keycard-tech/keycard-shell/hardware/shell/serial_run/CERTIFICATION-OFFICIALCERTIFICATES/Formal/EMC/2511B0394SHA-V1.pdf

This Verification is for the exclusive use of Intertek's client and is provided pursuant to the agreement between Intertek and its Client. Intertek's responsibility and liability are limited to the terms and conditions of the agreement. Intertek assumes no liability to any party, other than to the Client in accordance with the agreement, for any loss, expense or damage occasioned by the use of this Verification. Only the Client is authorized to permit copying or distribution of this Verification. Any use of the Intertek name or one of its marks for the sale or advertisement of the tested material, product or service must first be approved in writing by Intertek. The observations and test/inspection results referenced in this Verification are relevant only to the sample tested/inspected. This Verification by itself does not imply that the material, product, or service is or has ever been under an Intertek certification program.

Intertek | Page 1 of 1 | GFT-OP-11a (09 March 2024)

# Test Verification of Conformity

# Verification Number: 2511B0394SHA-V1

Applicant Name & Address: | Status Research & Development GmbH Baarerstrasse 10, 6302 Zug, Switzerland
Product Description: | Smart card adapter
Ratings & Principle Characteristics: | Input: 5VDC 1A (USBc), Battery: 3.7VDC 800mAh
Models/Type References: | Shell
Brand Names: | Keycard
Specification<s>/Standards: | 47CFR Part 15 (2024) ANSI C63.4 (2014) +A1 (2017) ICES-003 Issue 7
Verification Issuing Office Name & Address: | Intertek Testing Services (Shanghai FTZ) Co., Ltd. Building No.86, 1198 Qinzhou Road (North), Caohejing Development Zone, Shanghai 200233, China
Date of Tests: | October 22, 2025
Test Report Number(s): | 2511B0394SHA-001

# Signature

# Name: Edwin Xu Position: Assistant Manager Date: November 26, 2025

On the basis of the tests undertaken, the sample<s> of the below product has been tested by an accredited 3rd party laboratory in accordance to the referenced specification<s>/standard<s> at the time the tests were carried out. This verification is part of the full test report<s> and should be read in conjunction with it <them>.
