keycard-tech/keycard-shell/hardware/shell/serial_run/MECHANICAL/3Ddrawings/2282-008-WINDOWADHESIVE-V01-20250630.STEP

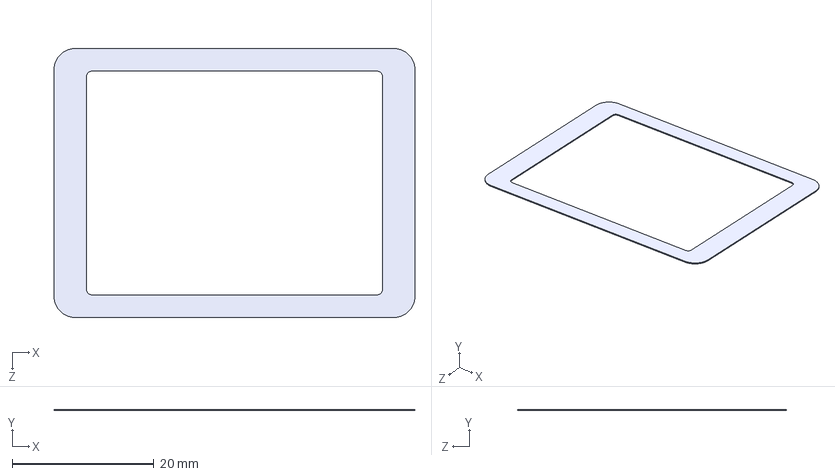
[picture p22: CAD file, 2026-01-29]
hardware/shell/serial_run/MECHANICAL/3Ddrawings/2282-008-WINDOWADHESIVE-V01-20250630.STEP
51.0 x 0.2 x 38.0 mm
