keycard-tech/keycard-shell/hardware/shell/serial_run/MECHANICAL/3Ddrawings/2282-012-WINDOWPROTECTION-V01-20250718.STEP

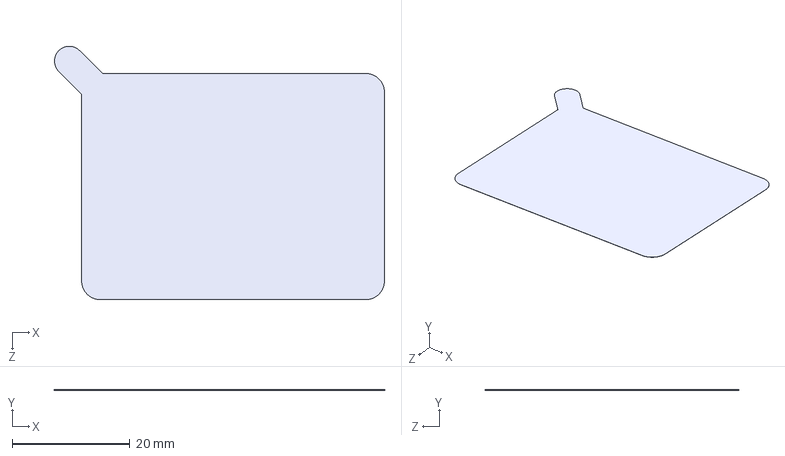
[picture p24: CAD file, 2026-01-29]
hardware/shell/serial_run/MECHANICAL/3Ddrawings/2282-012-WINDOWPROTECTION-V01-20250718.STEP
56.0 x 0.03 x 43.0 mm
