keycard-tech/keycard-shell/hardware/shell/serial_run/MECHANICAL/2282-011-CAMERAFOAM-V02-20250630.PDF

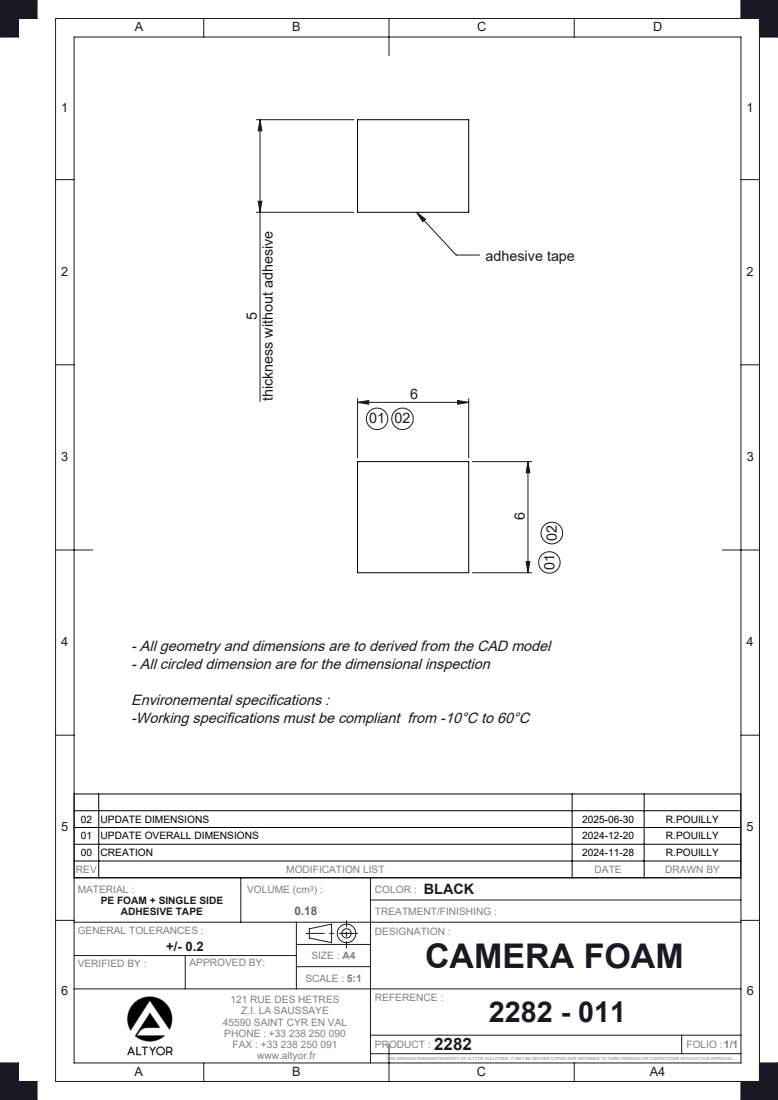
[picture p41: page 1]
adhesive tape; SCALE :; SIZE : A4; TREATMENT/FINISHING :

thickness without adhesive

- All geometry and dimensions are to derived from the CAD model
- All circled dimension are for the dimensional inspection
Environemental specifications :
-Working specifications must be compliant from -10°C to 60°C

02 | UPDATE DIMENSIONS | 2025-06-30 | R.POUILLY
01 | UPDATE OVERALL DIMENSIONS | 2024-12-20 | R.POUILLY
00 | CREATION | 2024-11-28 | R.POUILLY
REV | MODIFICATION LIST | DATE | DRAWN BY
MATERIAL : PE FOAM + SINGLE SIDE ADHESIVE TAPE | VOLUME (cm3) : 0.18 | BLACK COLOR :

GENERAL TOLERANCES : +/- 0.2 | | DESIGNATION : CAMERA FOAM

VERIFIED BY : | APPROVED BY:

121 RUE DES HETRES Z.I. LA SAUSSAYE 45590 SAINT CYR EN VAL PHONE : +33 238 250 090 FAX : +33 238 250 091 www.altyor.fr | REFERENCE : 2282 - 011

PRODUCT : | FOLIO : 1/1

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
