keycard-tech/keycard-shell/hardware/shell/serial_run/MECHANICAL/2282-012-WINDOWPROTECTION-V01-20250718.PDF

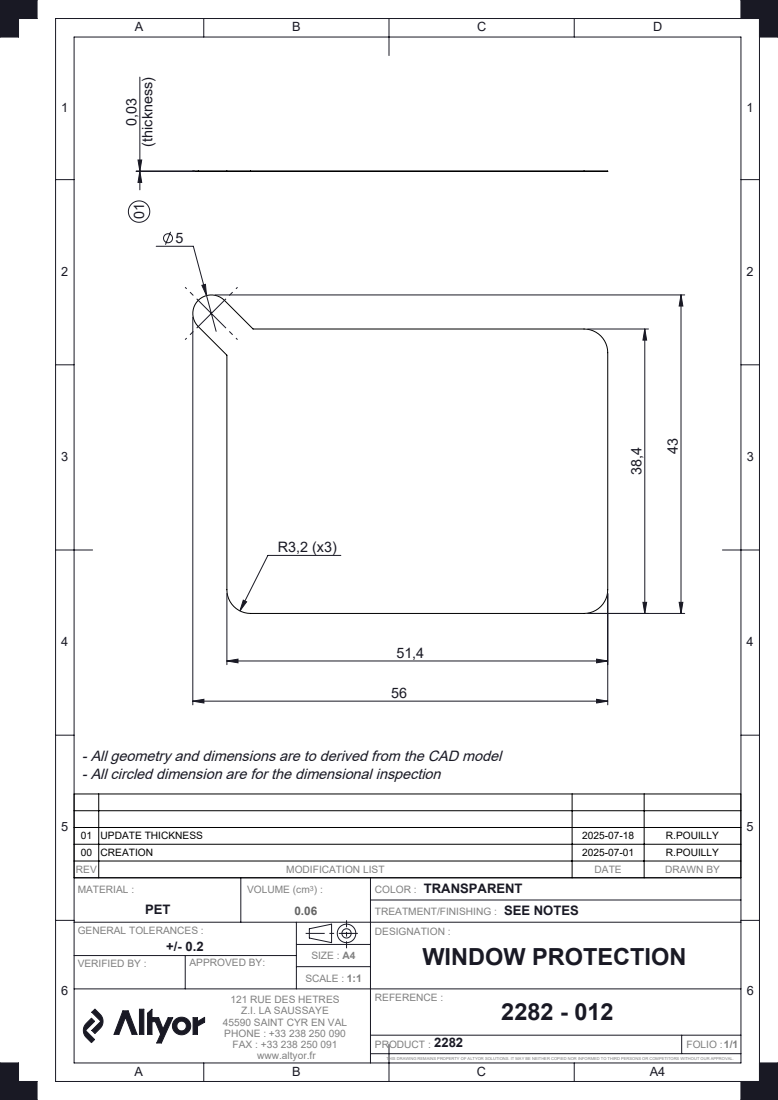
[picture p42: page 1]
SCALE :; SIZE : A4; MATERIAL :; VOLUME (cm3) :; COLOR :; TREATMENT/FINISHING :; PET; SEE NOTES

- All circled dimension are for the dimensional inspection 01

- All geometry and dimensions are to derived from the CAD model

01 | UPDATE THICKNESS | 2025-07-18 | R.POUILLY
00 | CREATION | 2025-07-01 | R.POUILLY
REV | MODIFICATION LIST | DATE | DRAWN BY

GENERAL TOLERANCES : +/- 0.2 | | DESIGNATION : WINDOW PROTECTION

VERIFIED BY : | APPROVED BY:

121 RUE DES HETRES Z.I. LA SAUSSAYE 45590 SAINT CYR EN VAL PHONE : +33 238 250 090 FAX : +33 238 250 091 www.altyor.fr | REFERENCE : 2282 - 012

2282 PRODUCT : | FOLIO : 1/1

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
