keycard-tech/keycard-shell/hardware/shell/serial_run/MECHANICAL/2282-005-KEYBOARDSLEEVE-V07-20250325.PDF

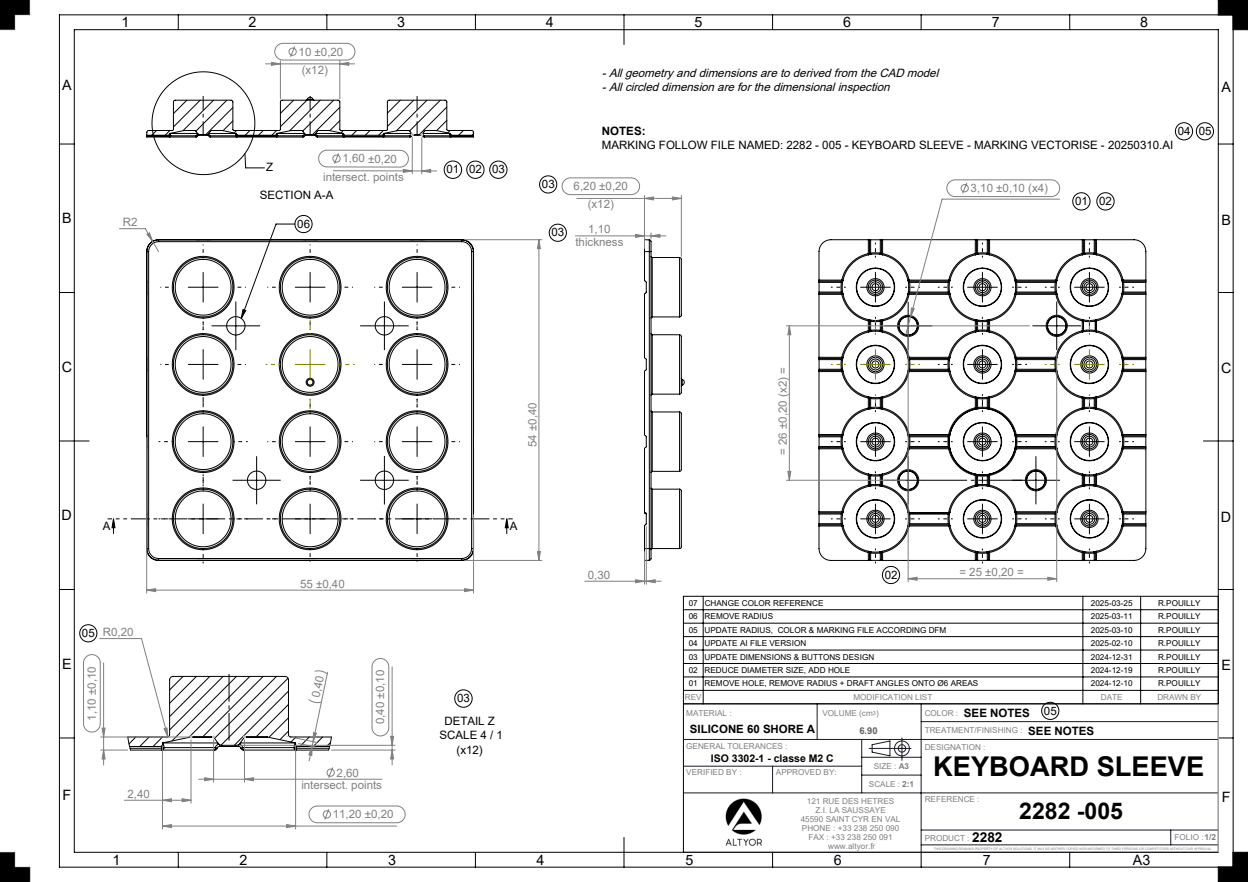
[picture p43: page 1]
1,60 ±0,20 intersect. points SECTION A-A; intersect. points 2,40; DETAIL Z SCALE 4 / 1; SILICONE 60 SHORE A; SEE NOTES; TREATMENT/FINISHING :; VOLUME (cm3); COLOR :; MATERIAL :; SIZE : A3; SCALE :

- All geometry and dimensions are to derived from the CAD model
- All circled dimension are for the dimensional inspection

NOTES:
MARKING FOLLOW FILE NAMED: 2282 - 005 - KEYBOARD SLEEVE - MARKING VECTORISE - 20250310.AI

07 | CHANGE COLOR REFERENCE | 2025-03-25 | R.POUILLY
06 | REMOVE RADIUS | 2025-03-11 | R.POUILLY
05 | UPDATE RADIUS, COLOR & MARKING FILE ACCORDING DFM | 2025-03-10 | R.POUILLY
04 | UPDATE AI FILE VERSION | 2025-02-10 | R.POUILLY
03 | UPDATE DIMENSIONS & BUTTONS DESIGN | 2024-12-31 | R.POUILLY
02 | REDUCE DIAMETER SIZE, ADD HOLE | 2024-12-19 | R.POUILLY
01 | REMOVE HOLE, REMOVE RADIUS + DRAFT ANGLES ONTO Ø6 AREAS | 2024-12-10 | R.POUILLY
REV | MODIFICATION LIST | DATE | DRAWN BY

GENERAL TOLERANCES : ISO 3302-1 - classe M2 C | | DESIGNATION : KEYBOARD SLEEVE

VERIFIED BY : | APPROVED BY:

121 RUE DES HETRES Z.I. LA SAUSSAYE 45590 SAINT CYR EN VAL PHONE : +33 238 250 090 FAX : +33 238 250 091 www.altyor.fr | REFERENCE : 2282 -005

2282 PRODUCT : | FOLIO : 1/2

THIS DRAWING REMAINS PROPERTY OF ALTYOR SOLUTIONS. IT MAY BE NEITHER COPIED NOR INFORMED TO THIRD PERSONS OR COMPETITORS WITHOUT OUR APPROVAL.

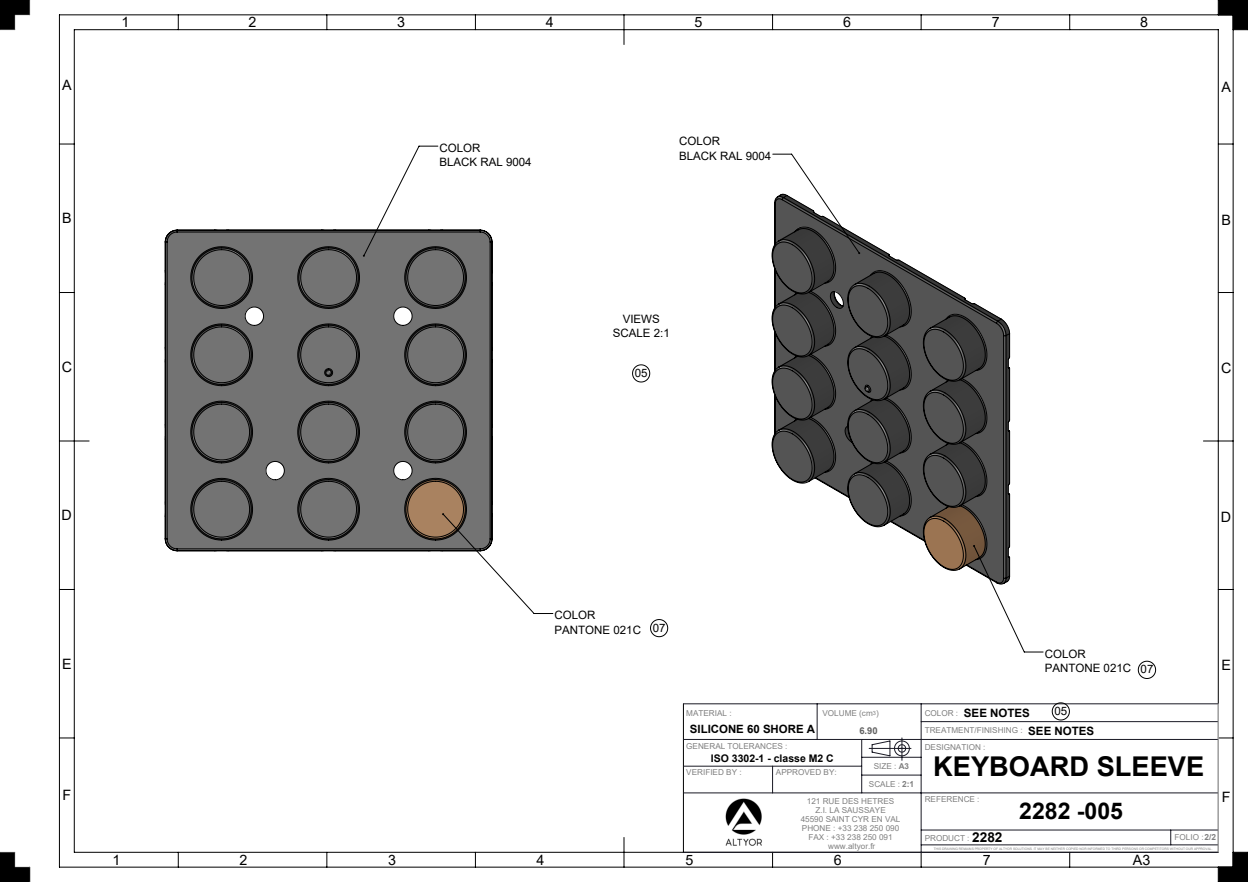
[picture p44: page 2]
BLACK RAL 9004; PANTONE 021C; SCALE 2:1; SILICONE 60 SHORE A; SEE NOTES; TREATMENT/FINISHING :; VOLUME (cm3); COLOR :; MATERIAL :; SIZE : A3; SCALE :

GENERAL TOLERANCES : ISO 3302-1 - classe M2 C | | | DESIGNATION : KEYBOARD SLEEVE

VERIFIED BY : | APPROVED BY:

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

2282 PRODUCT : | FOLIO : 2/2

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
