keycard-tech/keycard-shell/hardware/shell/serial_run/MECHANICAL/2282-010-CAMERAWINDOWADHESIVE-V00-20241128.PDF

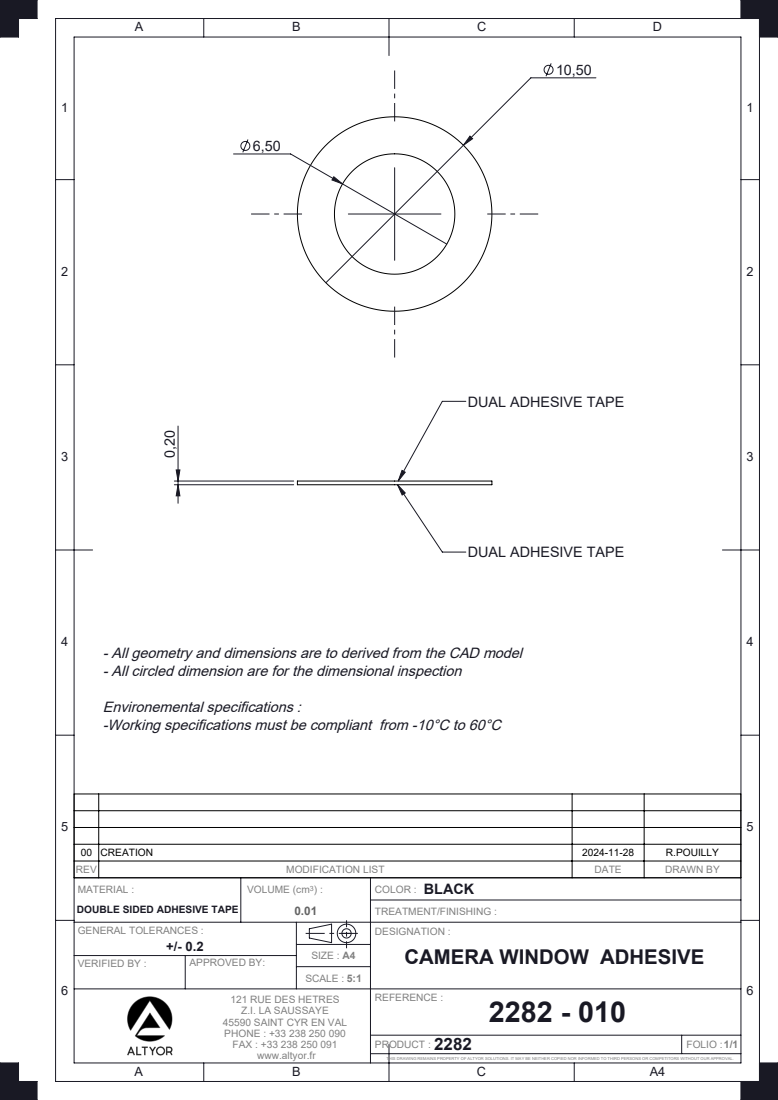
[picture p45: page 1]
SCALE :; SIZE : A4; TREATMENT/FINISHING :

DUAL ADHESIVE TAPE

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

00 | CREATION | 2024-11-28 | R.POUILLY
REV | MODIFICATION LIST | DATE | DRAWN BY
MATERIAL : DOUBLE SIDED ADHESIVE TAPE | VOLUME (cm3) : 0.01 | BLACK COLOR :

GENERAL TOLERANCES : +/- 0.2 | | DESIGNATION : CAMERA WINDOW ADHESIVE

VERIFIED BY : | APPROVED BY:

121 RUE DES HETRES Z.I. LA SAUSSAYE 45590 SAINT CYR EN VAL PHONE : +33 238 250 090 FAX : +33 238 250 091 www.altyor.fr | REFERENCE : 2282 - 010

PRODUCT : | FOLIO : 1/1

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
