keycard-tech/keycard-shell/hardware/shell/serial_run/ELECTRONIC/KCP-2282-SCH-V3.8/KCP-2282-600SCHV3.9.PDF

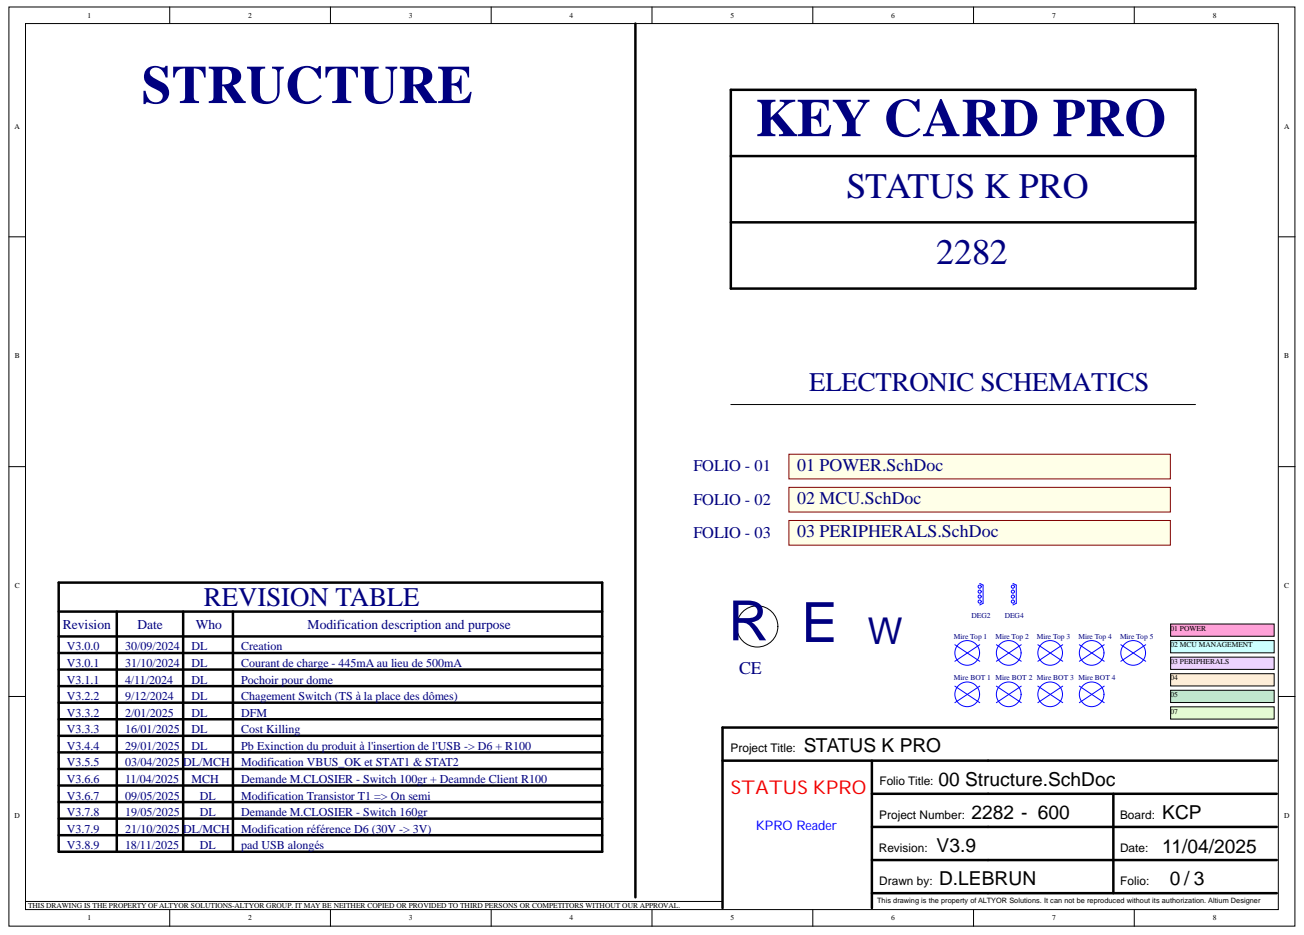
[picture p46: page 1]

Revision | Date | Who | Modification description and purpose

V3.0.0 | 30/09/2024 | DL | Creation

Mire BOT 1 Mire BOT 2

Mire BOT 3 Mire BOT 4

V3.3.2 | 2/01/2025 | DL | DFM
V3.3.3 | 16/01/2025 | DL | Cost Killing
V3.4.4 | 29/01/2025 | DL | Pb Exinction du produit à l'insertion de l'USB -> D6 + R100
V3.5.5 | 03/04/2025 DL/MCH | | Modification VBUS_OK et STAT1 & STAT2
V3.6.6 | 11/04/2025 | MCH | Demande M.CLOSIER - Switch 100gr + Deamnde Client R100
V3.6.7 | 09/05/2025 | DL | Modification Transistor T1 => On semi
V3.7.8 | 19/05/2025 | DL | Demande M.CLOSIER - Switch 160gr
V3.7.9 | 21/10/2025 DL/MCH | | Modification référence D6 (30V -> 3V)
V3.8.9 | 18/11/2025 | DL | pad USB alongés

This drawing is the property of ALTYOR Solutions. It can not be reproduced without its authorization. Altium Designer

THIS DRAWING IS THE PROPERTY OF ALTYOR SOLUTIONS-ALTYOR GROUP. IT MAY BE NEITHER COPIED OR PROVIDED TO THIRD PERSONS OR COMPETITORS WITHOUT OUR APPROVAL.

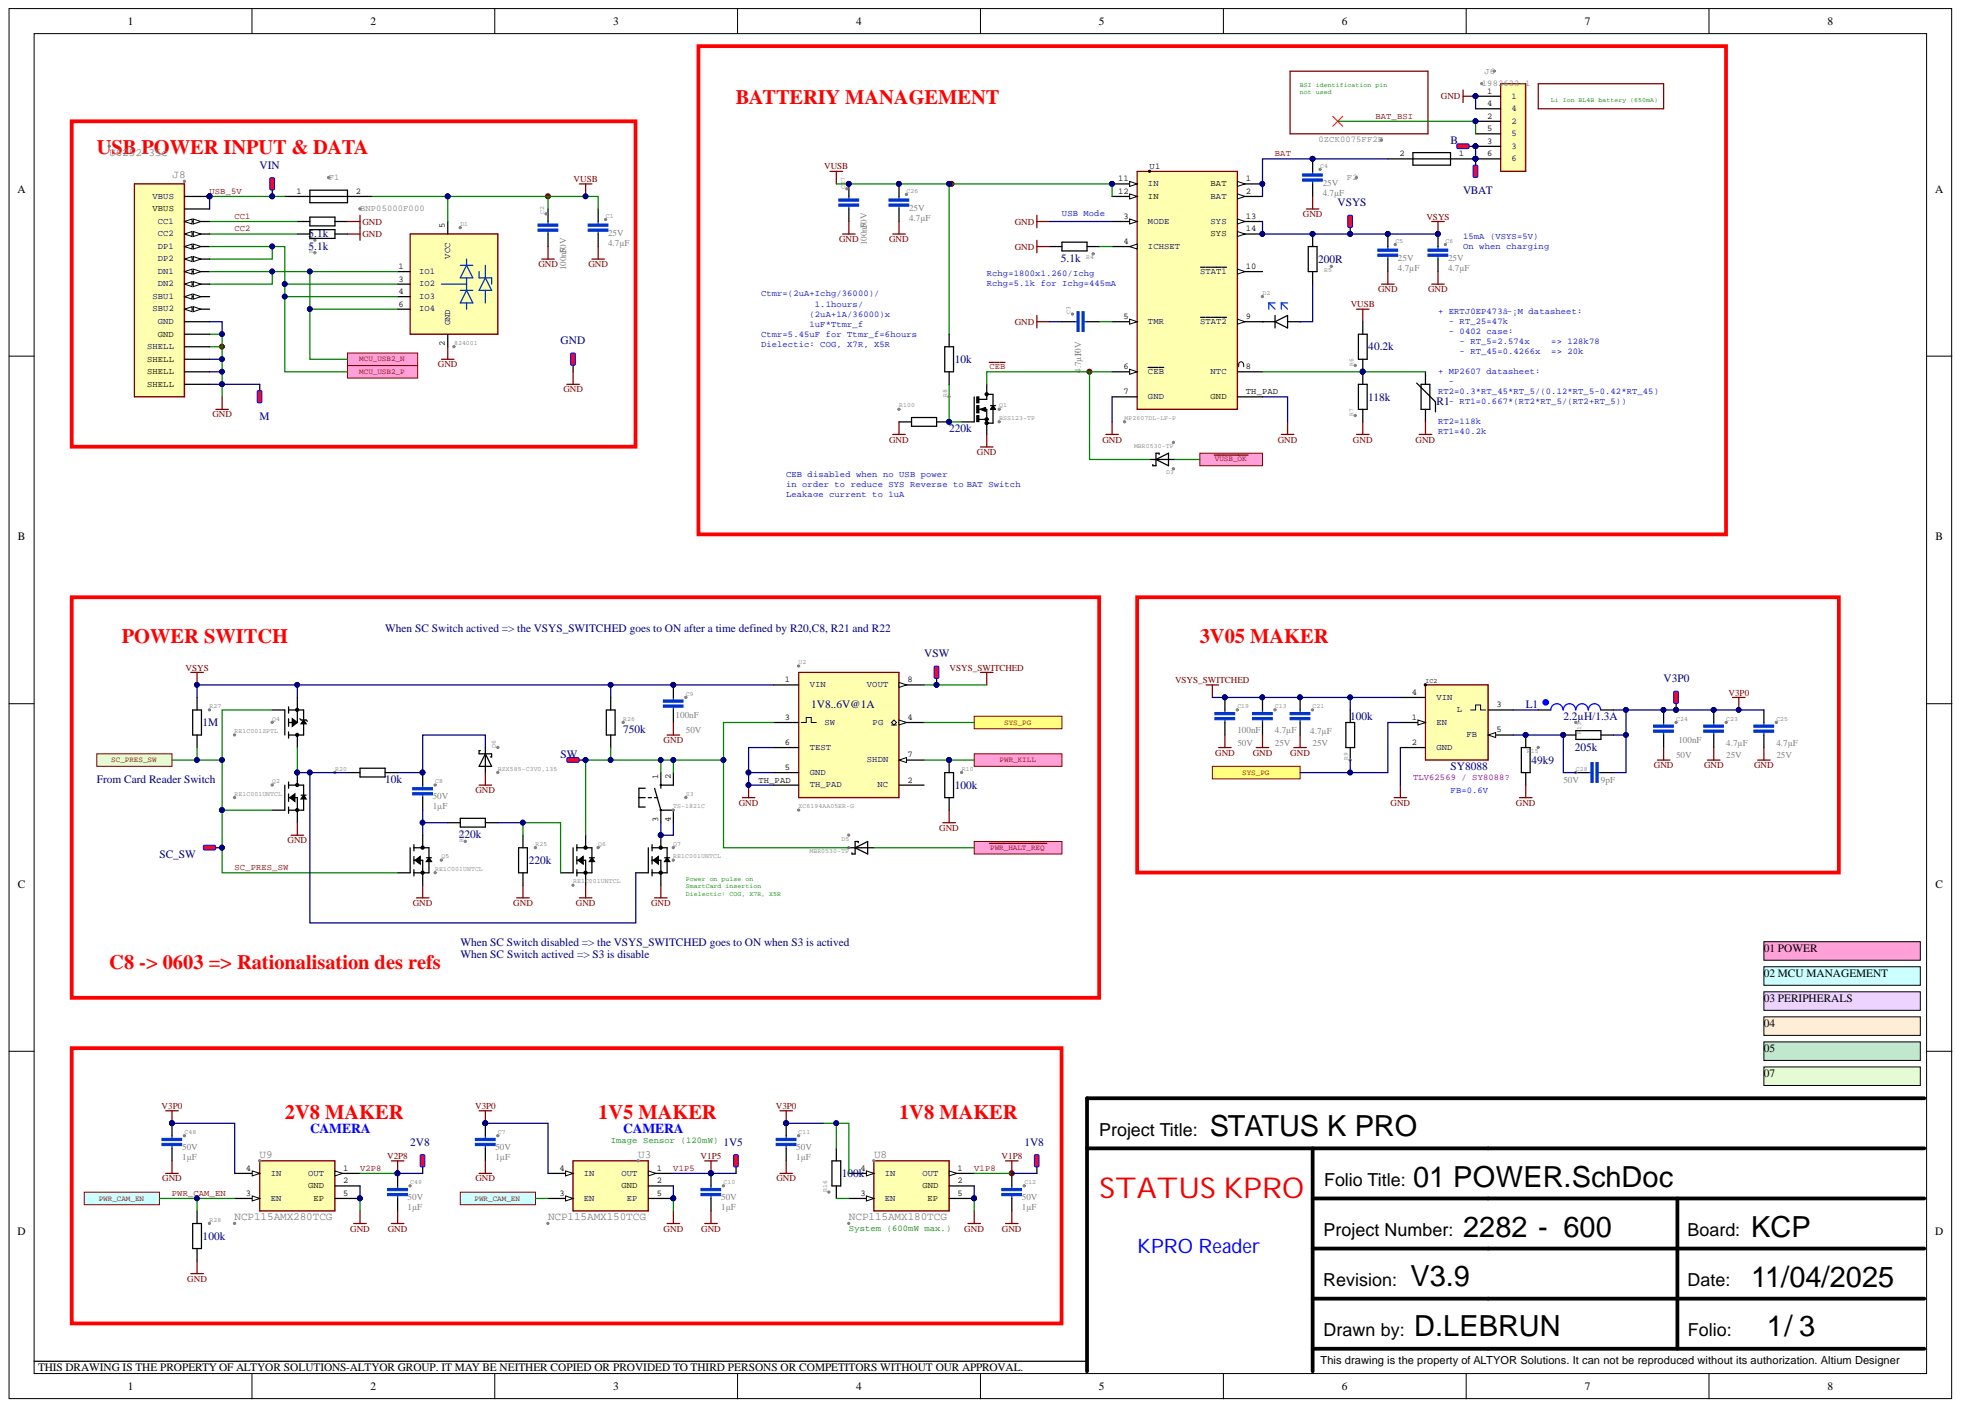
[picture p47: page 2]

USB POWER INPUT & DATA

D3 | VUSB_OK

CEB disabled when no USB power
in order to reduce SYS Reverse to BAT Switch
Leakage current to 1uA

When SC Switch actived => the VSYS_SWITCHED goes to ON after a time defined by R20,C8, R21 and R22

SC_PRES_SW
From Card Reader Switch

Power on pulse on
SmartCard insertion
Dielectic: COG, X7R, X5R

When SC Switch disabled => the VSYS_SWITCHED goes to ON when S3 is actived
When SC Switch actived => S3 is disable

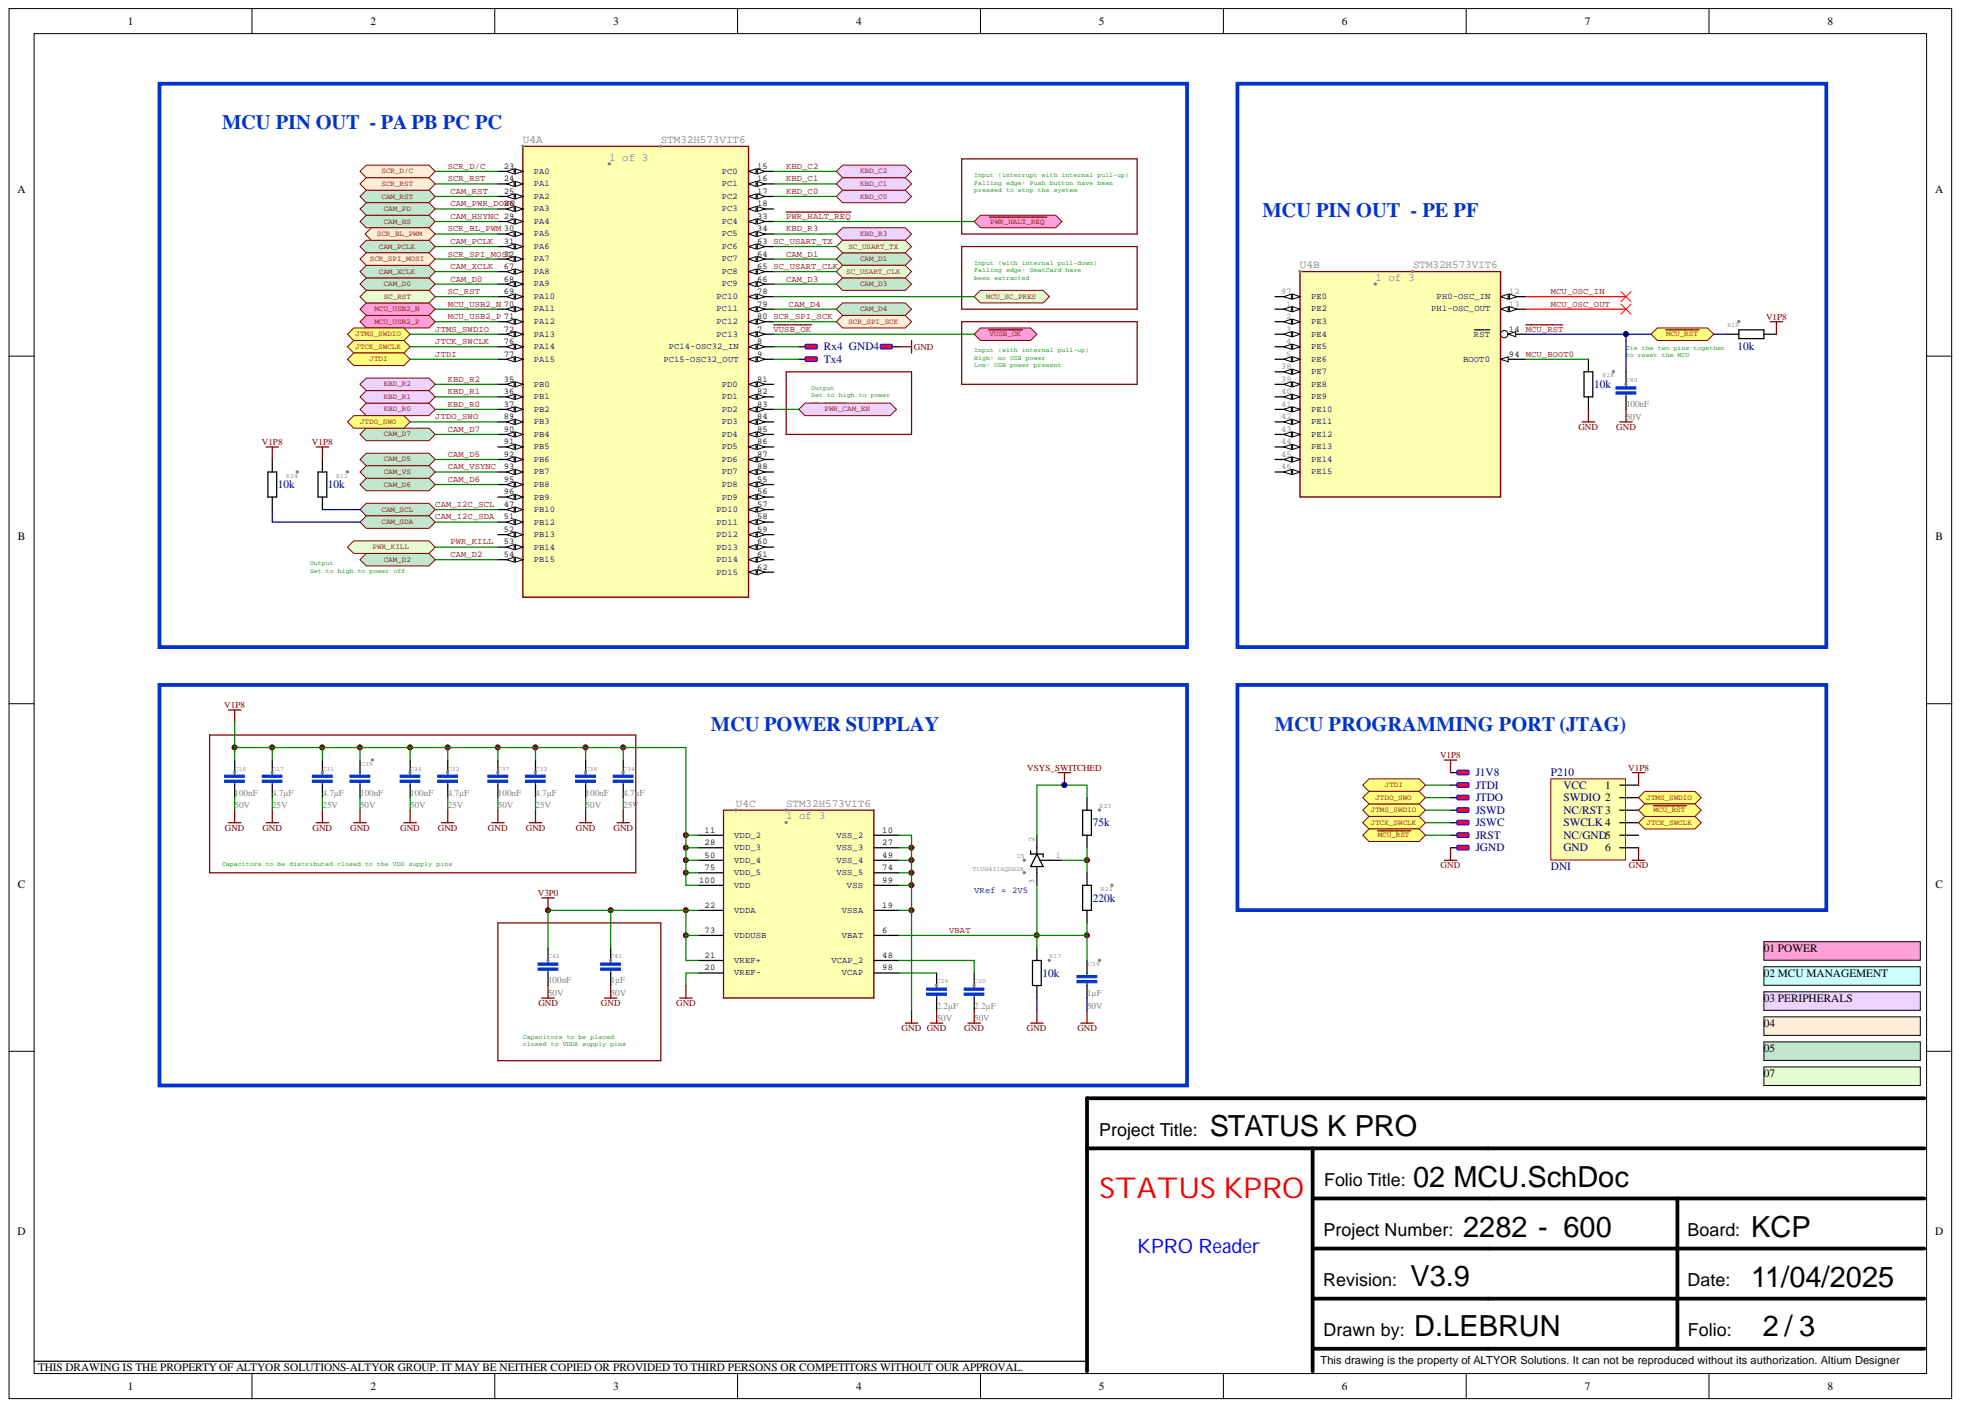
[picture p48: page 3]

MCU PIN OUT - PA PB PC PC

Input (interrupt with internal pull-up)
Falling edge: Push button have been
pressed to stop the system

MCU PIN OUT - PE PF

Input (with internal pull-down)
Falling edge: SmatCard have
been extracted

Input (with internal pull-up)
High: no USB power
Low: USB power present

Tie the two pins together
to reset the MCU

Output
Set to high to power
on camera
PWR_CAM_EN

Set to high to power off

Capacitors to be distributed closed to the VDD supply pins

VREF+ 21
VREF- 20

Capacitors to be placed
closed to VDDA supply pins

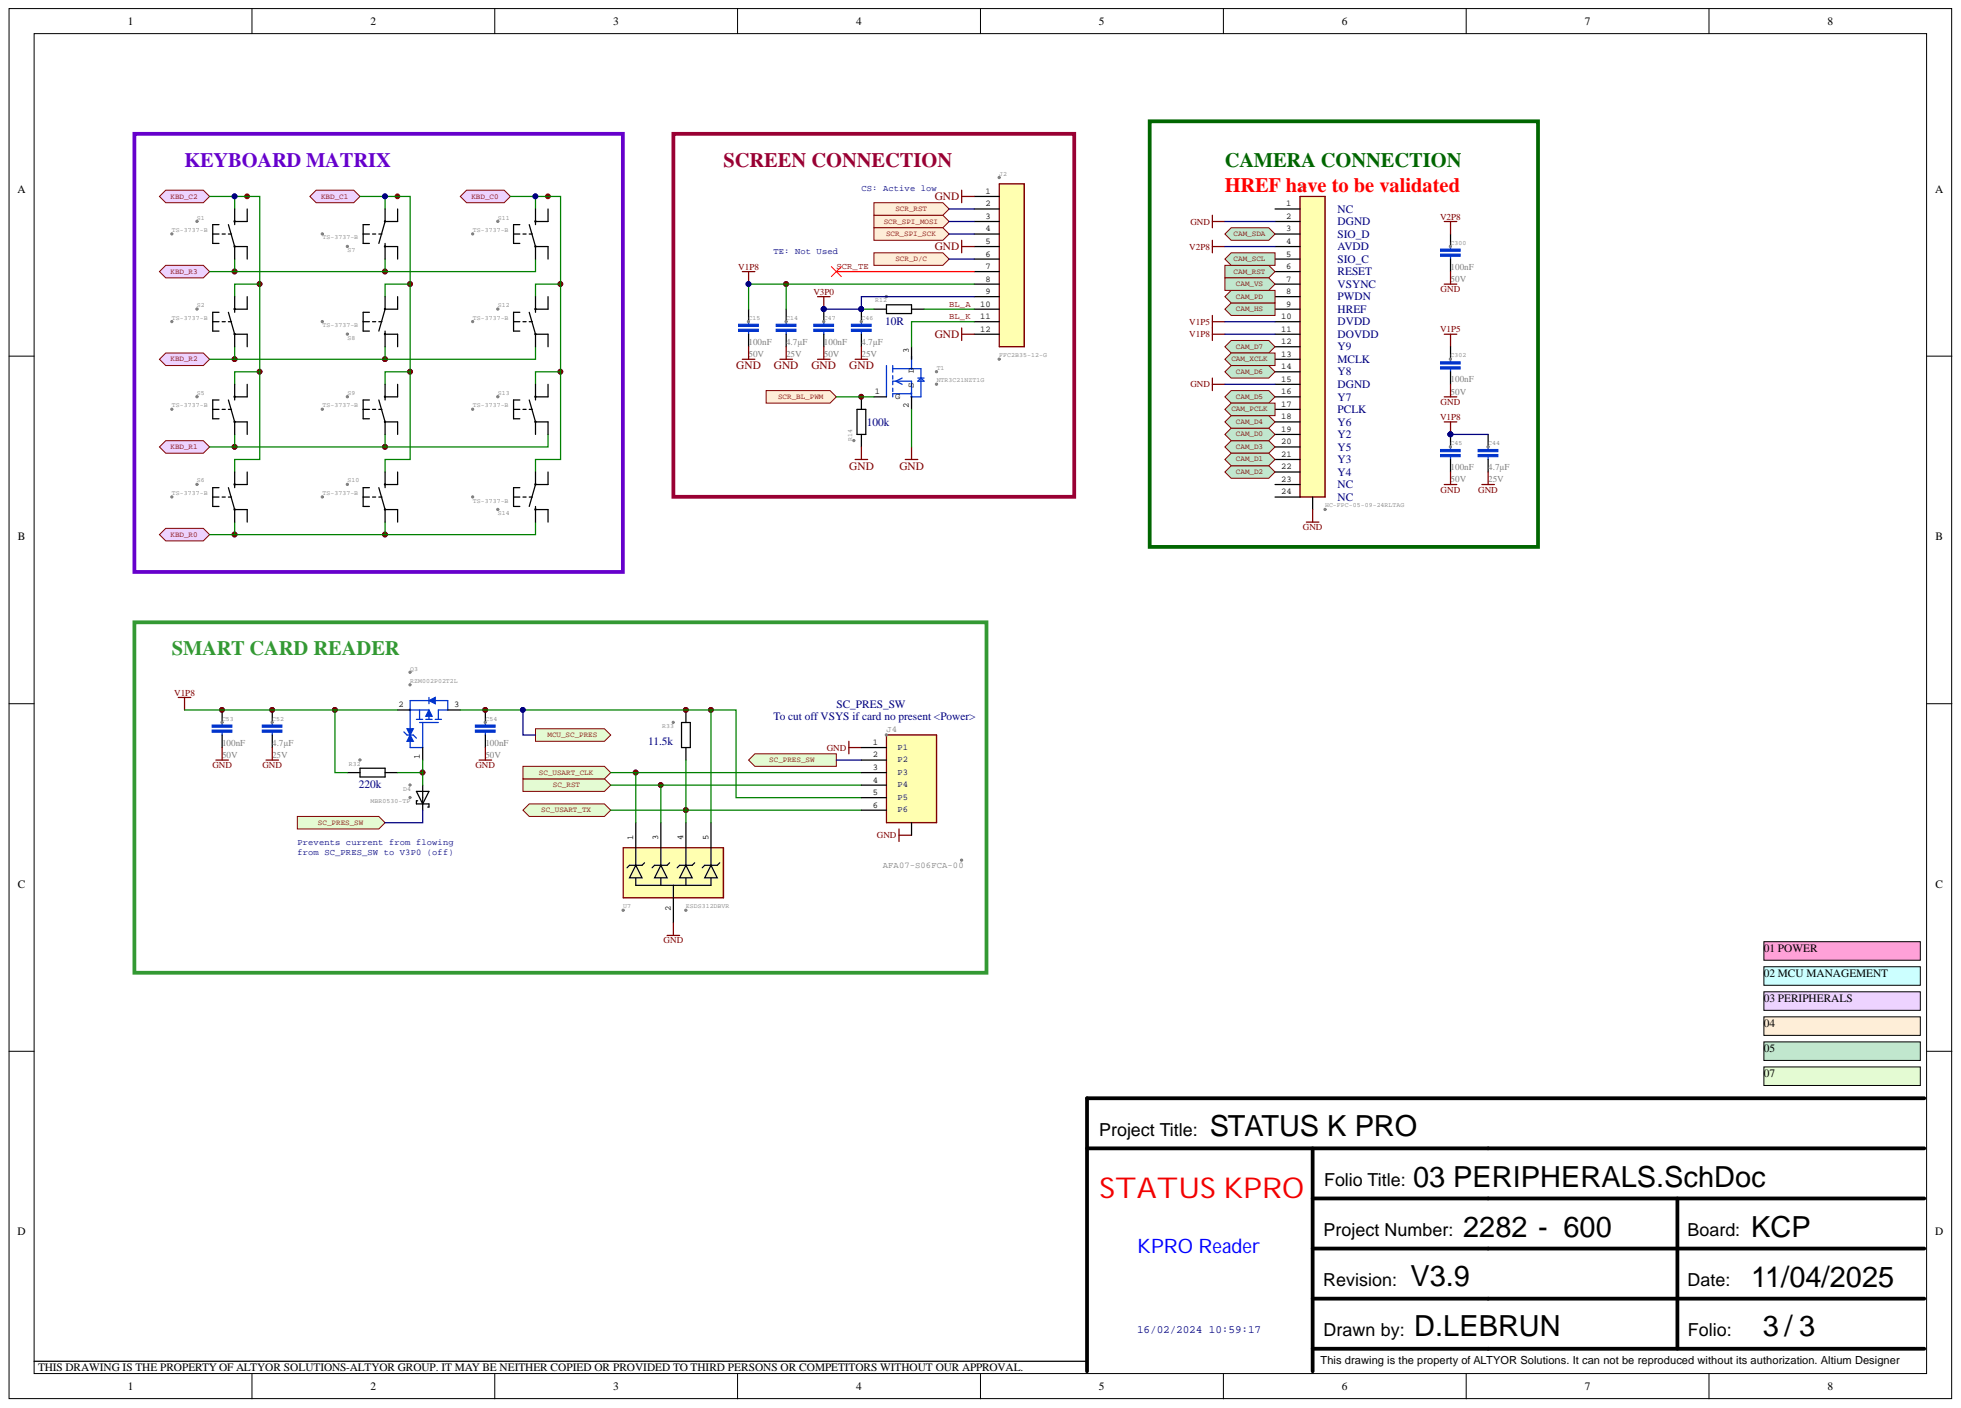
[picture p49: page 4]

HREF have to be validated

To cut off VSYS if card no present <Power>

Prevents current from flowing
from SC_PRES_SW to V3P0 (off)
