keycard-tech/keycard-shell/hardware/shell/prototype_P2/electronics/FLXandKCP2282/KCP-2282-600 SCH V3.1.PDF

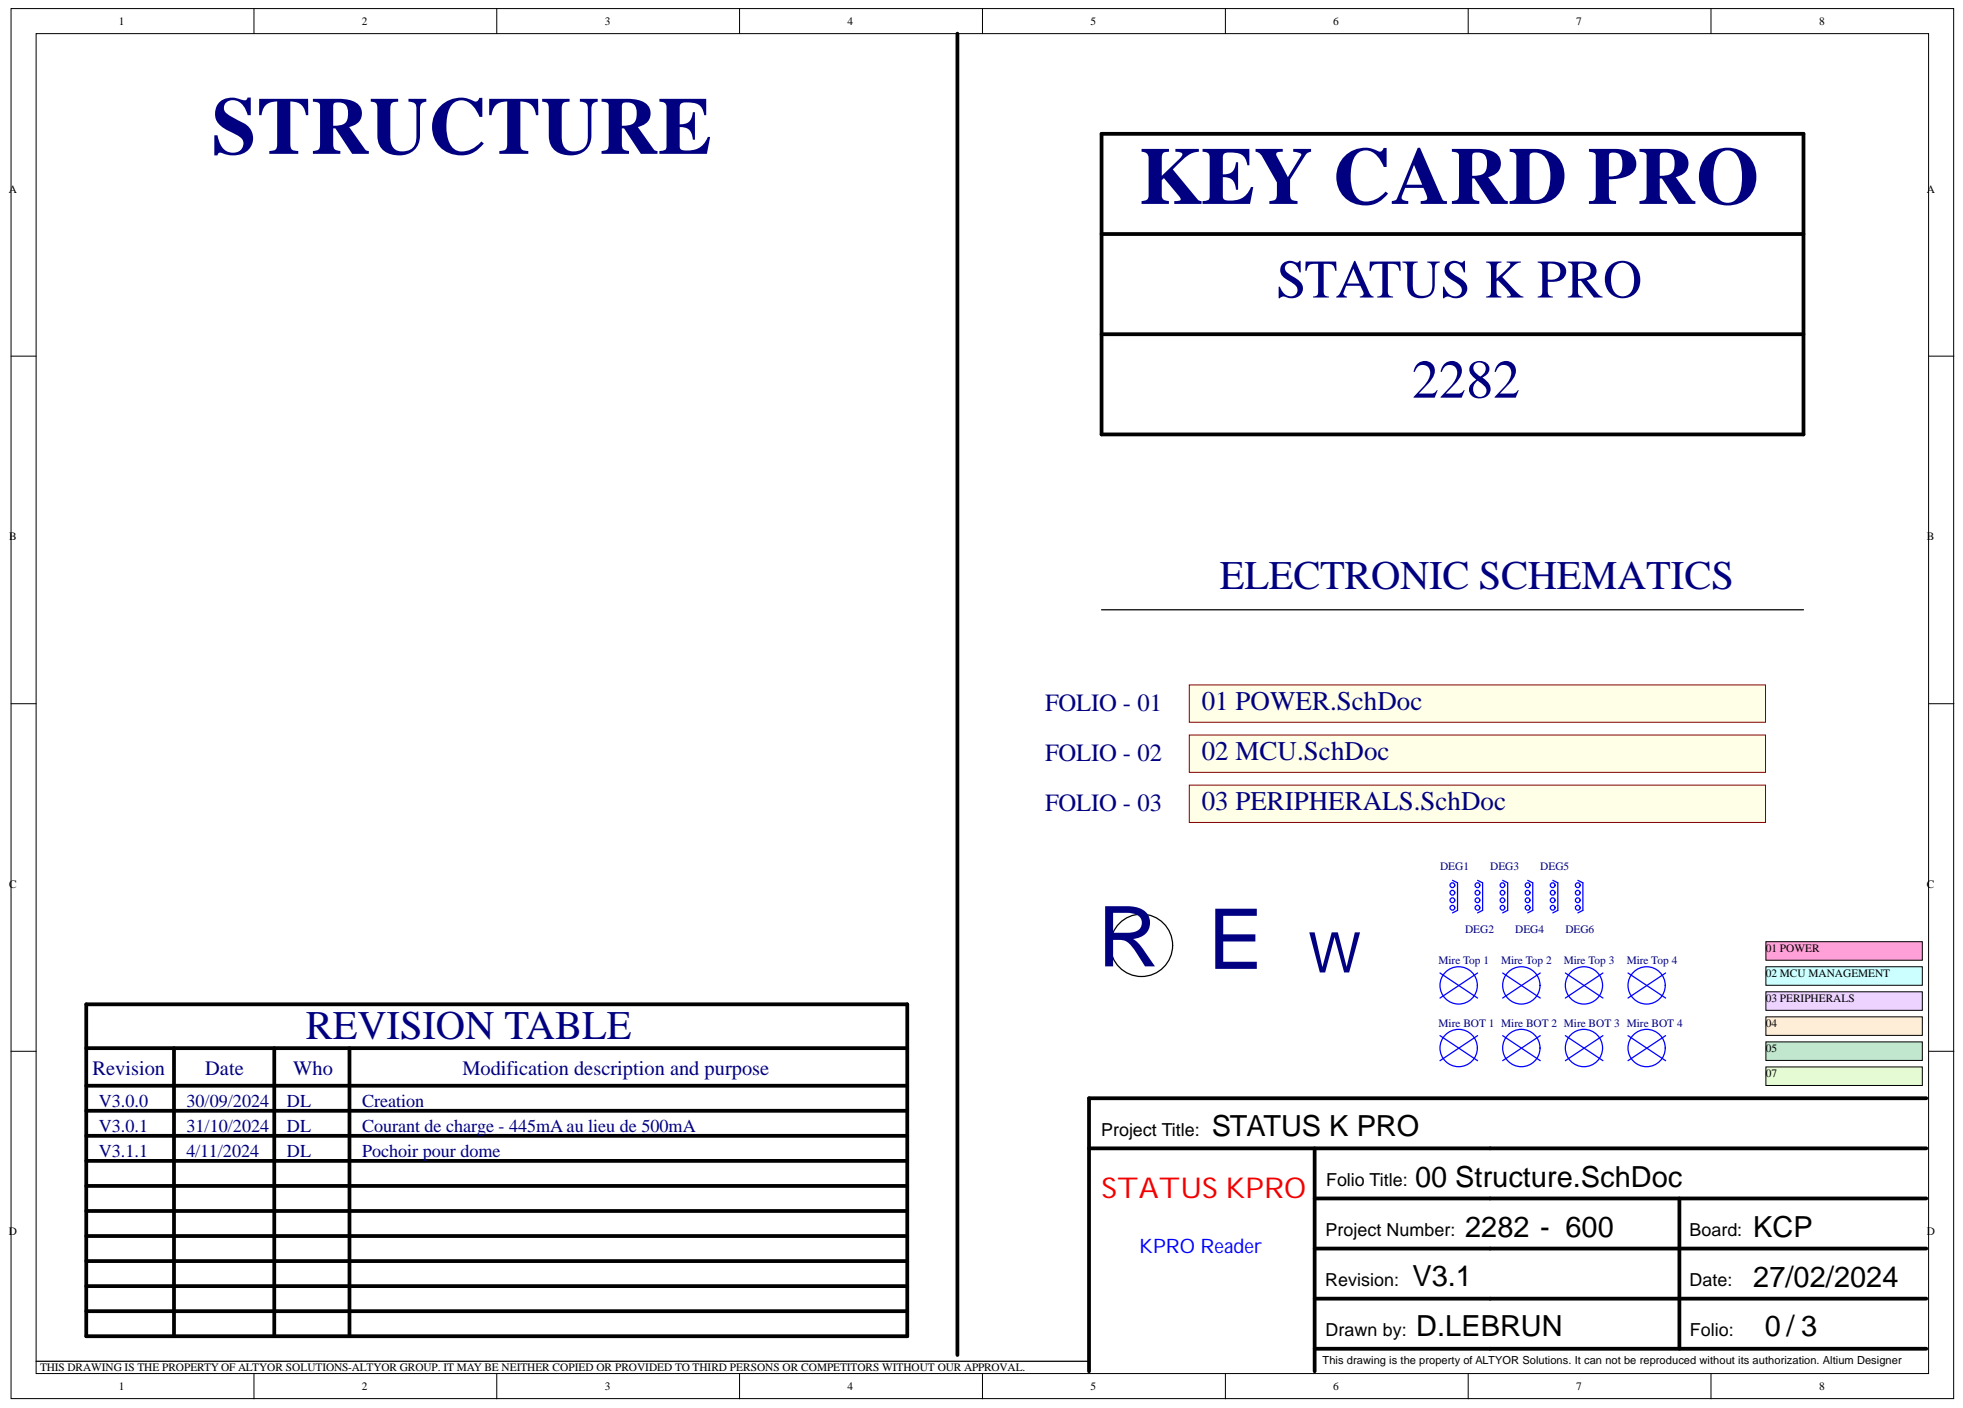
[picture p50: page 1]

Mire Top 1 Mire Top 2

Mire BOT 1 Mire BOT 2

Mire BOT 3 Mire BOT 4

Revision | Date | Who | Modification description and purpose

V3.0.0 | 30/09/2024 | DL | Creation
V3.0.1 | 31/10/2024 | DL | Courant de charge - 445mA au lieu de 500mA
V3.1.1 | 4/11/2024 | DL | Pochoir pour dome

This drawing is the property of ALTYOR Solutions. It can not be reproduced without its authorization. Altium Designer

THIS DRAWING IS THE PROPERTY OF ALTYOR SOLUTIONS-ALTYOR GROUP. IT MAY BE NEITHER COPIED OR PROVIDED TO THIRD PERSONS OR COMPETITORS WITHOUT OUR APPROVAL.

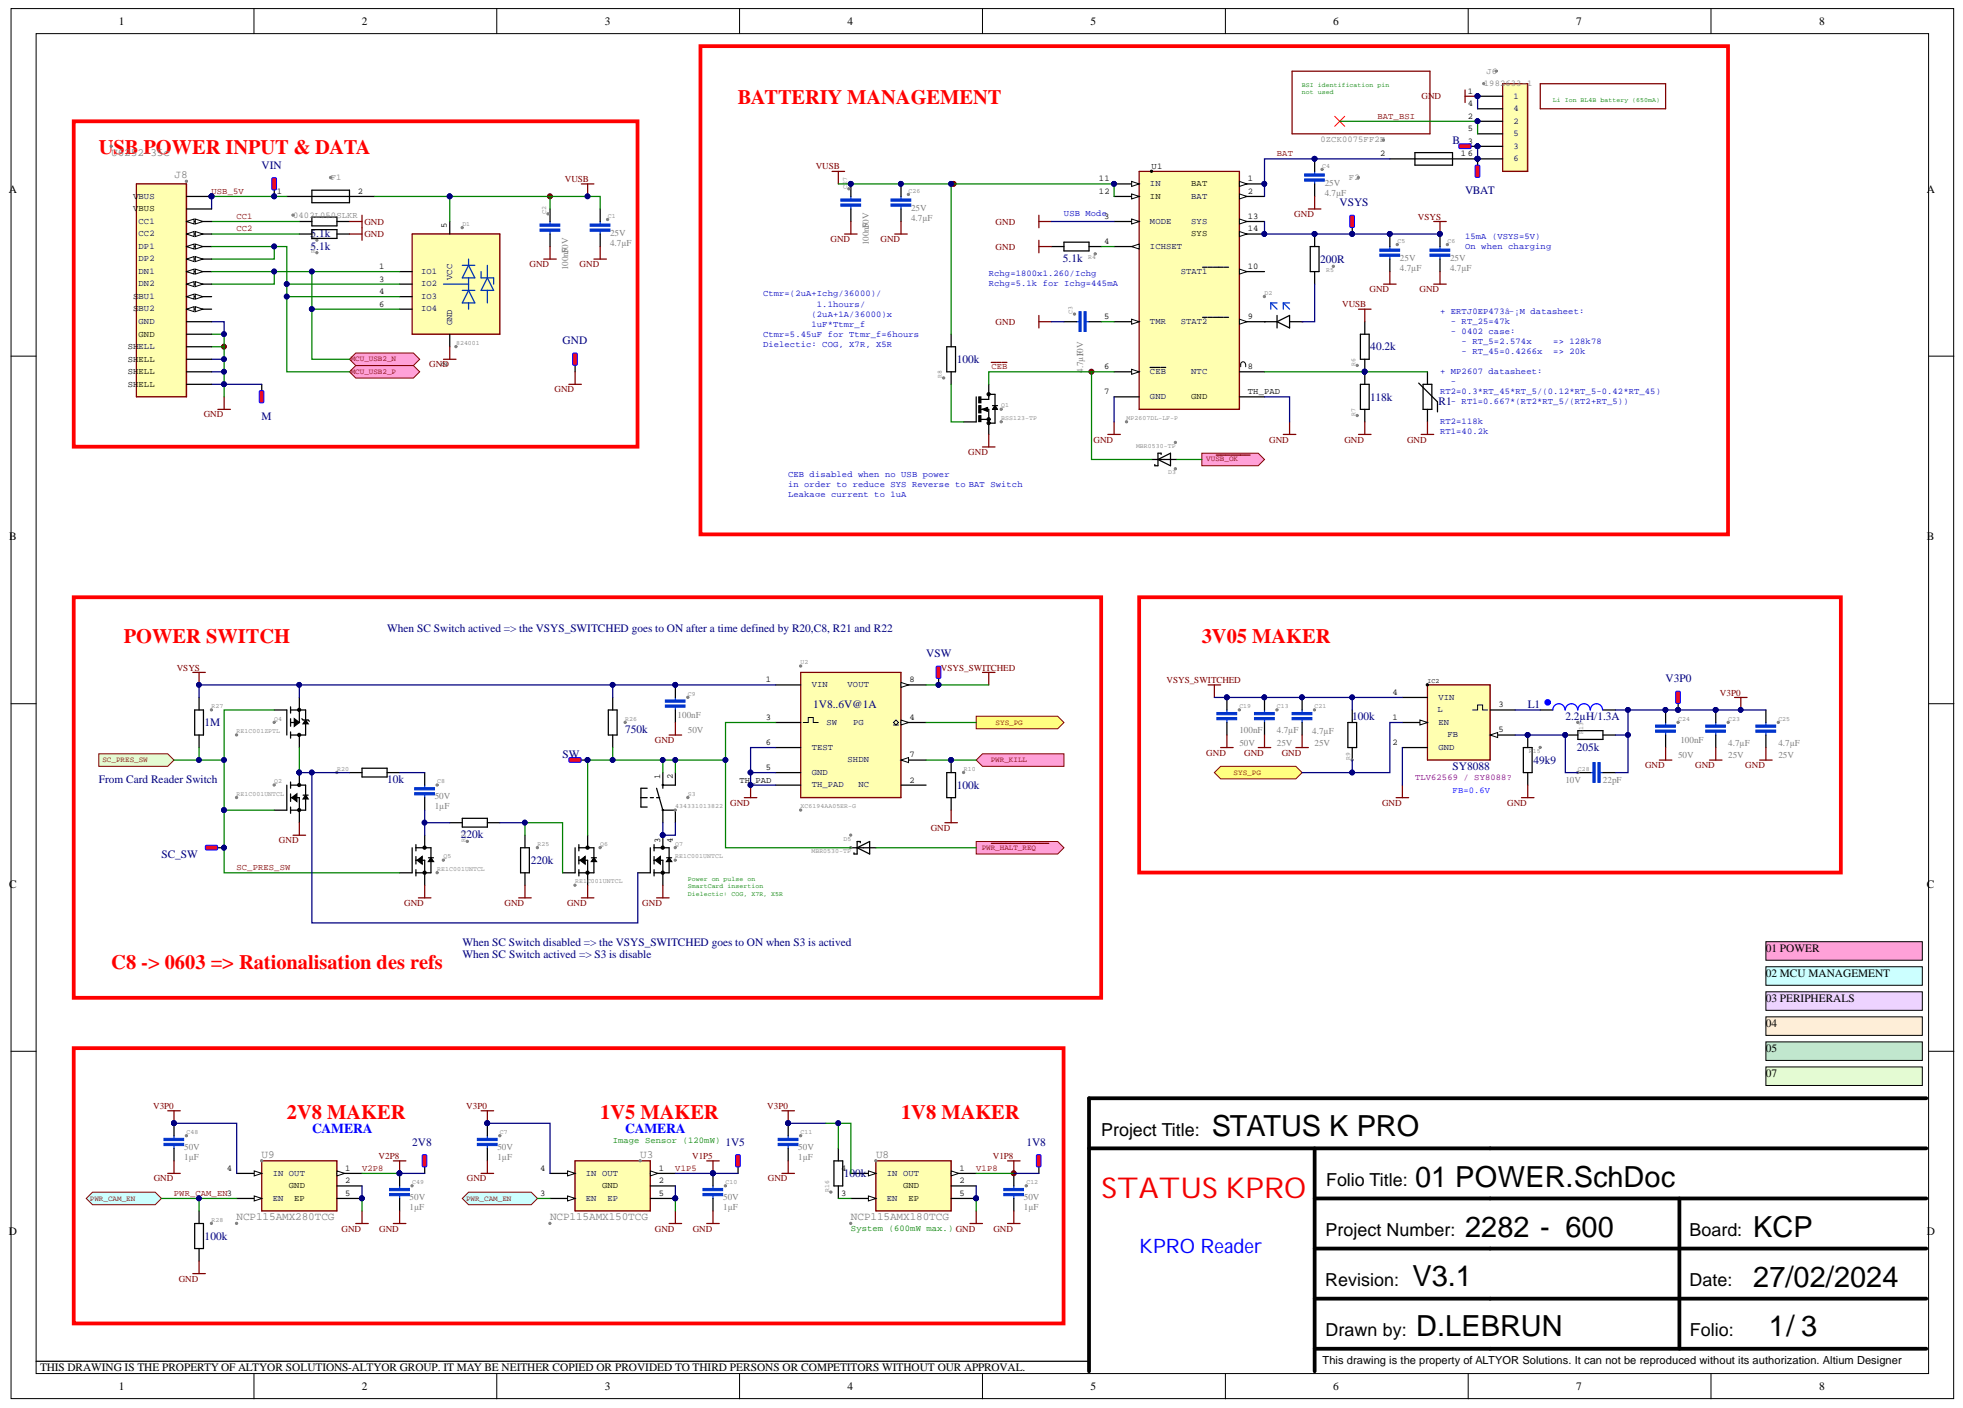
[picture p51: page 2]

USB POWER INPUT & DATA

CEB disabled when no USB power
in order to reduce SYS Reverse to BAT Switch
Leakage current to 1uA

When SC Switch actived => the VSYS_SWITCHED goes to ON after a time defined by R20,C8, R21 and R22

SC_PRES_SW
From Card Reader Switch

Power on pulse on
SmartCard insertion
Dielectic: COG, X7R, X5R

When SC Switch disabled => the VSYS_SWITCHED goes to ON when S3 is actived
When SC Switch actived => S3 is disable

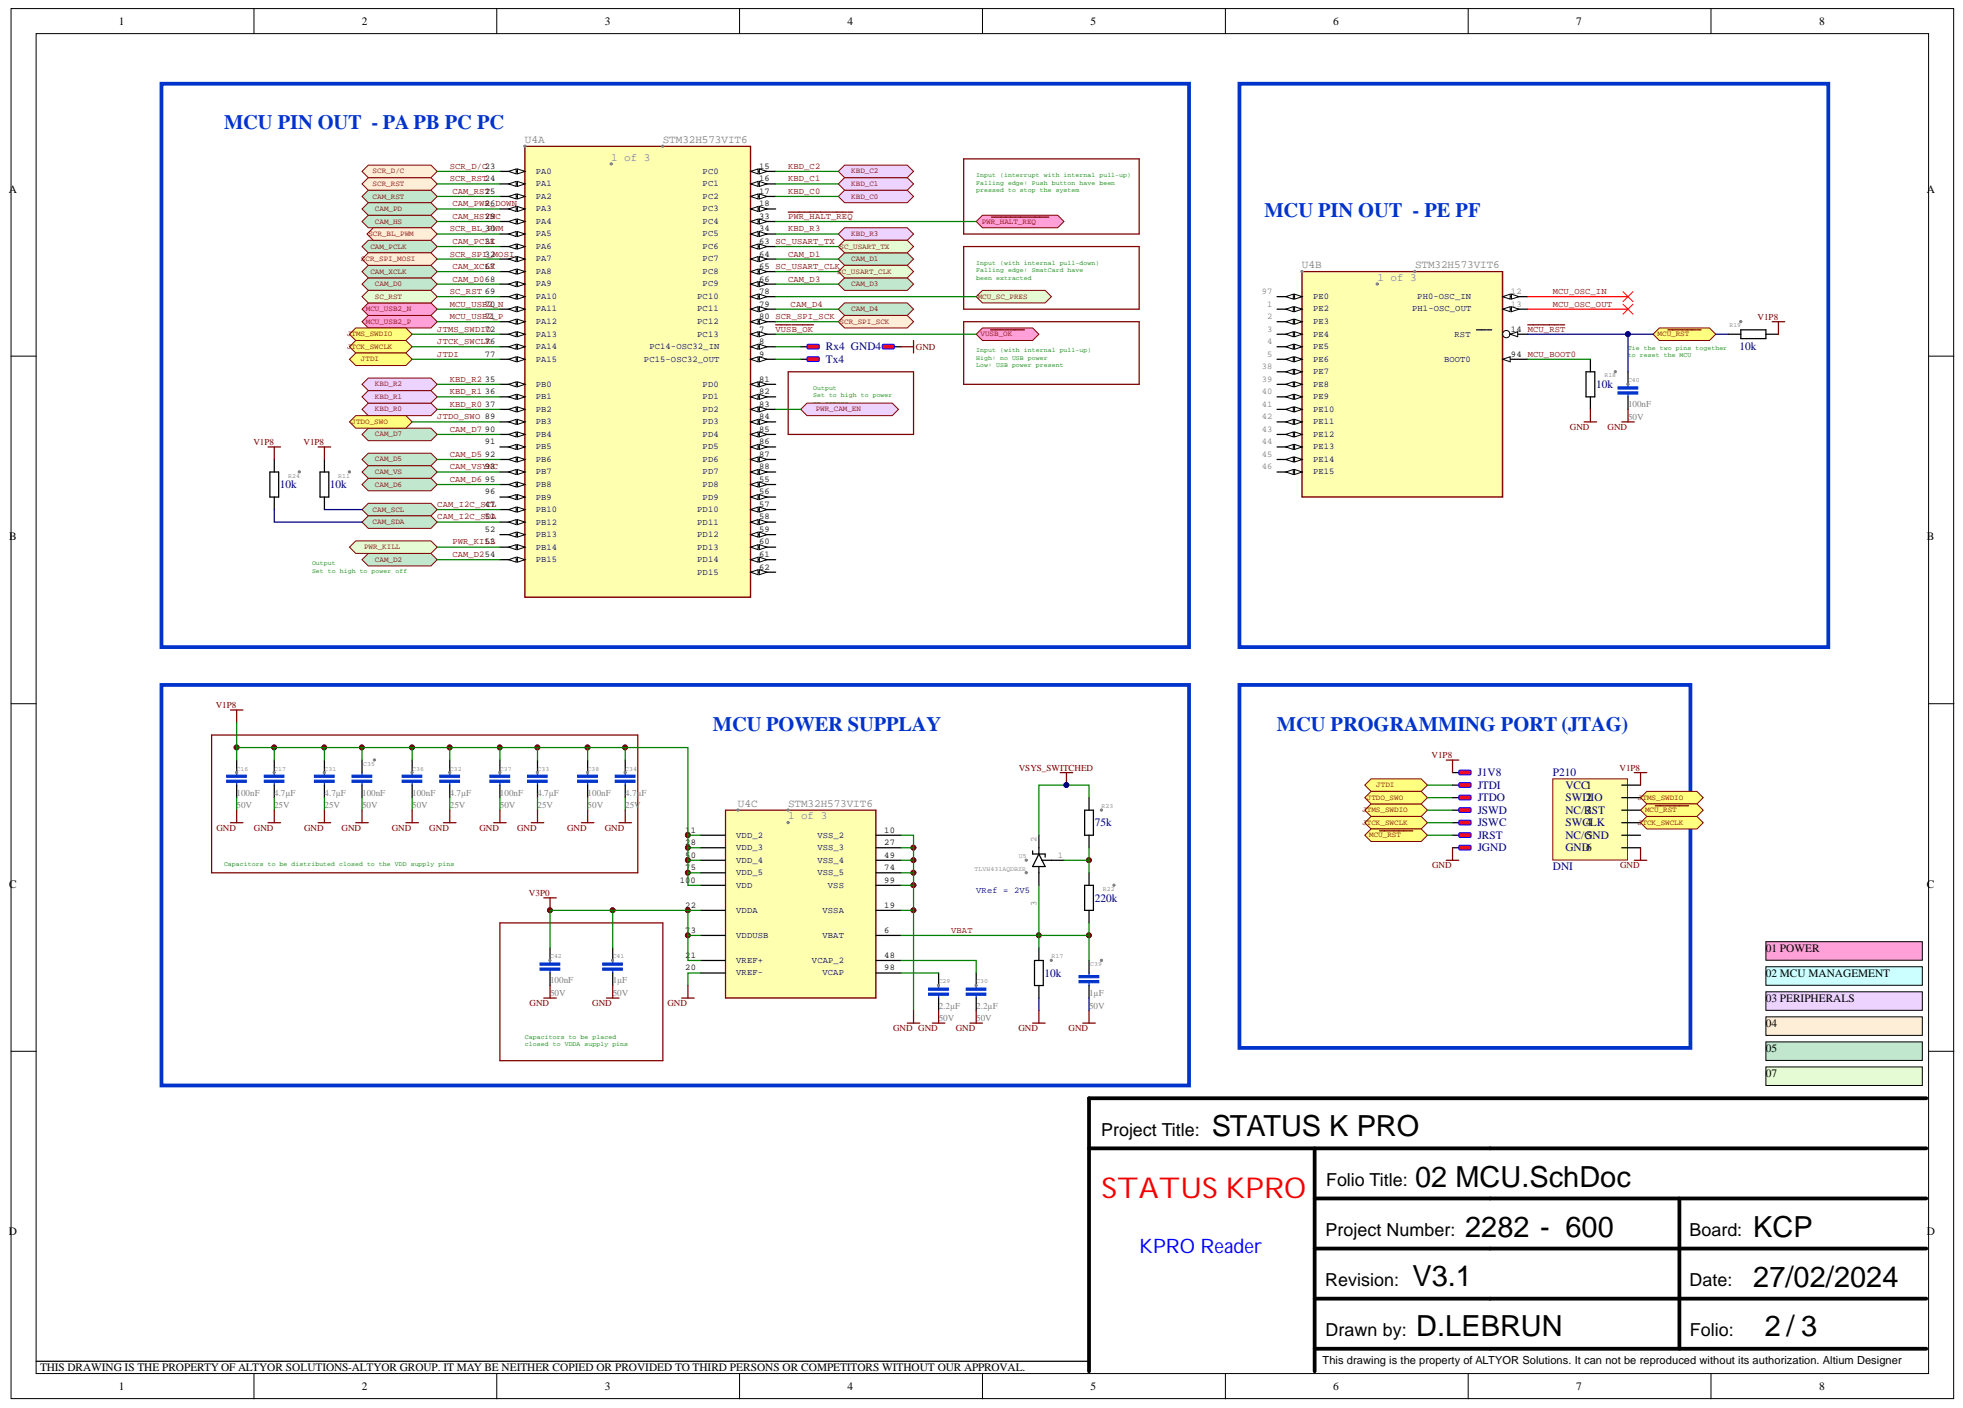
[picture p52: page 3]

MCU PIN OUT - PA PB PC PC

Input (interrupt with internal pull-up)
Falling edge: Push button have been
pressed to stop the system

MCU PIN OUT - PE PF

Input (with internal pull-down)
Falling edge: SmatCard have
been extracted

Input (with internal pull-up)
High: no USB power
Low: USB power present

Tie the two pins together
to reset the MCU

Output
Set to high to power
on camera
PWR_CAM_EN

Set to high to power off

Capacitors to be distributed closed to the VDD supply pins

Capacitors to be placed
closed to VDDA supply pins

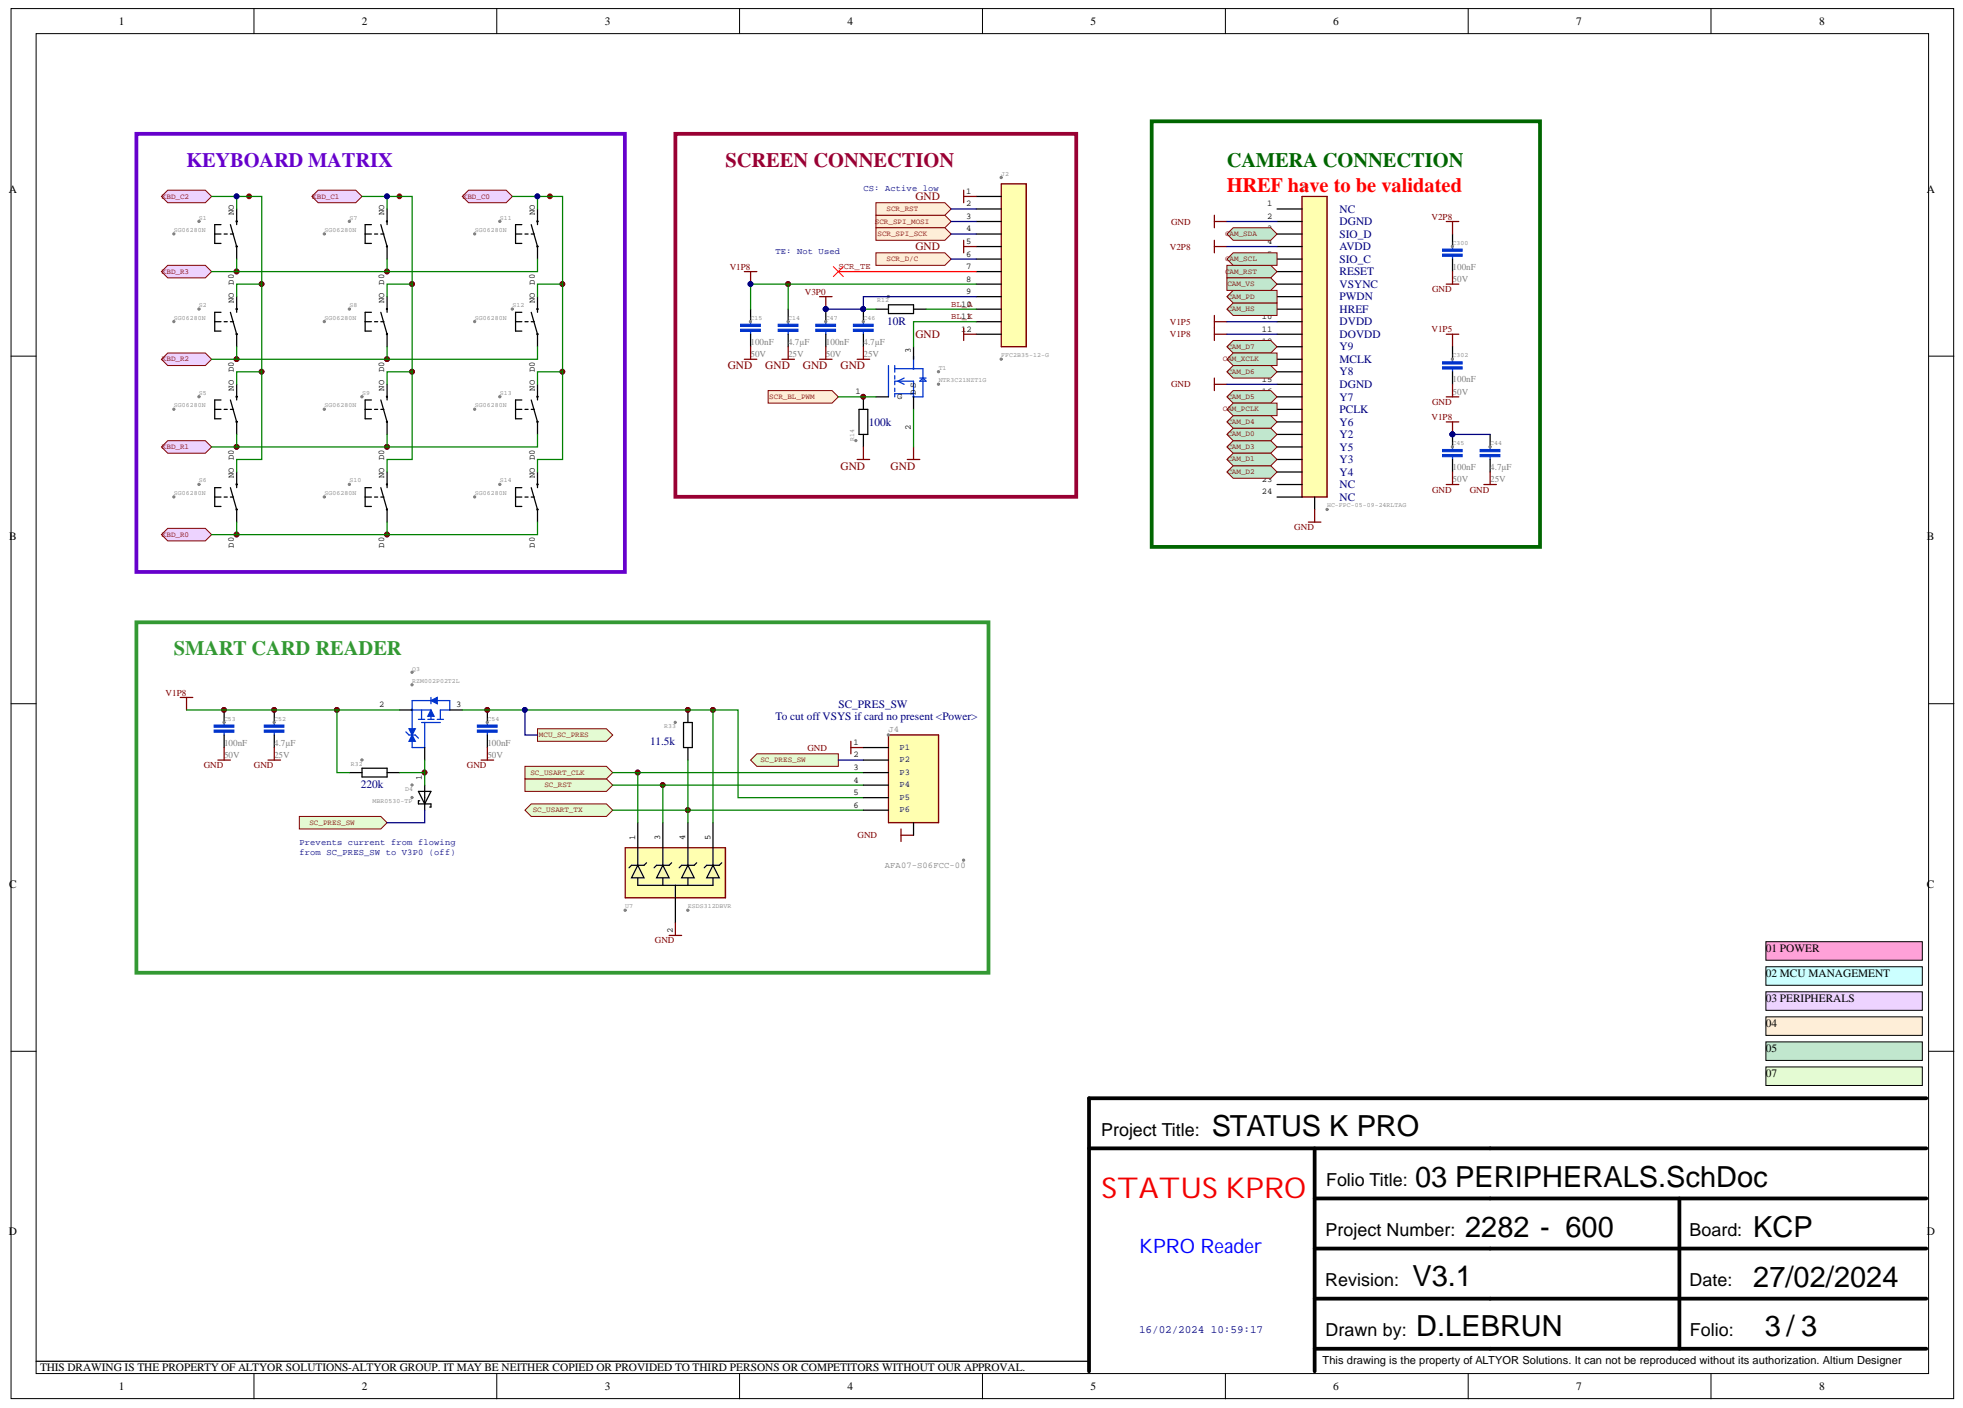
[picture p53: page 4]

HREF have to be validated

To cut off VSYS if card no present <Power>

Prevents current from flowing
from SC_PRES_SW to V3P0 (off)
