keycard-tech/keycard-shell/hardware/shell/pilot_run/mechanical/parts/2282-001-TOP-V05-20250415.PDF

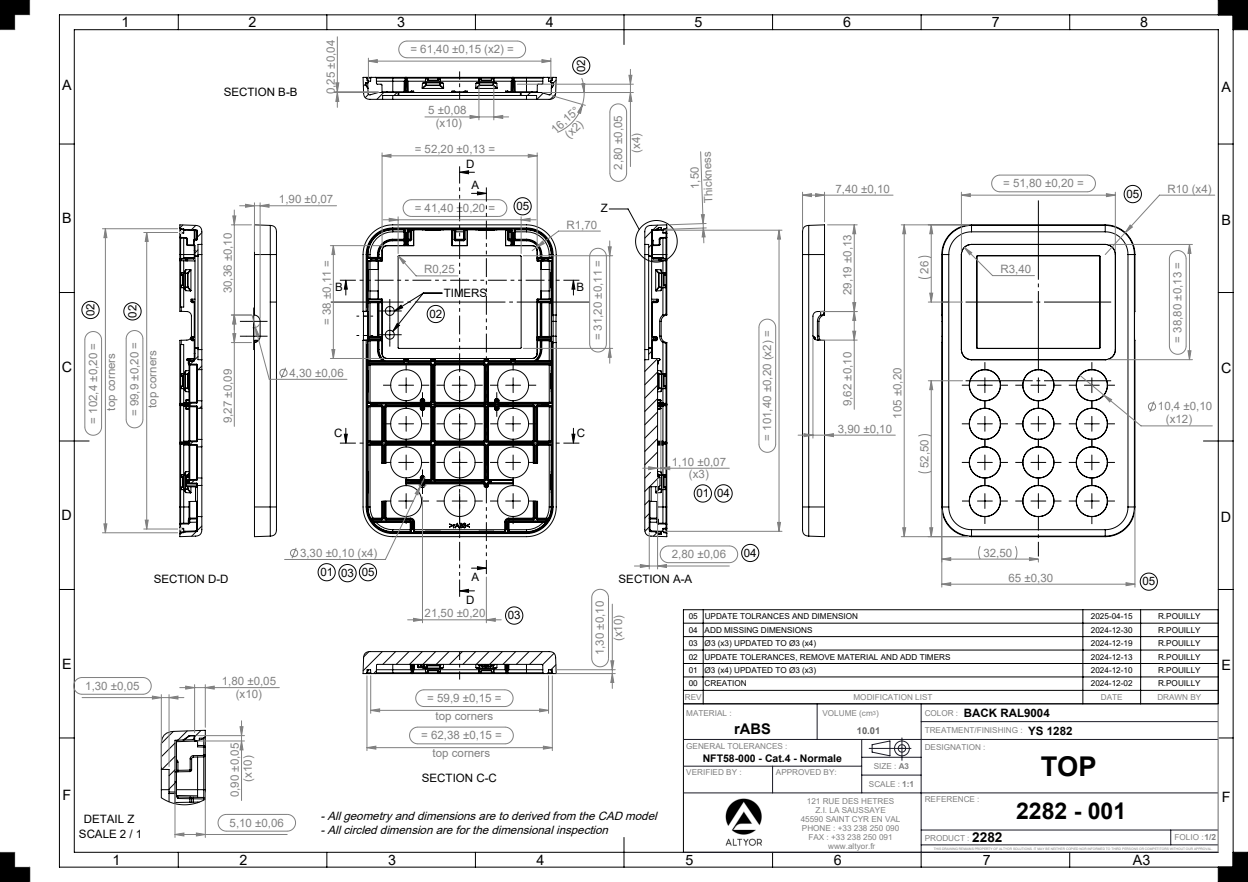
[picture p54: page 1]
SECTION B-B; SECTION A-A; DETAIL Z; SCALE 2 / 1 = 102,4 ±0,20 =; top corners; SECTION D-D; = 62,38 ±0,15 = top corners; = 59,9 ±0,15 = top corners; SECTION C-C; rABS; BACK RAL9004; TREATMENT/FINISHING :; VOLUME (cm3); COLOR :; MATERIAL :; SIZE : A3; SCALE :

05 | UPDATE TOLRANCES AND DIMENSION | 2025-04-15 | R.POUILLY
04 | ADD MISSING DIMENSIONS | 2024-12-30 | R.POUILLY
03 | Ø3 (x3) UPDATED TO Ø3 (x4) | 2024-12-19 | R.POUILLY
02 | UPDATE TOLERANCES, REMOVE MATERIAL AND ADD TIMERS | 2024-12-13 | R.POUILLY
01 | Ø3 (x4) UPDATED TO Ø3 (x3) | 2024-12-10 | R.POUILLY
00 | CREATION | 2024-12-02 | R.POUILLY
REV | MODIFICATION LIST | DATE | DRAWN BY

GENERAL TOLERANCES : NFT58-000 - Cat.4 - Normale | | DESIGNATION : TOP

VERIFIED BY : | APPROVED BY:

121 RUE DES HETRES Z.I. LA SAUSSAYE 45590 SAINT CYR EN VAL PHONE : +33 238 250 090 FAX : +33 238 250 091 www.altyor.fr | REFERENCE : 2282 - 001

- All geometry and dimensions are to derived from the CAD model
- All circled dimension are for the dimensional inspection

2282 PRODUCT : | FOLIO : 1/2

THIS DRAWING REMAINS PROPERTY OF ALTYOR SOLUTIONS. IT MAY BE NEITHER COPIED NOR INFORMED TO THIRD PERSONS OR COMPETITORS WITHOUT OUR APPROVAL.

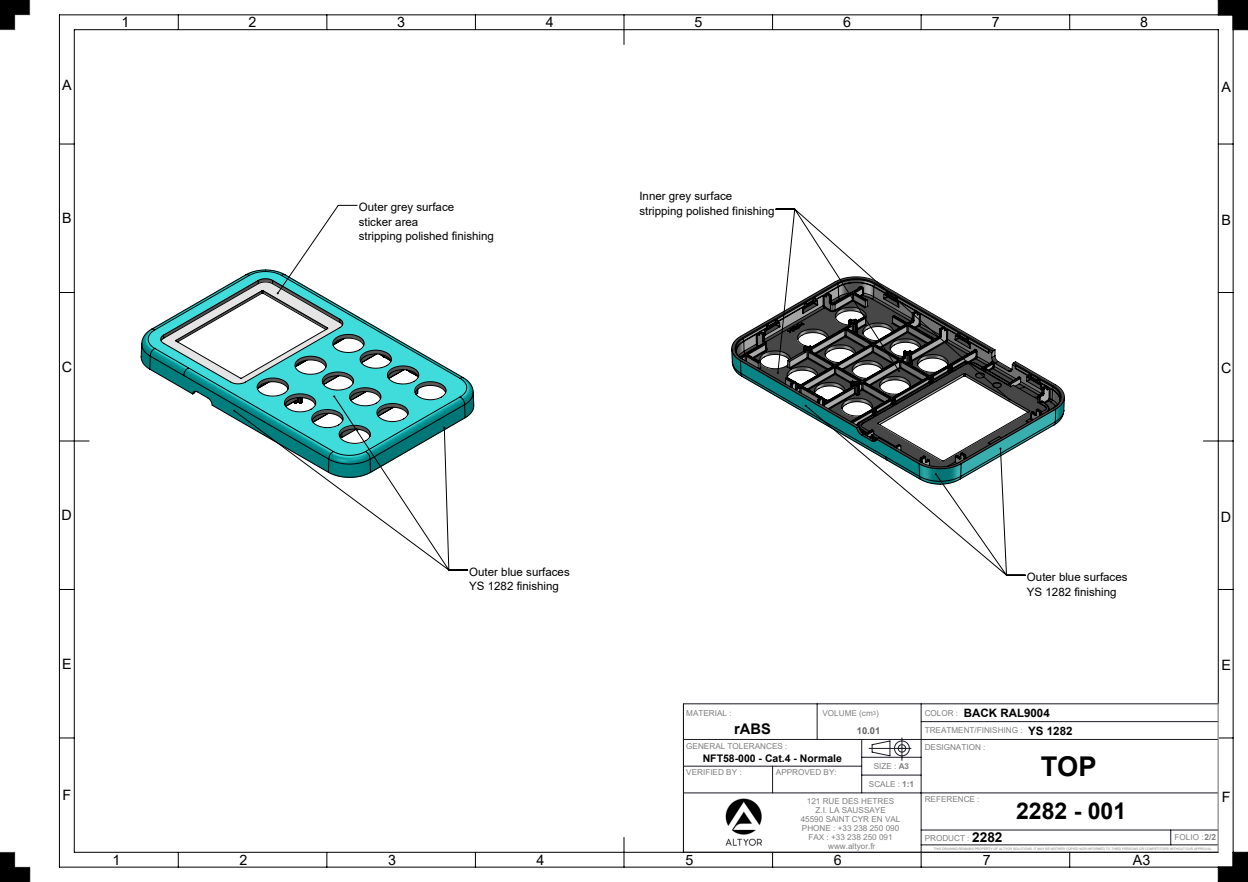
[picture p55: page 2]
rABS; BACK RAL9004; TREATMENT/FINISHING :; VOLUME (cm3); COLOR :; MATERIAL :; SIZE : A3; SCALE :

Inner grey surface
stripping polished finishing

Outer grey surface
sticker area

Outer blue surfaces
YS 1282 finishing

GENERAL TOLERANCES : NFT58-000 - Cat.4 - Normale | | | DESIGNATION : TOP

VERIFIED BY : | APPROVED BY:

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

2282 PRODUCT : | FOLIO : 2/2

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
