keycard-tech/keycard-shell/hardware/shell/pilot_run/mechanical/parts/2282-002-MIDDLEFRAME-V05-20250514.PDF

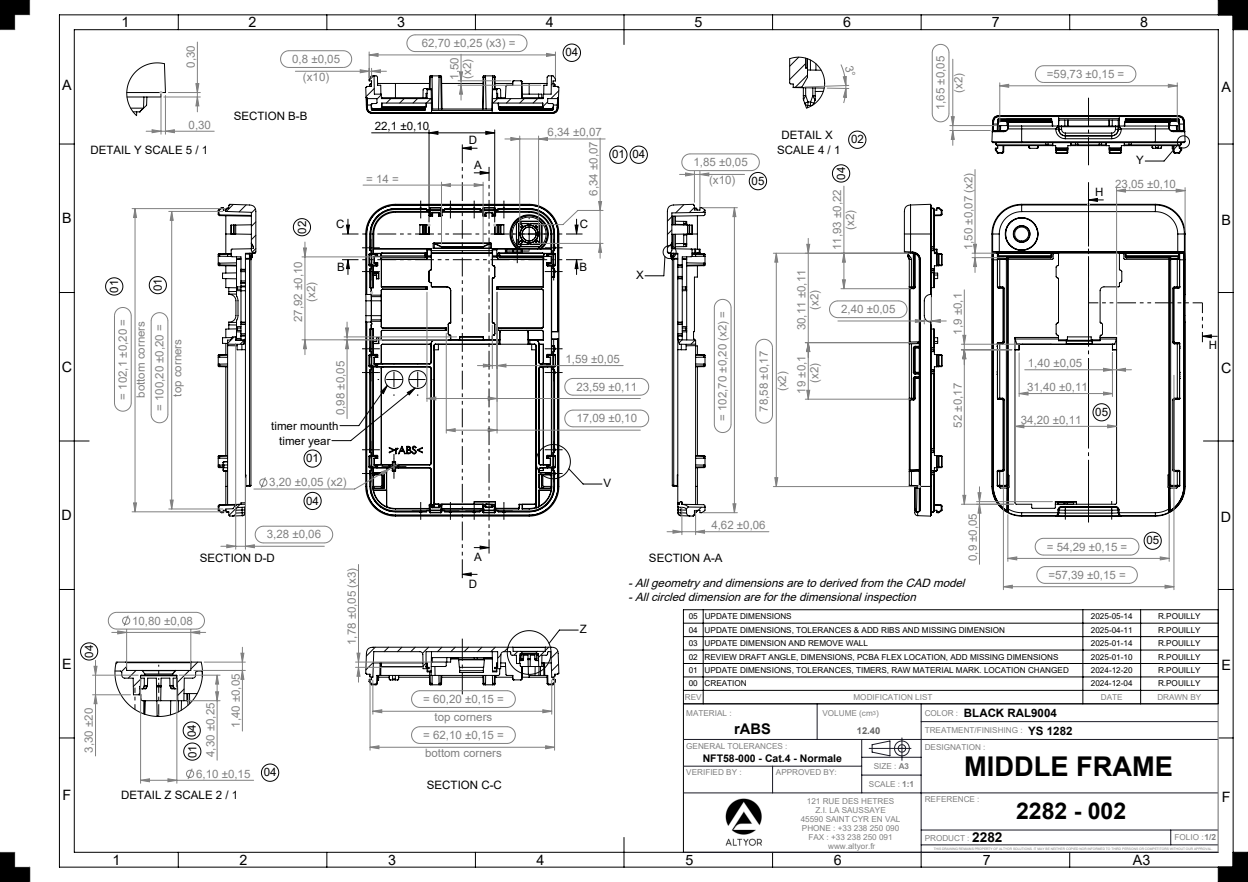
[picture p56: page 1]
timer year; timer mounth; SECTION B-B; = 60,20 ±0,15 = top corners; = 62,10 ±0,15 = bottom corners; SECTION C-C; bottom corners; top corners; 3,28 ±0,06 SECTION D-D 1,40 ±0,05; 4,30 ±0,25 DETAIL Z SCALE 2 / 1 01 04; DETAIL Y SCALE 5 / 1; DETAIL X SCALE 4 / 1; rABS; BLACK RAL9004; TREATMENT/FINISHING :; VOLUME (cm3); COLOR :; MATERIAL :; SIZE : A3; SCALE :

SECTION A-A
- All geometry and dimensions are to derived from the CAD model
- All circled dimension are for the dimensional inspection

05 | UPDATE DIMENSIONS | 2025-05-14 | R.POUILLY
04 | UPDATE DIMENSIONS, TOLERANCES & ADD RIBS AND MISSING DIMENSION | 2025-04-11 | R.POUILLY
03 | UPDATE DIMENSION AND REMOVE WALL | 2025-01-14 | R.POUILLY
02 | REVIEW DRAFT ANGLE, DIMENSIONS, PCBA FLEX LOCATION, ADD MISSING DIMENSIONS | 2025-01-10 | R.POUILLY
01 | UPDATE DIMENSIONS, TOLERANCES, TIMERS, RAW MATERIAL MARK. LOCATION CHANGED | 2024-12-20 | R.POUILLY
00 | CREATION | 2024-12-04 | R.POUILLY
REV | MODIFICATION LIST | DATE | DRAWN BY

GENERAL TOLERANCES : NFT58-000 - Cat.4 - Normale | | DESIGNATION : MIDDLE FRAME

VERIFIED BY : | APPROVED BY:

121 RUE DES HETRES Z.I. LA SAUSSAYE 45590 SAINT CYR EN VAL PHONE : +33 238 250 090 FAX : +33 238 250 091 www.altyor.fr | REFERENCE : 2282 - 002

2282 PRODUCT : | FOLIO : 1/2

THIS DRAWING REMAINS PROPERTY OF ALTYOR SOLUTIONS. IT MAY BE NEITHER COPIED NOR INFORMED TO THIRD PERSONS OR COMPETITORS WITHOUT OUR APPROVAL.

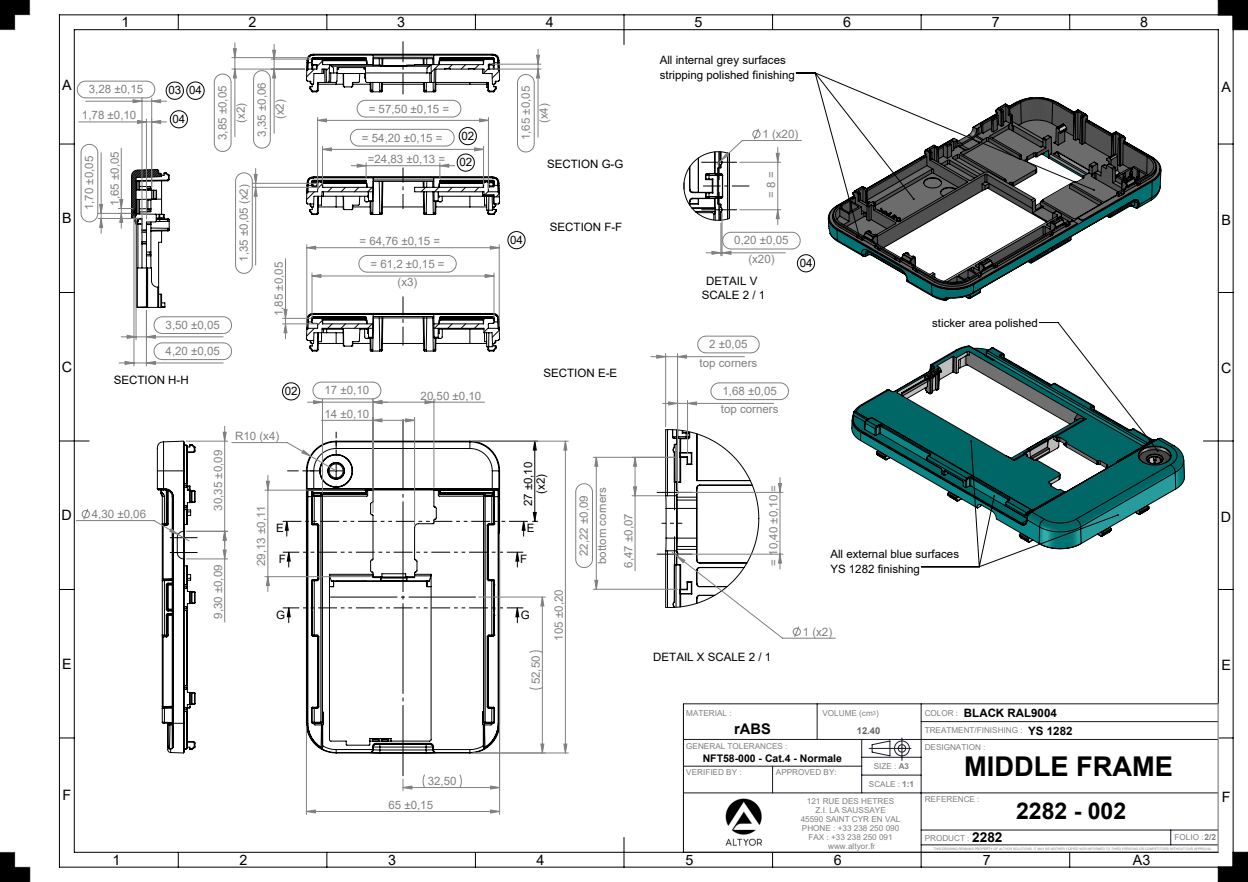
[picture p57: page 2]
SECTION E-E; SECTION F-F; SECTION G-G; bottom corners; 1,68 ±0,05 top corners; 2 ±0,05 top corners; DETAIL X SCALE 2 / 1; SECTION H-H; DETAIL V SCALE 2 / 1; rABS; BLACK RAL9004; TREATMENT/FINISHING :; VOLUME (cm3); COLOR :; MATERIAL :; SIZE : A3; SCALE :

All internal grey surfaces
stripping polished finishing

sticker area polished

All external blue surfaces
YS 1282 finishing

GENERAL TOLERANCES : NFT58-000 - Cat.4 - Normale | | DESIGNATION : MIDDLE FRAME

VERIFIED BY : | APPROVED BY:

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

2282 PRODUCT : | FOLIO : 2/2

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
