keycard-tech/keycard-shell/hardware/shell/pilot_run/mechanical/parts/2282-003-SIDEBUTTON-V04-20250514.pdf

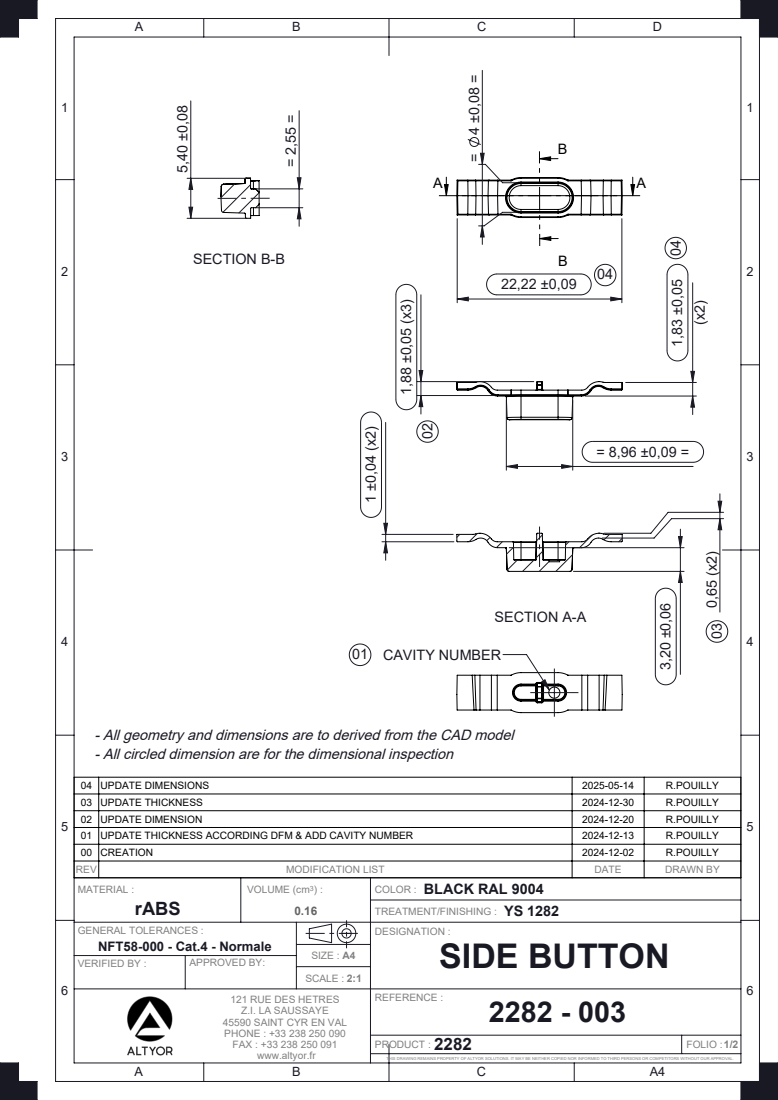
[picture p58: page 1]
SECTION A-A; SECTION B-B; CAVITY NUMBER; SCALE :; SIZE : A4; MATERIAL :; VOLUME (cm3) :; COLOR :; TREATMENT/FINISHING :; BLACK RAL 9004; rABS

- All geometry and dimensions are to derived from the CAD model
- All circled dimension are for the dimensional inspection

04 | UPDATE DIMENSIONS | 2025-05-14 | R.POUILLY
03 | UPDATE THICKNESS | 2024-12-30 | R.POUILLY
02 | UPDATE DIMENSION | 2024-12-20 | R.POUILLY
01 | UPDATE THICKNESS ACCORDING DFM & ADD CAVITY NUMBER | 2024-12-13 | R.POUILLY
00 | CREATION | 2024-12-02 | R.POUILLY
REV | MODIFICATION LIST | DATE | DRAWN BY

GENERAL TOLERANCES : NFT58-000 - Cat.4 - Normale | | DESIGNATION : SIDE BUTTON

VERIFIED BY : | APPROVED BY:

121 RUE DES HETRES Z.I. LA SAUSSAYE 45590 SAINT CYR EN VAL PHONE : +33 238 250 090 FAX : +33 238 250 091 www.altyor.fr | REFERENCE : 2282 - 003

PRODUCT : | FOLIO : 1/2

THIS DRAWING REMAINS PROPERTY OF ALTYOR SOLUTIONS. IT MAY BE NEITHER COPIED NOR INFORMED TO THIRD PERSONS OR COMPETITORS WITHOUT OUR APPROVAL.

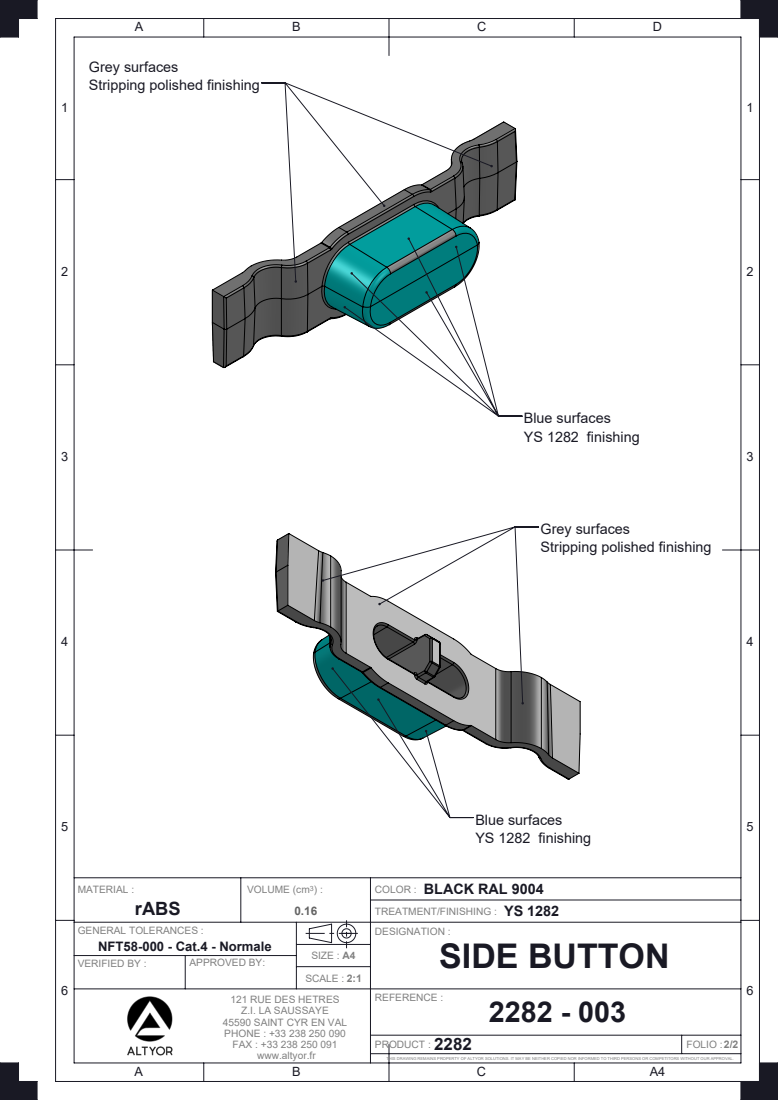
[picture p59: page 2]
Blue surfaces YS 1282 finishing; SCALE :; SIZE : A4; MATERIAL :; VOLUME (cm3) :; COLOR :; TREATMENT/FINISHING :; BLACK RAL 9004; rABS

Grey surfaces
Stripping polished finishing

GENERAL TOLERANCES : NFT58-000 - Cat.4 - Normale | | | DESIGNATION : SIDE BUTTON

VERIFIED BY : | APPROVED BY:

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

PRODUCT : | FOLIO : 2/2

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
