keycard-tech/keycard-shell/hardware/shell/pilot_run/mechanical/parts/2282-004-BOTTOMCOVER-V03-20250428.PDF

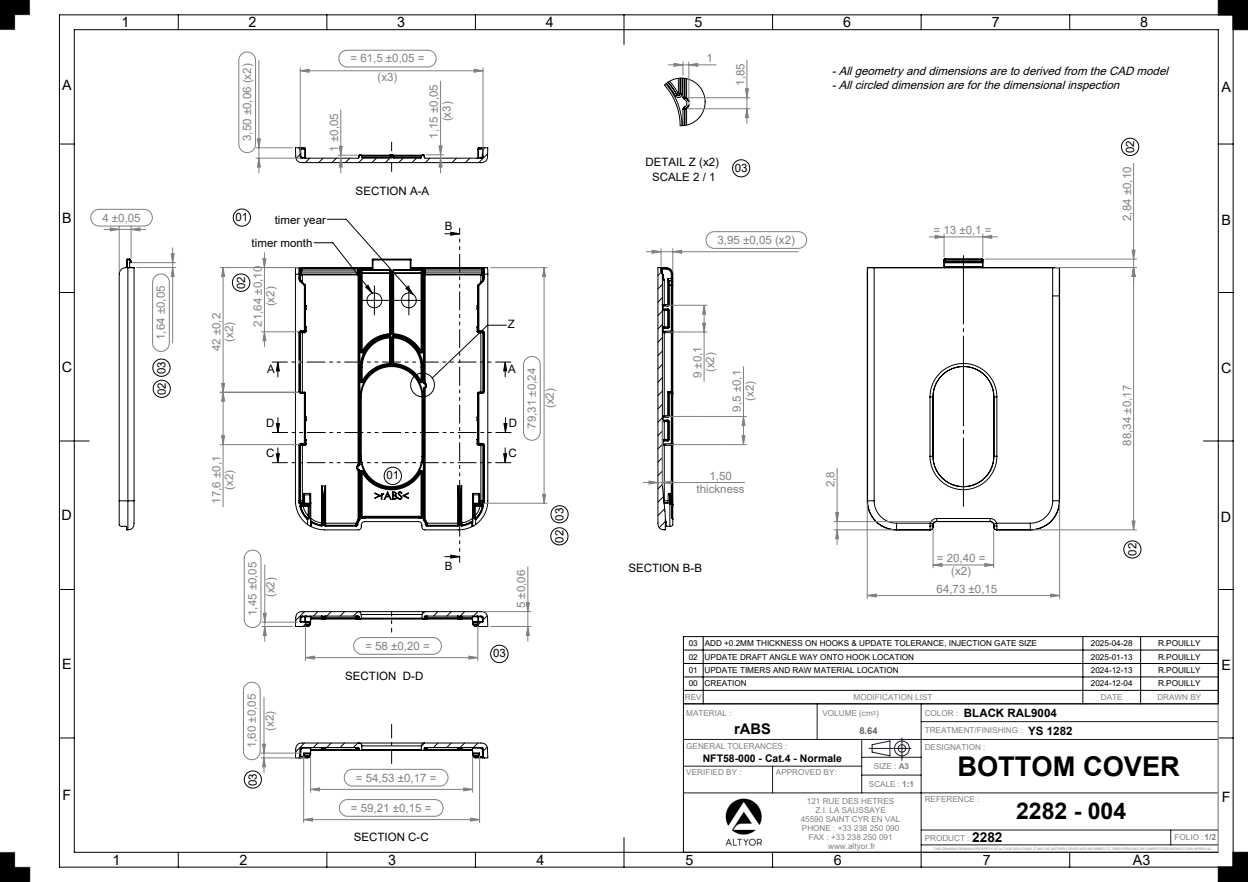
[picture p60: page 1]
timer month; timer year; SECTION A-A; thickness 9 ±0,1 (x2); SECTION B-B; SECTION C-C; SECTION D-D; DETAIL Z (x2) SCALE 2 / 1; rABS; BLACK RAL9004; TREATMENT/FINISHING :; VOLUME (cm3); COLOR :; MATERIAL :; SIZE : A3; SCALE :

- All geometry and dimensions are to derived from the CAD model
- All circled dimension are for the dimensional inspection

03 | ADD +0.2MM THICKNESS ON HOOKS & UPDATE TOLERANCE, INJECTION GATE SIZE | 2025-04-28 | R.POUILLY
02 | UPDATE DRAFT ANGLE WAY ONTO HOOK LOCATION | 2025-01-13 | R.POUILLY
01 | UPDATE TIMERS AND RAW MATERIAL LOCATION | 2024-12-13 | R.POUILLY
00 | CREATION | 2024-12-04 | R.POUILLY
REV | MODIFICATION LIST | DATE | DRAWN BY

GENERAL TOLERANCES : NFT58-000 - Cat.4 - Normale | | DESIGNATION : BOTTOM COVER

VERIFIED BY : | APPROVED BY:

121 RUE DES HETRES Z.I. LA SAUSSAYE 45590 SAINT CYR EN VAL PHONE : +33 238 250 090 FAX : +33 238 250 091 www.altyor.fr | REFERENCE : 2282 - 004

2282 PRODUCT : | FOLIO : 1/2

THIS DRAWING REMAINS PROPERTY OF ALTYOR SOLUTIONS. IT MAY BE NEITHER COPIED NOR INFORMED TO THIRD PERSONS OR COMPETITORS WITHOUT OUR APPROVAL.

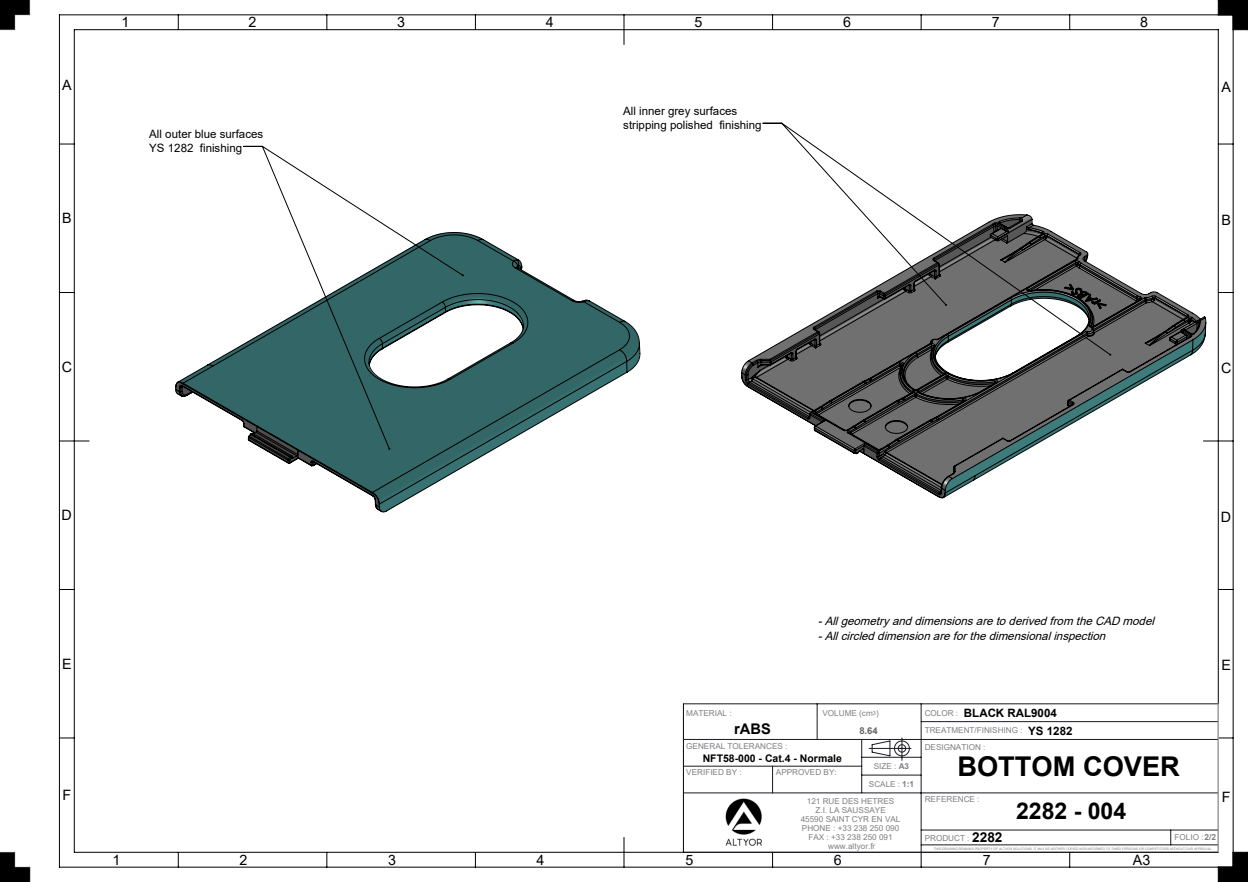
[picture p61: page 2]
rABS; BLACK RAL9004; TREATMENT/FINISHING :; VOLUME (cm3); COLOR :; MATERIAL :; SIZE : A3; SCALE :

All inner grey surfaces

stripping polished finishing All outer blue surfaces
YS 1282 finishing

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

GENERAL TOLERANCES : NFT58-000 - Cat.4 - Normale | | | DESIGNATION : BOTTOM COVER

VERIFIED BY : | APPROVED BY:

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

2282 PRODUCT : | FOLIO : 2/2

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
