keycard-tech/keycard-shell/hardware/shell/prototype_P2/mechanical/parts/2282-001-TOP-V03-20241219.PDF

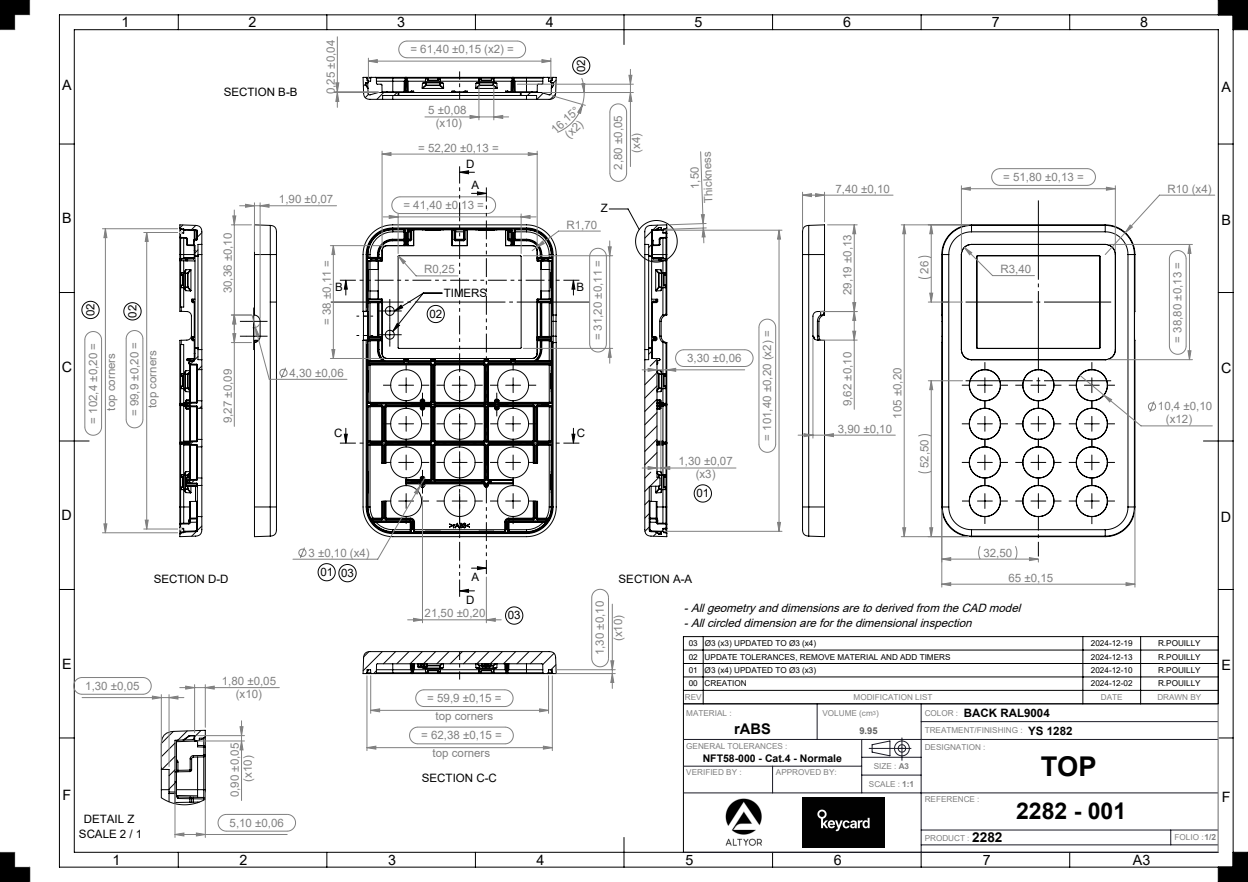
[picture p66: page 1]
SECTION B-B; 3,30 ±0,06 1,50 Thickness; SECTION A-A; DETAIL Z; SCALE 2 / 1 = 102,4 ±0,20 =; top corners; SECTION D-D; = 62,38 ±0,15 = top corners; = 59,9 ±0,15 = top corners; SECTION C-C; - All geometry and dimensions are to derived from the CAD model; NFT58-000 - Cat.4 - Normale; rABS; BACK RAL9004; VERIFIED BY :; APPROVED BY:; TOP; DESIGNATION :; TREATMENT/FINISHING :; VOLUME (cm3); COLOR :; GENERAL TOLERANCES :; MATERIAL :; SIZE : A3; SCALE :

- All circled dimension are for the dimensional inspection

03 | Ø3 (x3) UPDATED TO Ø3 (x4) | 2024-12-19 | R.POUILLY
02 | UPDATE TOLERANCES, REMOVE MATERIAL AND ADD TIMERS | 2024-12-13 | R.POUILLY
01 | Ø3 (x4) UPDATED TO Ø3 (x3) | 2024-12-10 | R.POUILLY
00 | CREATION | 2024-12-02 | R.POUILLY
REV | MODIFICATION LIST | DATE | DRAWN BY

REFERENCE : 2282 - 001

2282 PRODUCT : | FOLIO : 1/2

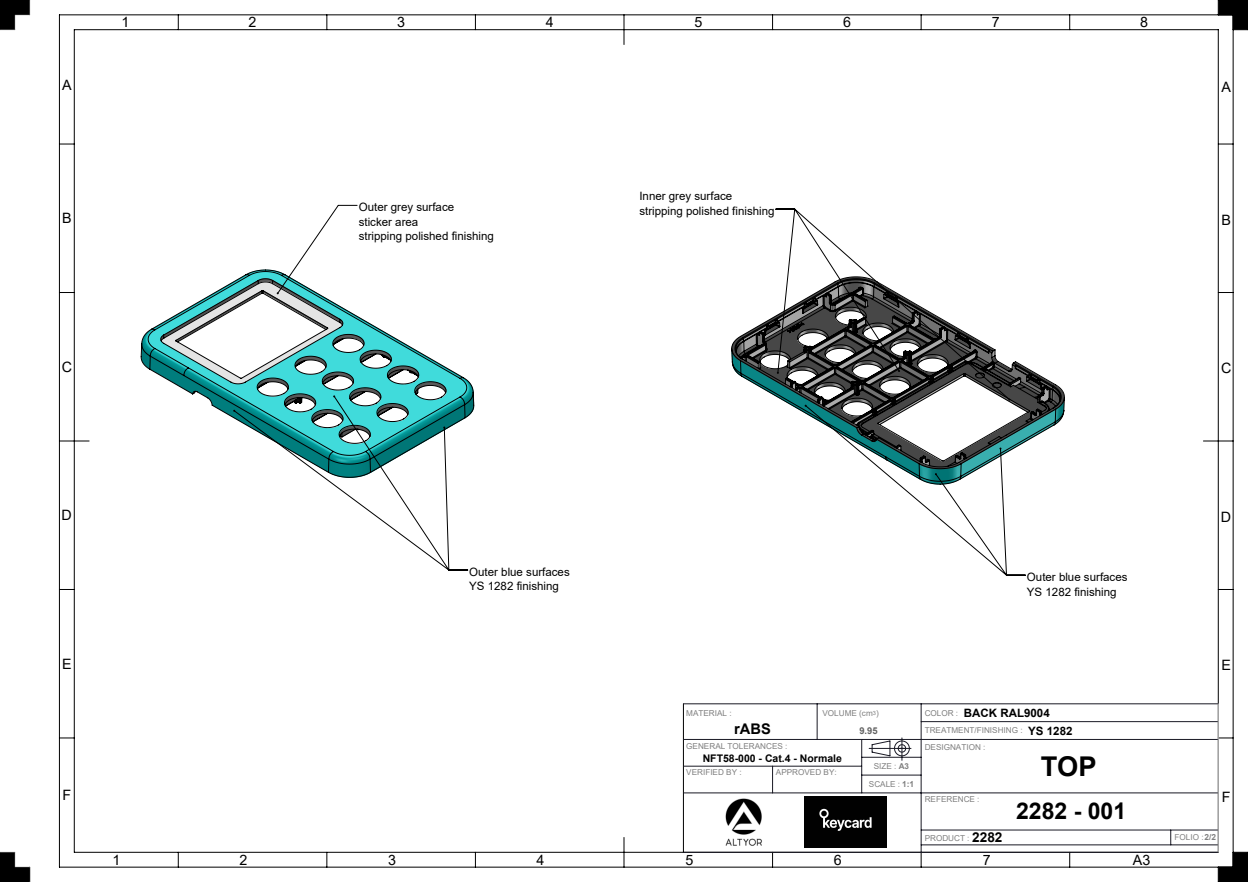
[picture p67: page 2]
rABS; BACK RAL9004; VERIFIED BY :; APPROVED BY:; TOP; TREATMENT/FINISHING :; VOLUME (cm3); COLOR :; MATERIAL :; SIZE : A3; SCALE :

Inner grey surface
stripping polished finishing

Outer grey surface
sticker area

Outer blue surfaces
YS 1282 finishing

GENERAL TOLERANCES : NFT58-000 - Cat.4 - Normale | | DESIGNATION :

REFERENCE : 2282 - 001

2282 PRODUCT : | FOLIO : 2/2
