keycard-tech/keycard-shell/hardware/shell/prototype_P2/mechanical/parts/2282-002-MIDDLEFRAME-V01-20241220.PDF

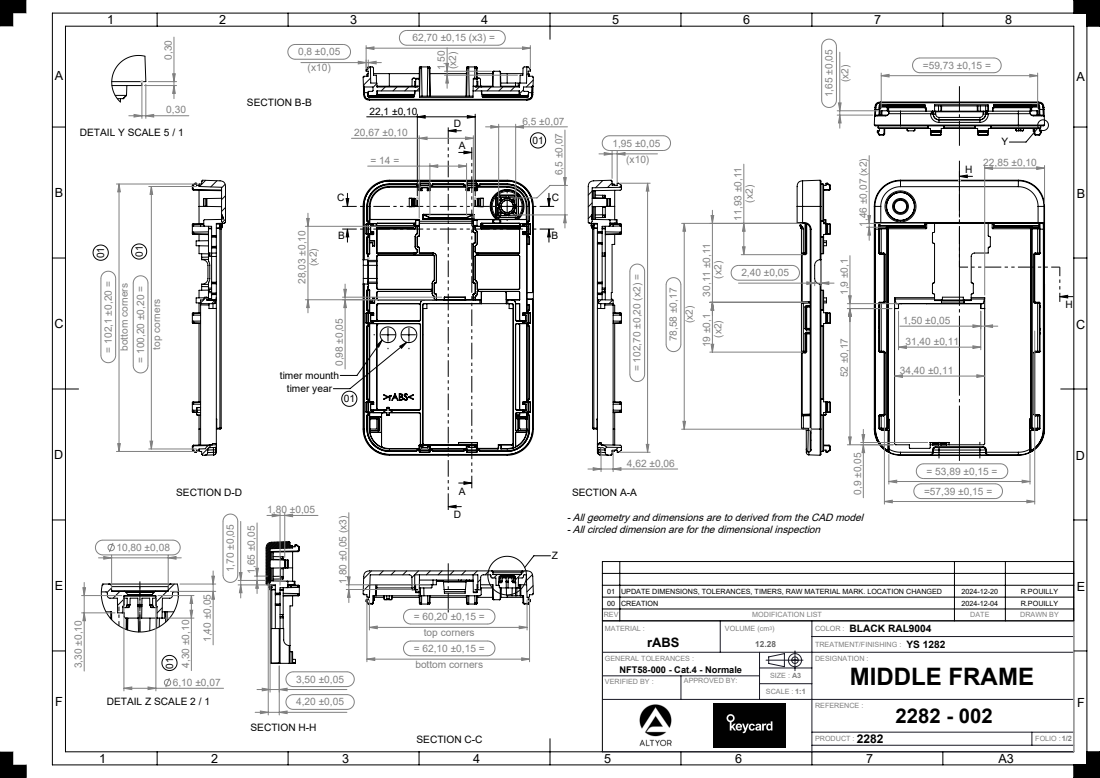
[picture p68: page 1]
timer year; timer mounth; SECTION B-B; = 60,20 ±0,15 = top corners; = 62,10 ±0,15 = bottom corners; SECTION C-C; bottom corners; top corners; SECTION D-D 1,40 ±0,05; DETAIL Z SCALE 2 / 1 01; DETAIL Y SCALE 5 / 1; SECTION H-H; NFT58-000 - Cat.4 - Normale; rABS; BLACK RAL9004; VERIFIED BY :; APPROVED BY:; MIDDLE FRAME; DESIGNATION :; TREATMENT/FINISHING :; VOLUME (cm3); COLOR :; GENERAL TOLERANCES :; MATERIAL :; SIZE : A3; SCALE :

SECTION A-A
- All geometry and dimensions are to derived from the CAD model
- All circled dimension are for the dimensional inspection

01 | UPDATE DIMENSIONS, TOLERANCES, TIMERS, RAW MATERIAL MARK. LOCATION CHANGED | 2024-12-20 | R.POUILLY
00 | CREATION | 2024-12-04 | R.POUILLY
REV | MODIFICATION LIST | DATE | DRAWN BY

REFERENCE : 2282 - 002

2282 PRODUCT : | FOLIO : 1/2

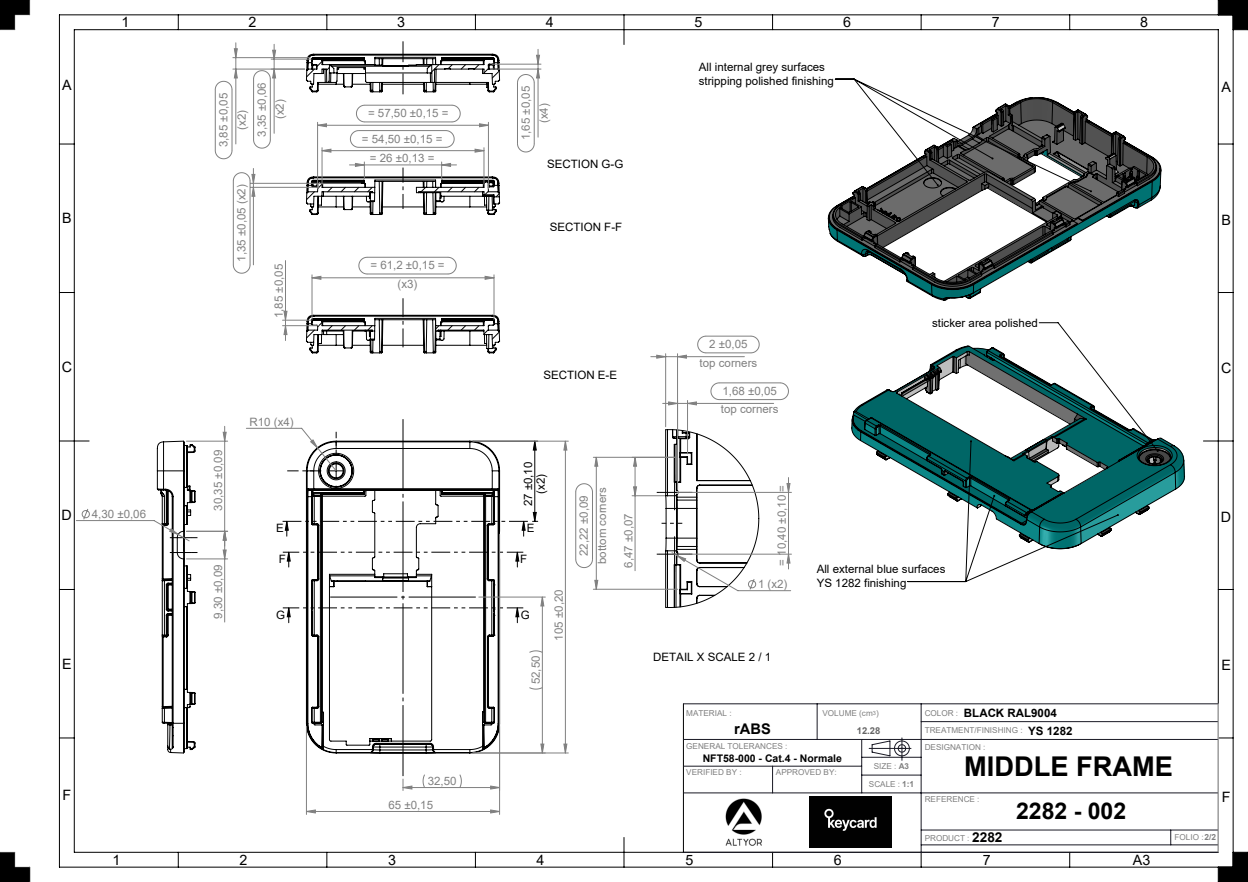
[picture p69: page 2]
SECTION E-E; SECTION F-F; SECTION G-G; bottom corners; 1,68 ±0,05 top corners; 2 ±0,05 top corners; DETAIL X SCALE 2 / 1; NFT58-000 - Cat.4 - Normale; rABS; BLACK RAL9004; VERIFIED BY :; APPROVED BY:; MIDDLE FRAME; DESIGNATION :; TREATMENT/FINISHING :; VOLUME (cm3); COLOR :; GENERAL TOLERANCES :; MATERIAL :; SIZE : A3; SCALE :

All internal grey surfaces
stripping polished finishing

sticker area polished

All external blue surfaces
YS 1282 finishing

REFERENCE : 2282 - 002

2282 PRODUCT : | FOLIO : 2/2
