keycard-tech/keycard-shell/hardware/shell/prototype_P2/mechanical/parts/2282-003-SIDEBUTTON-V02-20241220.PDF

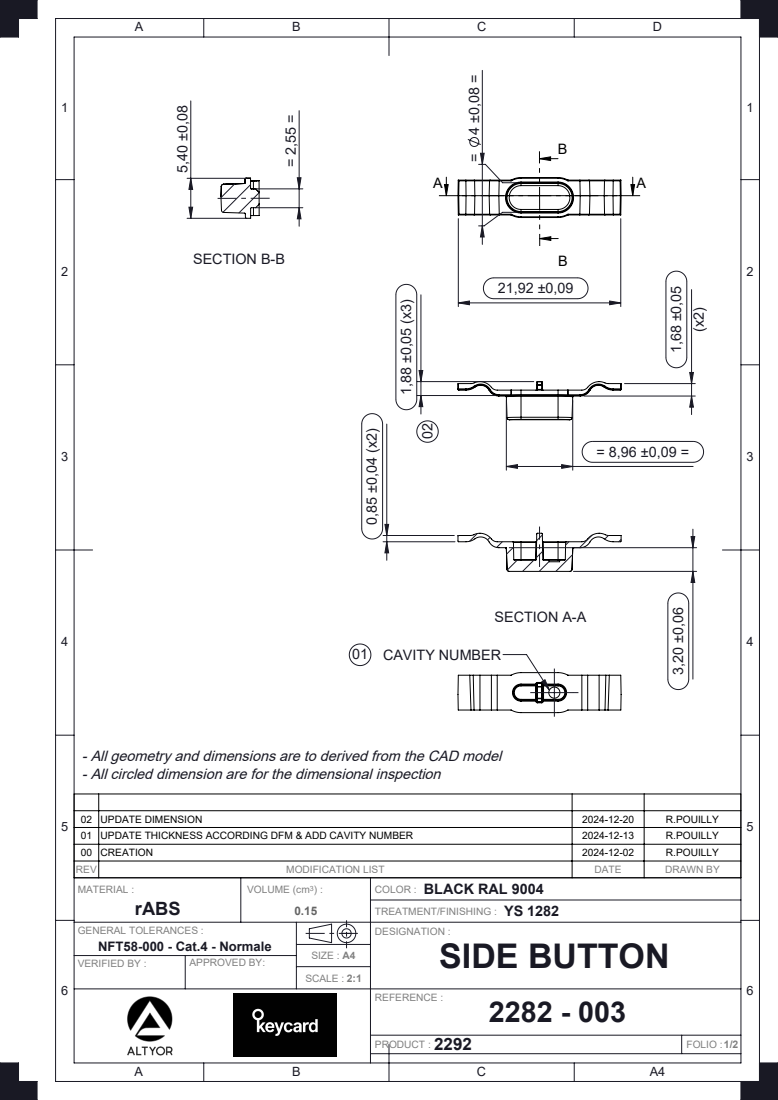
[picture p70: page 1]
SECTION A-A; SECTION B-B; CAVITY NUMBER; SCALE :; SIZE : A4; MATERIAL :; GENERAL TOLERANCES :; VOLUME (cm3) :; COLOR :; TREATMENT/FINISHING : DESIGNATION :; VERIFIED BY :; APPROVED BY:; SIDE BUTTON; BLACK RAL 9004; rABS; NFT58-000 - Cat.4 - Normale

- All geometry and dimensions are to derived from the CAD model
- All circled dimension are for the dimensional inspection

02 | UPDATE DIMENSION | 2024-12-20 | R.POUILLY
01 | UPDATE THICKNESS ACCORDING DFM & ADD CAVITY NUMBER | 2024-12-13 | R.POUILLY
00 | CREATION | 2024-12-02 | R.POUILLY
REV | MODIFICATION LIST | DATE | DRAWN BY

REFERENCE : 2282 - 003

PRODUCT : | FOLIO : 1/2

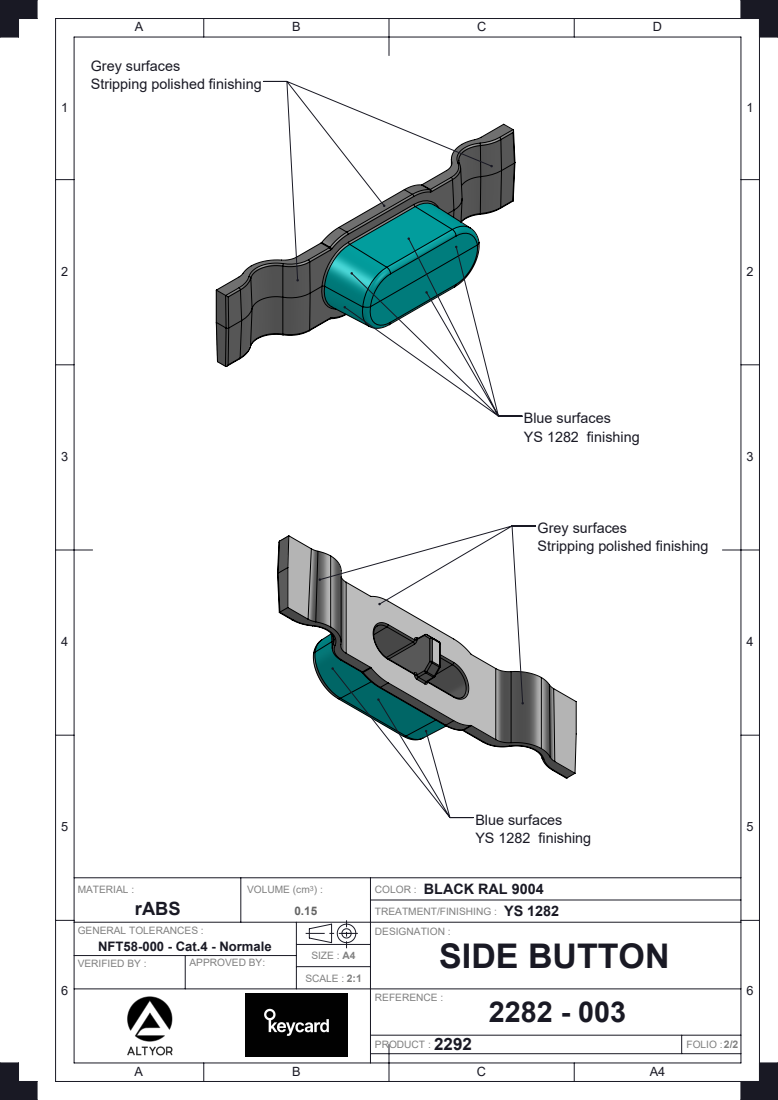
[picture p71: page 2]
Blue surfaces YS 1282 finishing; SCALE :; SIZE : A4; MATERIAL :; VOLUME (cm3) :; COLOR :; TREATMENT/FINISHING :; VERIFIED BY :; APPROVED BY:; SIDE BUTTON; BLACK RAL 9004; rABS

Grey surfaces
Stripping polished finishing

GENERAL TOLERANCES : NFT58-000 - Cat.4 - Normale | | DESIGNATION :

REFERENCE : 2282 - 003

PRODUCT : | FOLIO : 2/2
