keycard-tech/keycard-shell/hardware/shell/prototype_P2/mechanical/parts/2282-004-BOTTOMCOVER-V01-20241213.PDF

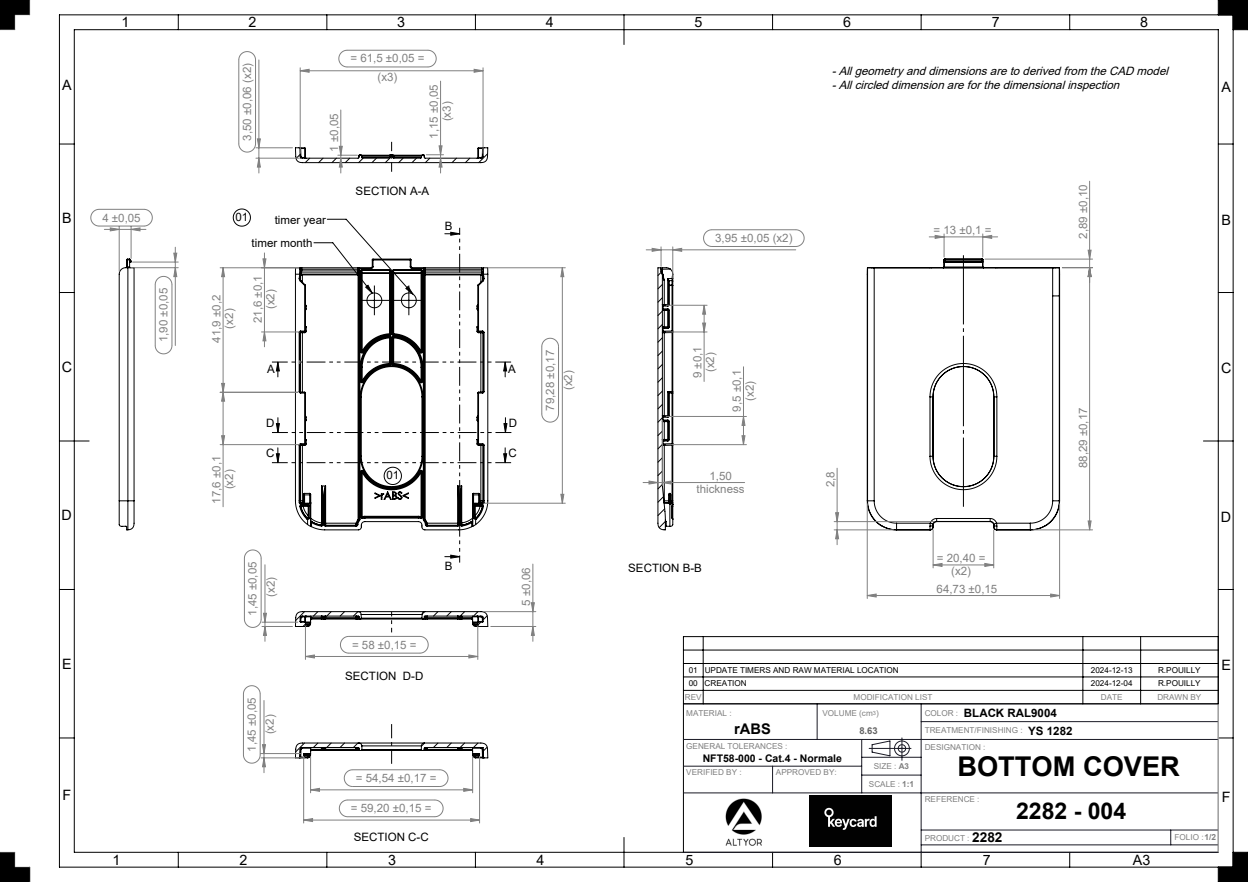
[picture p72: page 1]
timer month; timer year; SECTION A-A; thickness 9 ±0,1 (x2); SECTION B-B; SECTION C-C; SECTION D-D; NFT58-000 - Cat.4 - Normale; rABS; BLACK RAL9004; VERIFIED BY :; APPROVED BY:; BOTTOM COVER; DESIGNATION :; TREATMENT/FINISHING :; VOLUME (cm3); COLOR :; GENERAL TOLERANCES :; MATERIAL :; SIZE : A3; SCALE :

- All geometry and dimensions are to derived from the CAD model
- All circled dimension are for the dimensional inspection

01 | UPDATE TIMERS AND RAW MATERIAL LOCATION | 2024-12-13 | R.POUILLY
00 | CREATION | 2024-12-04 | R.POUILLY
REV | MODIFICATION LIST | DATE | DRAWN BY

REFERENCE : 2282 - 004

2282 PRODUCT : | FOLIO : 1/2

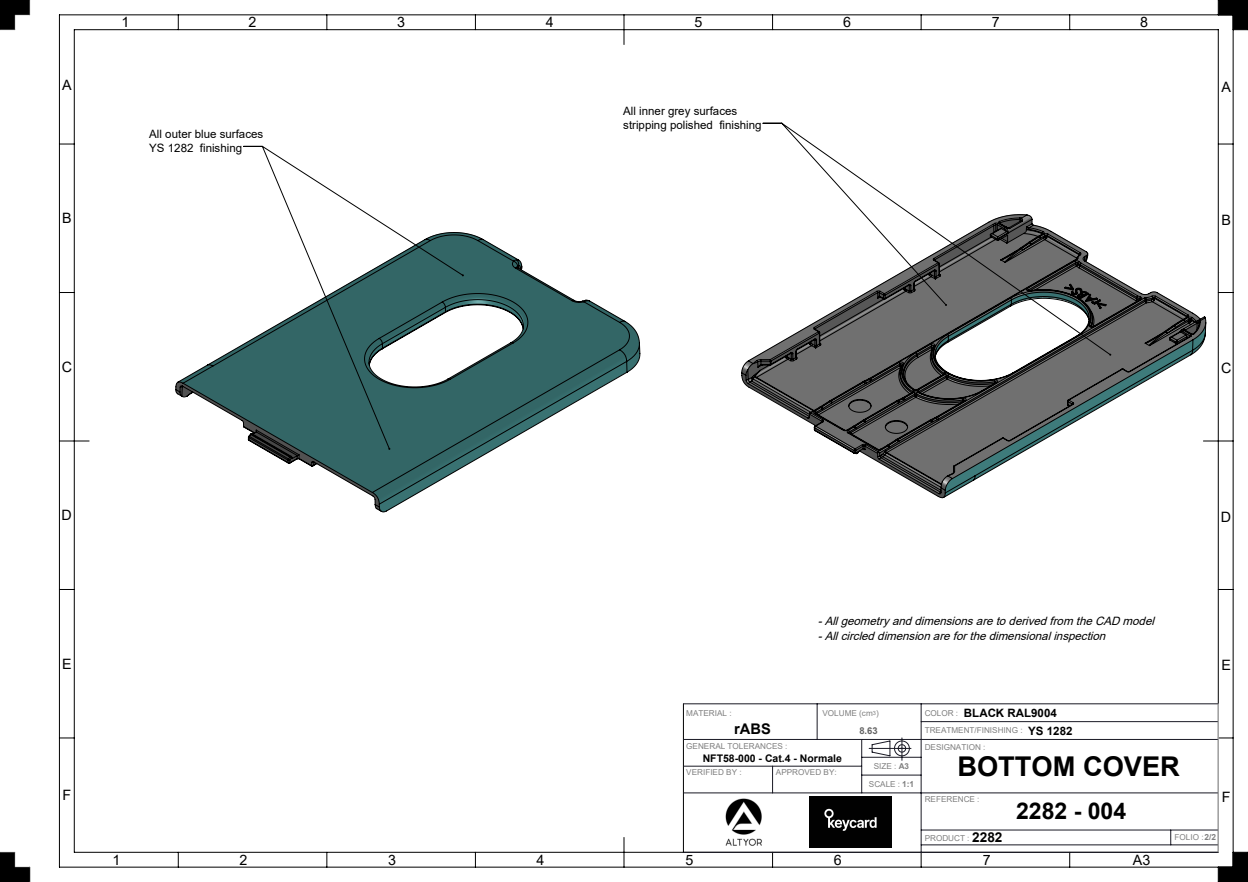
[picture p73: page 2]
rABS; BLACK RAL9004; VERIFIED BY :; APPROVED BY:; BOTTOM COVER; TREATMENT/FINISHING :; VOLUME (cm3); COLOR :; MATERIAL :; SIZE : A3; SCALE :

All inner grey surfaces

stripping polished finishing All outer blue surfaces
YS 1282 finishing

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

GENERAL TOLERANCES : NFT58-000 - Cat.4 - Normale | | DESIGNATION :

REFERENCE : 2282 - 004

2282 PRODUCT : | FOLIO : 2/2
