keycard-tech/keycard-shell/hardware/shell/prototype_P2/mechanical/parts/2282-005-KEYBOARDSLEEVE-V02-20241219.PDF

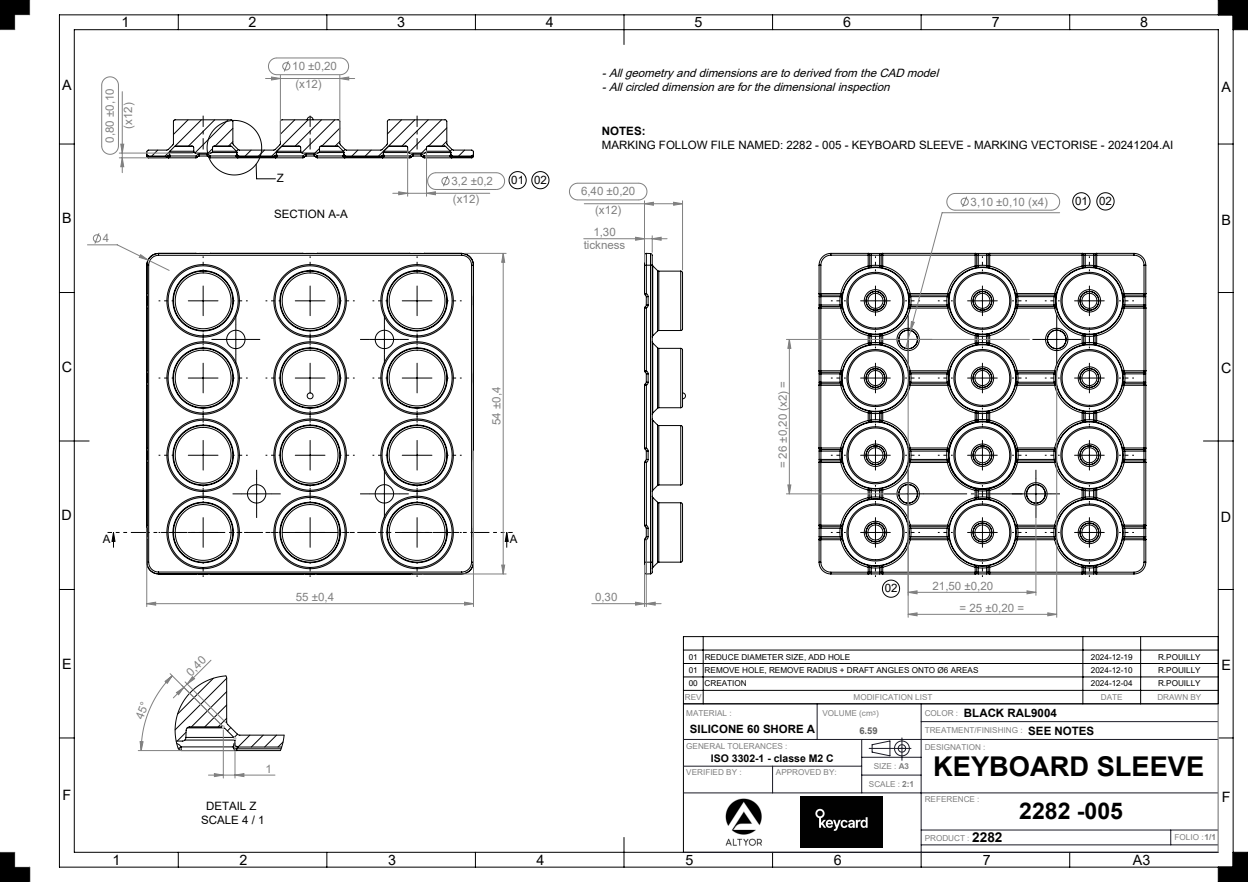
[picture p74: page 1]
SECTION A-A; DETAIL Z SCALE 4 / 1; ISO 3302-1 - classe M2 C; SILICONE 60 SHORE A; SEE NOTES; BLACK RAL9004; VERIFIED BY :; APPROVED BY:; KEYBOARD SLEEVE; DESIGNATION :; TREATMENT/FINISHING :; VOLUME (cm3); COLOR :; GENERAL TOLERANCES :; MATERIAL :; SIZE : A3; SCALE :

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

NOTES:
MARKING FOLLOW FILE NAMED: 2282 - 005 - KEYBOARD SLEEVE - MARKING VECTORISE - 20241204.AI

01 | REDUCE DIAMETER SIZE, ADD HOLE | 2024-12-19 | R.POUILLY
01 | REMOVE HOLE, REMOVE RADIUS + DRAFT ANGLES ONTO Ø6 AREAS | 2024-12-10 | R.POUILLY
00 | CREATION | 2024-12-04 | R.POUILLY
REV | MODIFICATION LIST | DATE | DRAWN BY

REFERENCE : 2282 -005

2282 PRODUCT : | FOLIO : 1/1
