keycard-tech/keycard-shell/hardware/shell/prototype_P2/mechanical/parts/2282-007-CAMERAWINDOW-V00-20241128.PDF

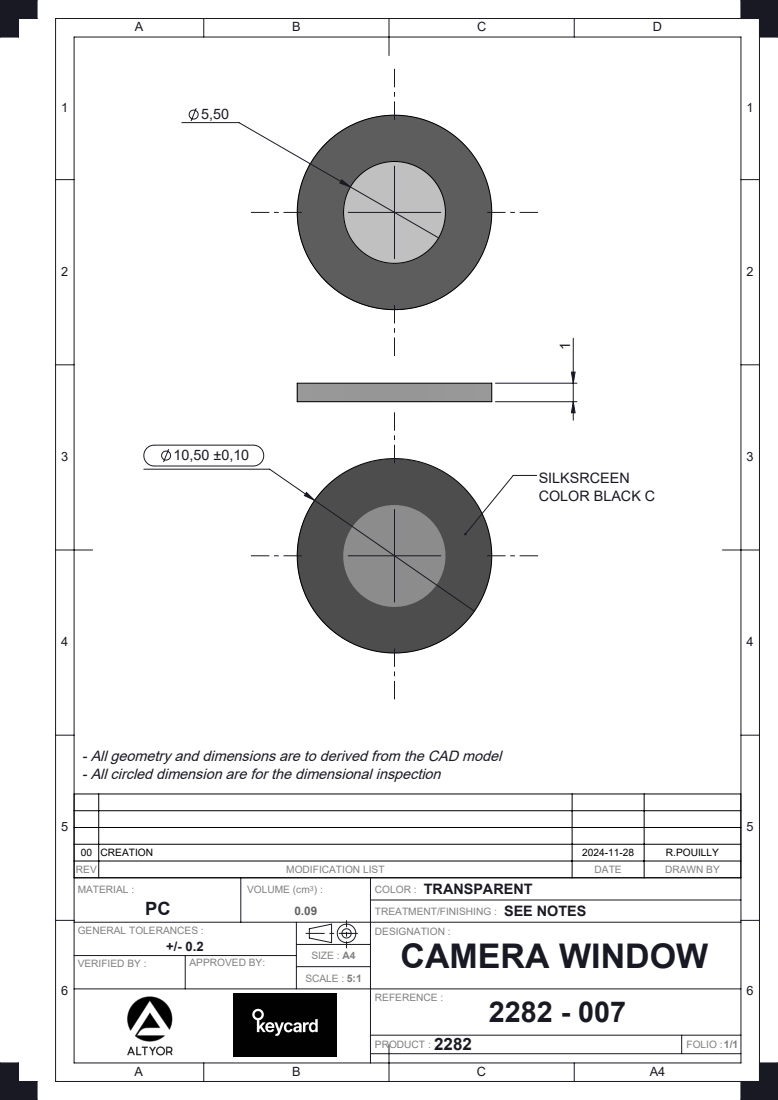
[picture p75: page 1]
COLOR BLACK C; SCALE :; SIZE : A4; MATERIAL :; GENERAL TOLERANCES :; VOLUME (cm3) :; COLOR :; TREATMENT/FINISHING : DESIGNATION :; VERIFIED BY :; APPROVED BY:; CAMERA WINDOW; SEE NOTES

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

00 | CREATION | 2024-11-28 | R.POUILLY
REV | MODIFICATION LIST | DATE | DRAWN BY

REFERENCE : 2282 - 007

PRODUCT : | FOLIO : 1/1
