keycard-tech/keycard-shell/hardware/shell/prototype_P2/mechanical/parts/2282-008-WINDOWADHESIVE-V00-20241128.PDF

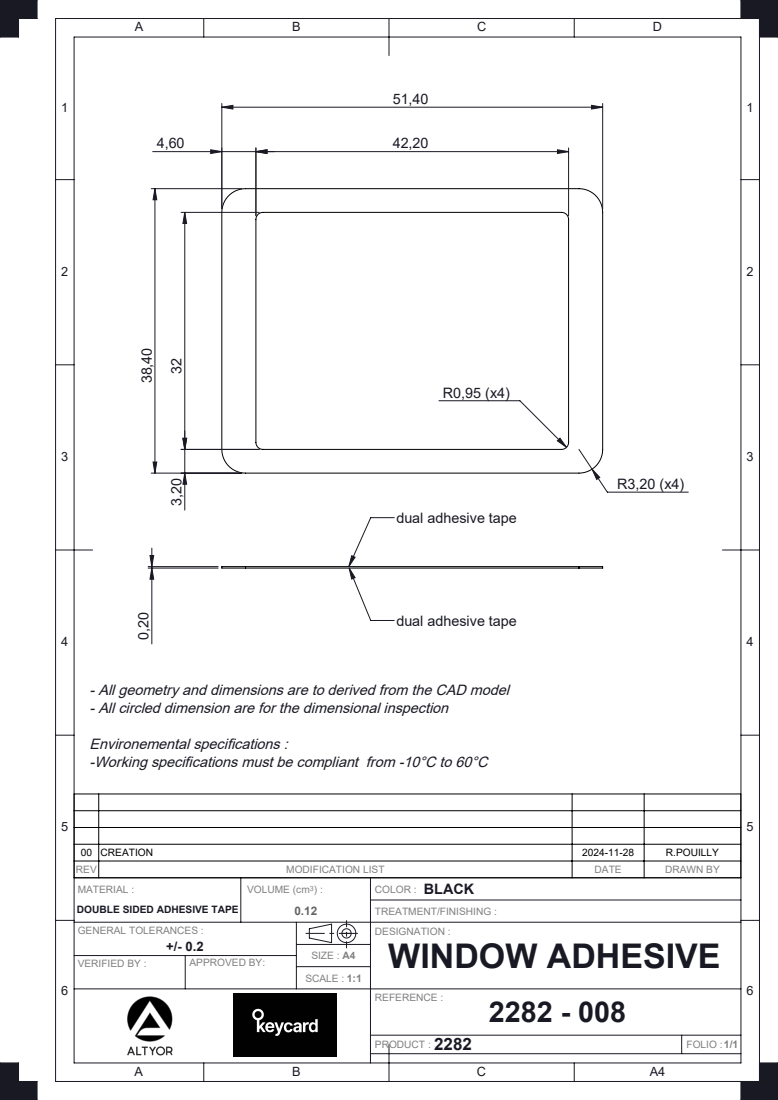
[picture p76: page 1]
SCALE :; SIZE : A4; GENERAL TOLERANCES :; TREATMENT/FINISHING : DESIGNATION :; VERIFIED BY :; APPROVED BY:; WINDOW ADHESIVE

dual adhesive tape

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

00 | CREATION | 2024-11-28 | R.POUILLY
REV | MODIFICATION LIST | DATE | DRAWN BY
MATERIAL : DOUBLE SIDED ADHESIVE TAPE | VOLUME (cm3) : 0.12 | BLACK COLOR :

REFERENCE : 2282 - 008

PRODUCT : | FOLIO : 1/1
