keycard-tech/keycard-shell/hardware/shell/prototype_P2/mechanical/parts/2282-009-ANTIDUSTFOAM-V00-20241128.PDF

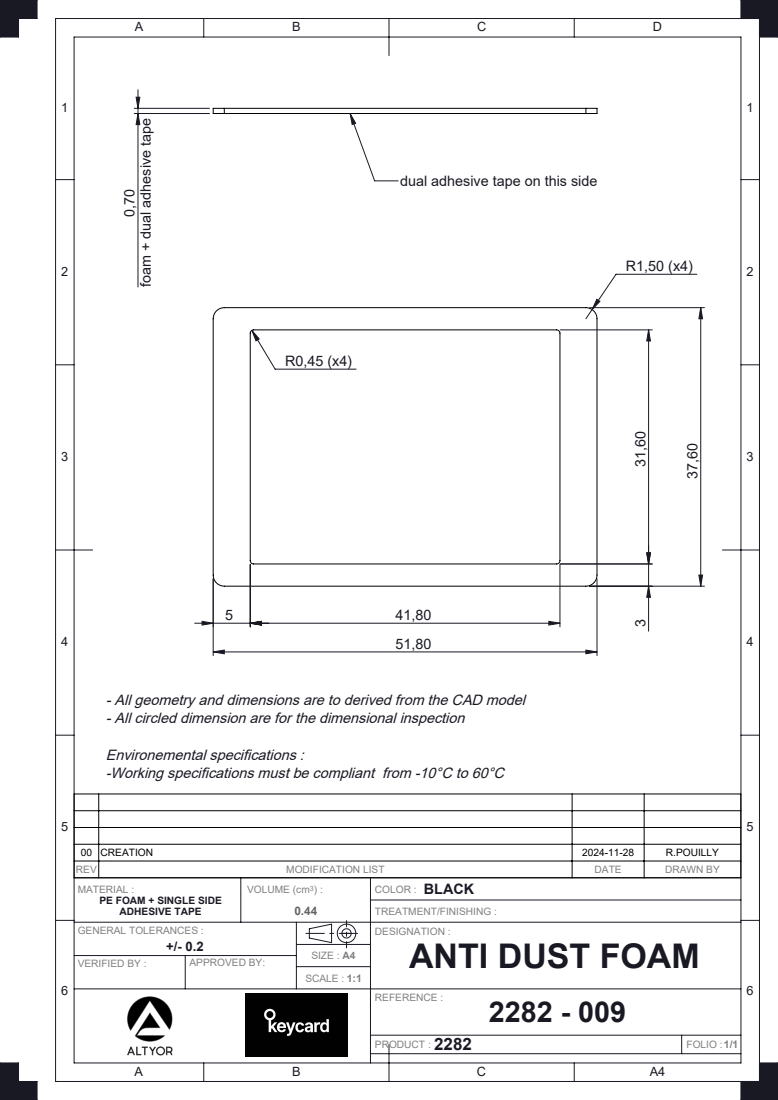
[picture p77: page 1]
SCALE :; SIZE : A4; GENERAL TOLERANCES :; TREATMENT/FINISHING : DESIGNATION :; VERIFIED BY :; APPROVED BY:; ANTI DUST FOAM

foam + dual adhesive tape

dual adhesive tape on this side

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

00 | CREATION | 2024-11-28 | R.POUILLY
REV | MODIFICATION LIST | DATE | DRAWN BY
MATERIAL : PE FOAM + SINGLE SIDE ADHESIVE TAPE | VOLUME (cm3) : 0.44 | BLACK COLOR :

REFERENCE : 2282 - 009

PRODUCT : | FOLIO : 1/1
