keycard-tech/keycard-shell/hardware/shell/prototype_P2/mechanical/parts/2282-011-CAMERAFOAM-V01-20241220.PDF

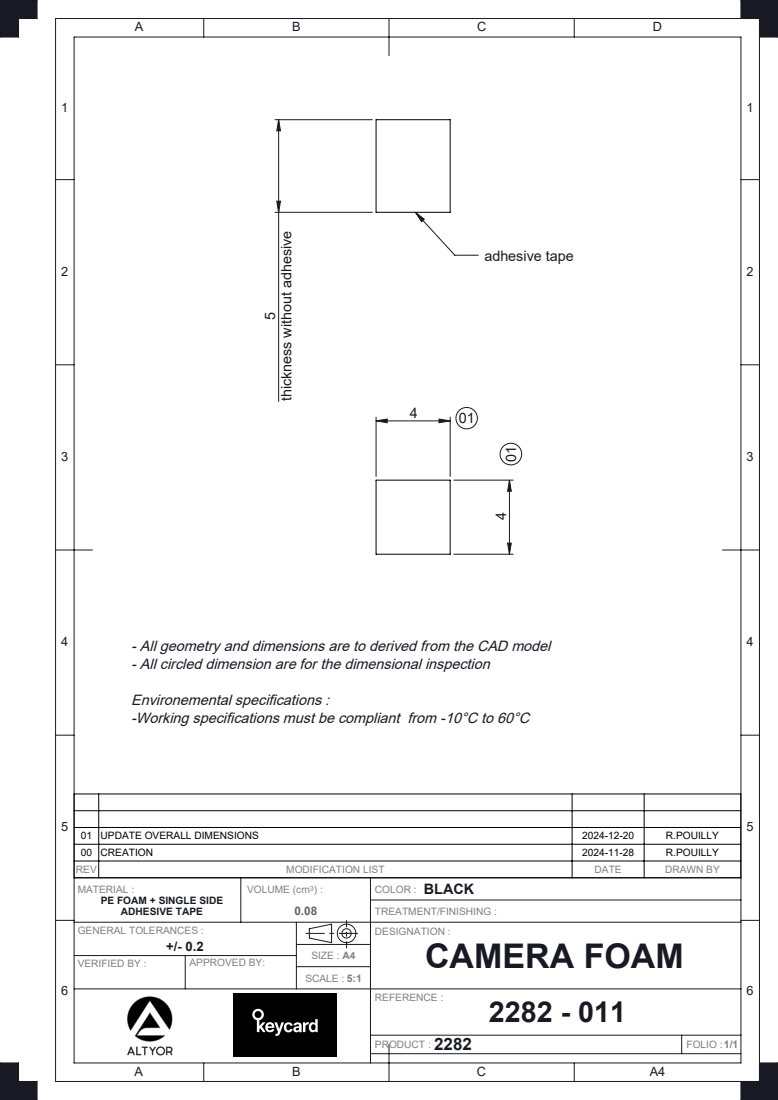
[picture p78: page 1]
adhesive tape; SCALE :; SIZE : A4; GENERAL TOLERANCES :; TREATMENT/FINISHING : DESIGNATION :; VERIFIED BY :; APPROVED BY:; CAMERA FOAM

thickness without adhesive

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

01 | UPDATE OVERALL DIMENSIONS | 2024-12-20 | R.POUILLY
00 | CREATION | 2024-11-28 | R.POUILLY
REV | MODIFICATION LIST | DATE | DRAWN BY
MATERIAL : PE FOAM + SINGLE SIDE ADHESIVE TAPE | VOLUME (cm3) : 0.08 | BLACK COLOR :

REFERENCE : 2282 - 011

PRODUCT : | FOLIO : 1/1
