keycard-tech/keycard-shell/hardware/shell/prototype_P2/electronics/FLXandKCP2282/FLX-2282-610 SCH V3.0.PDF

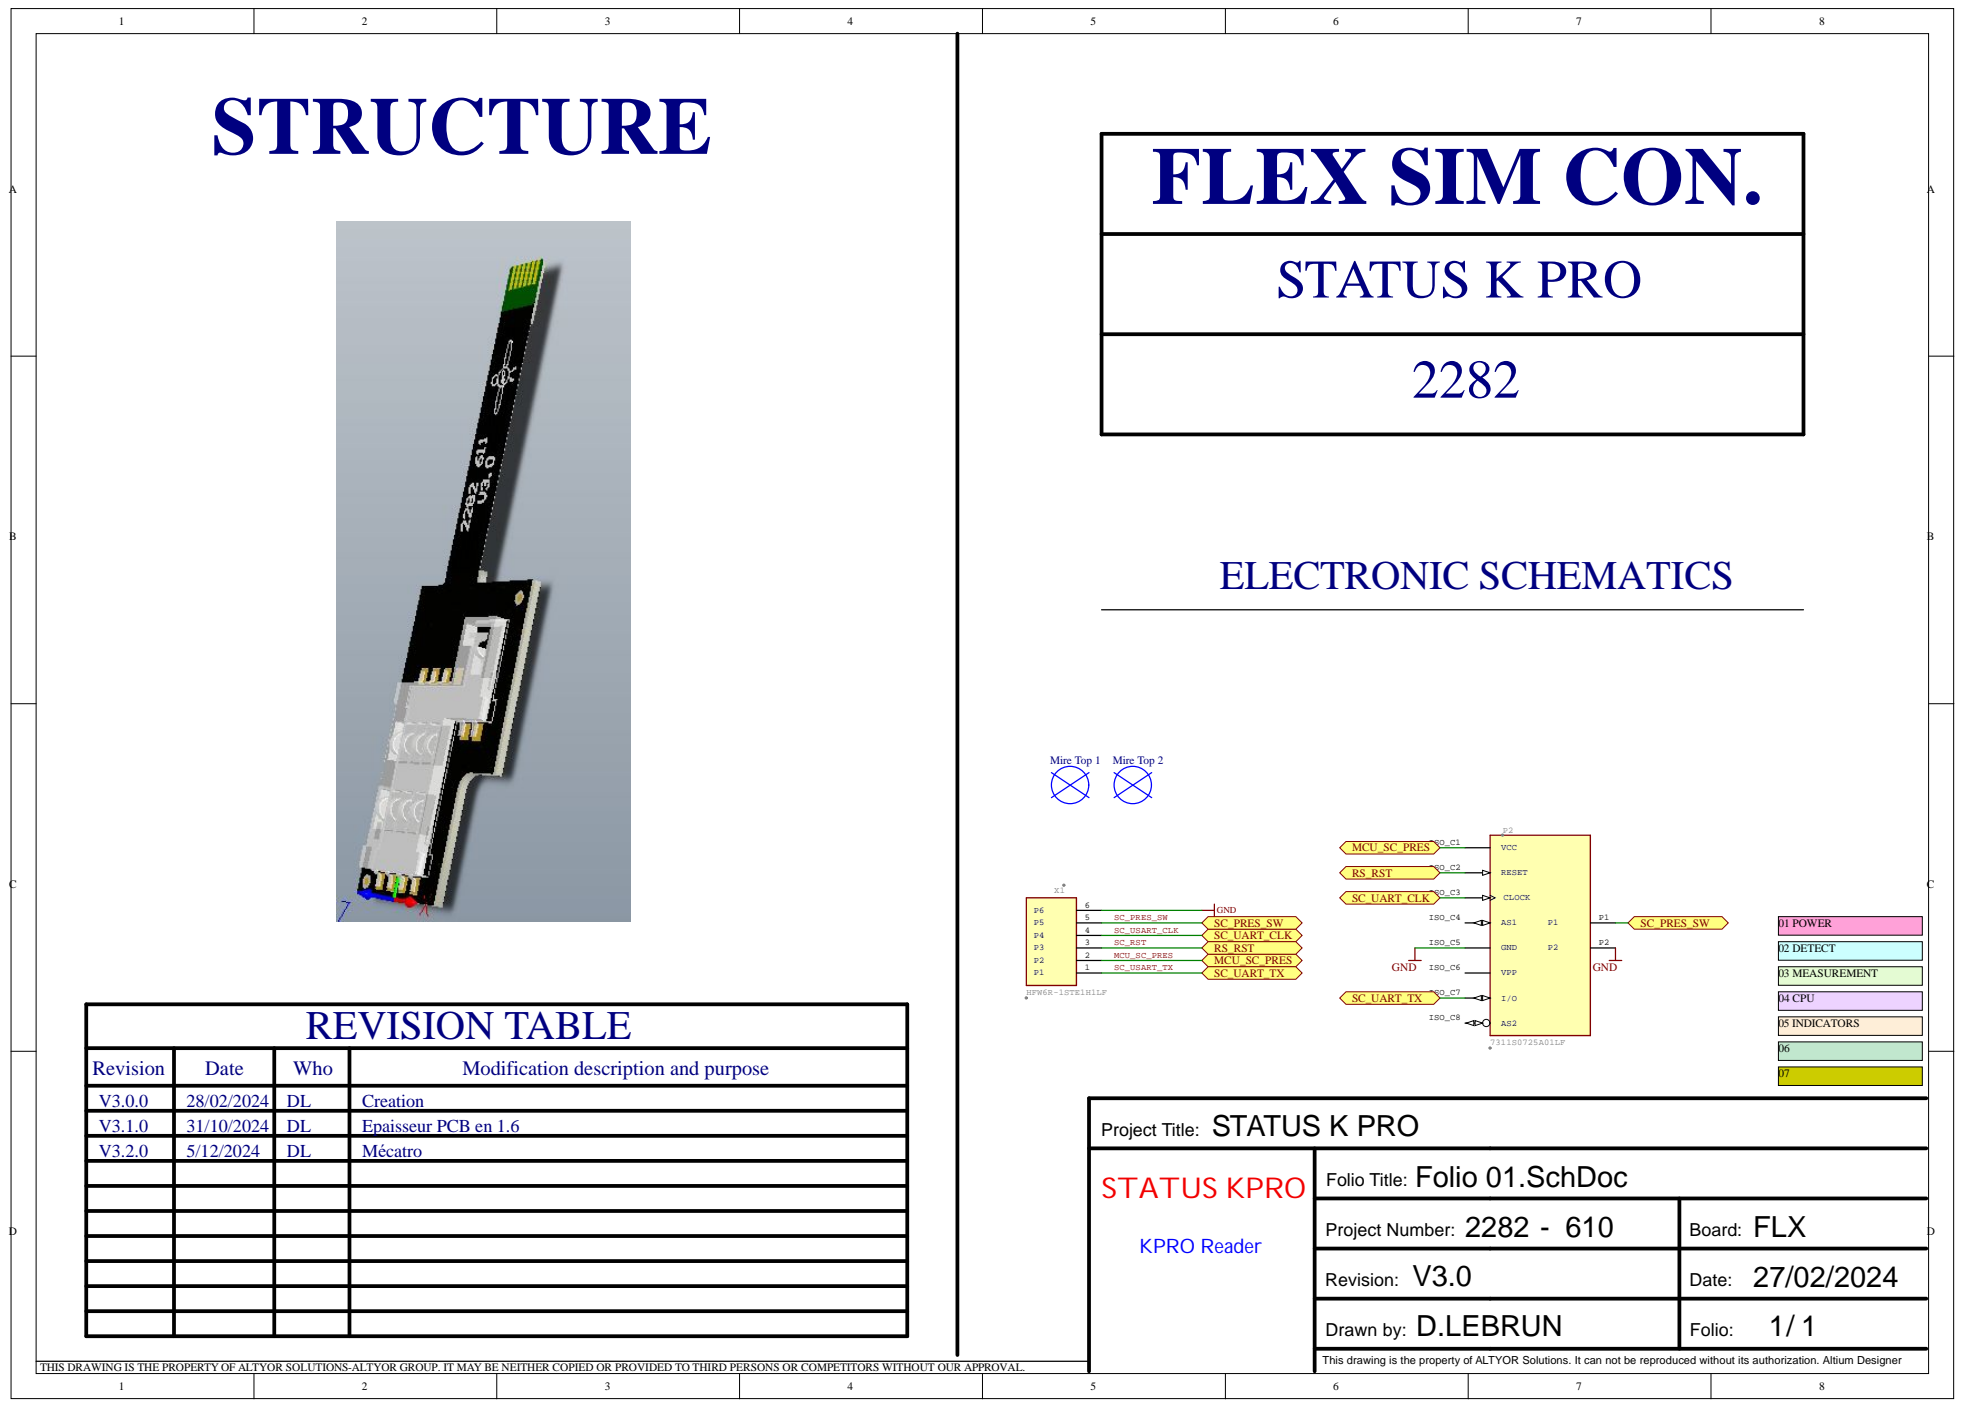
[picture p82: page 1]

Mire Top 1 Mire Top 2

Revision | Date | Who | Modification description and purpose

V3.0.0 | 28/02/2024 | DL | Creation
V3.1.0 | 31/10/2024 | DL | Epaisseur PCB en 1.6
V3.2.0 | 5/12/2024 | DL | Mécatro

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
