keycard-tech/keycard-shell/hardware/shell/serial_run/ELECTRONIC/FLX-2282-61x-V3.3.0/FLX-PCB-2282-611V3.3.PDF

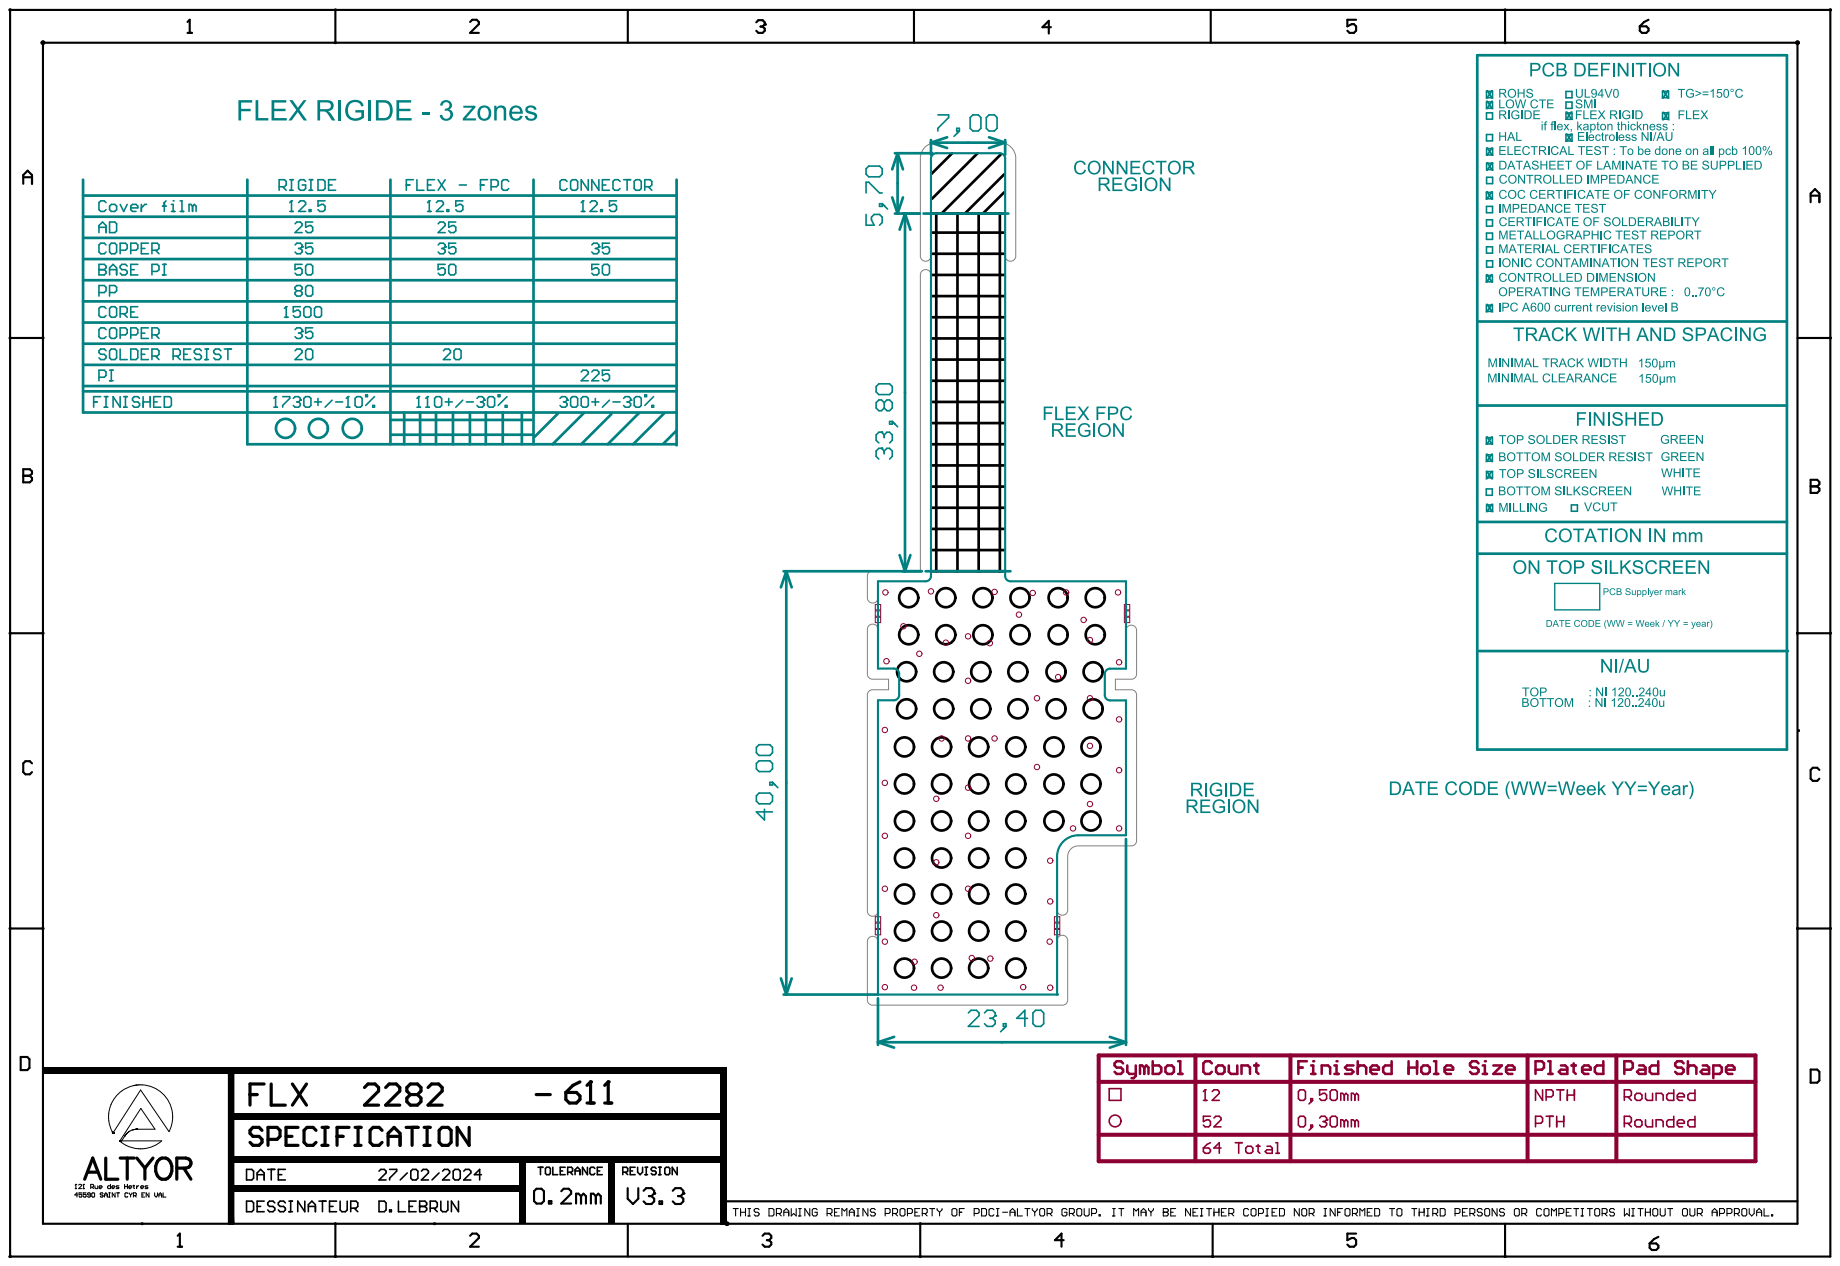
[picture p83: page 1]

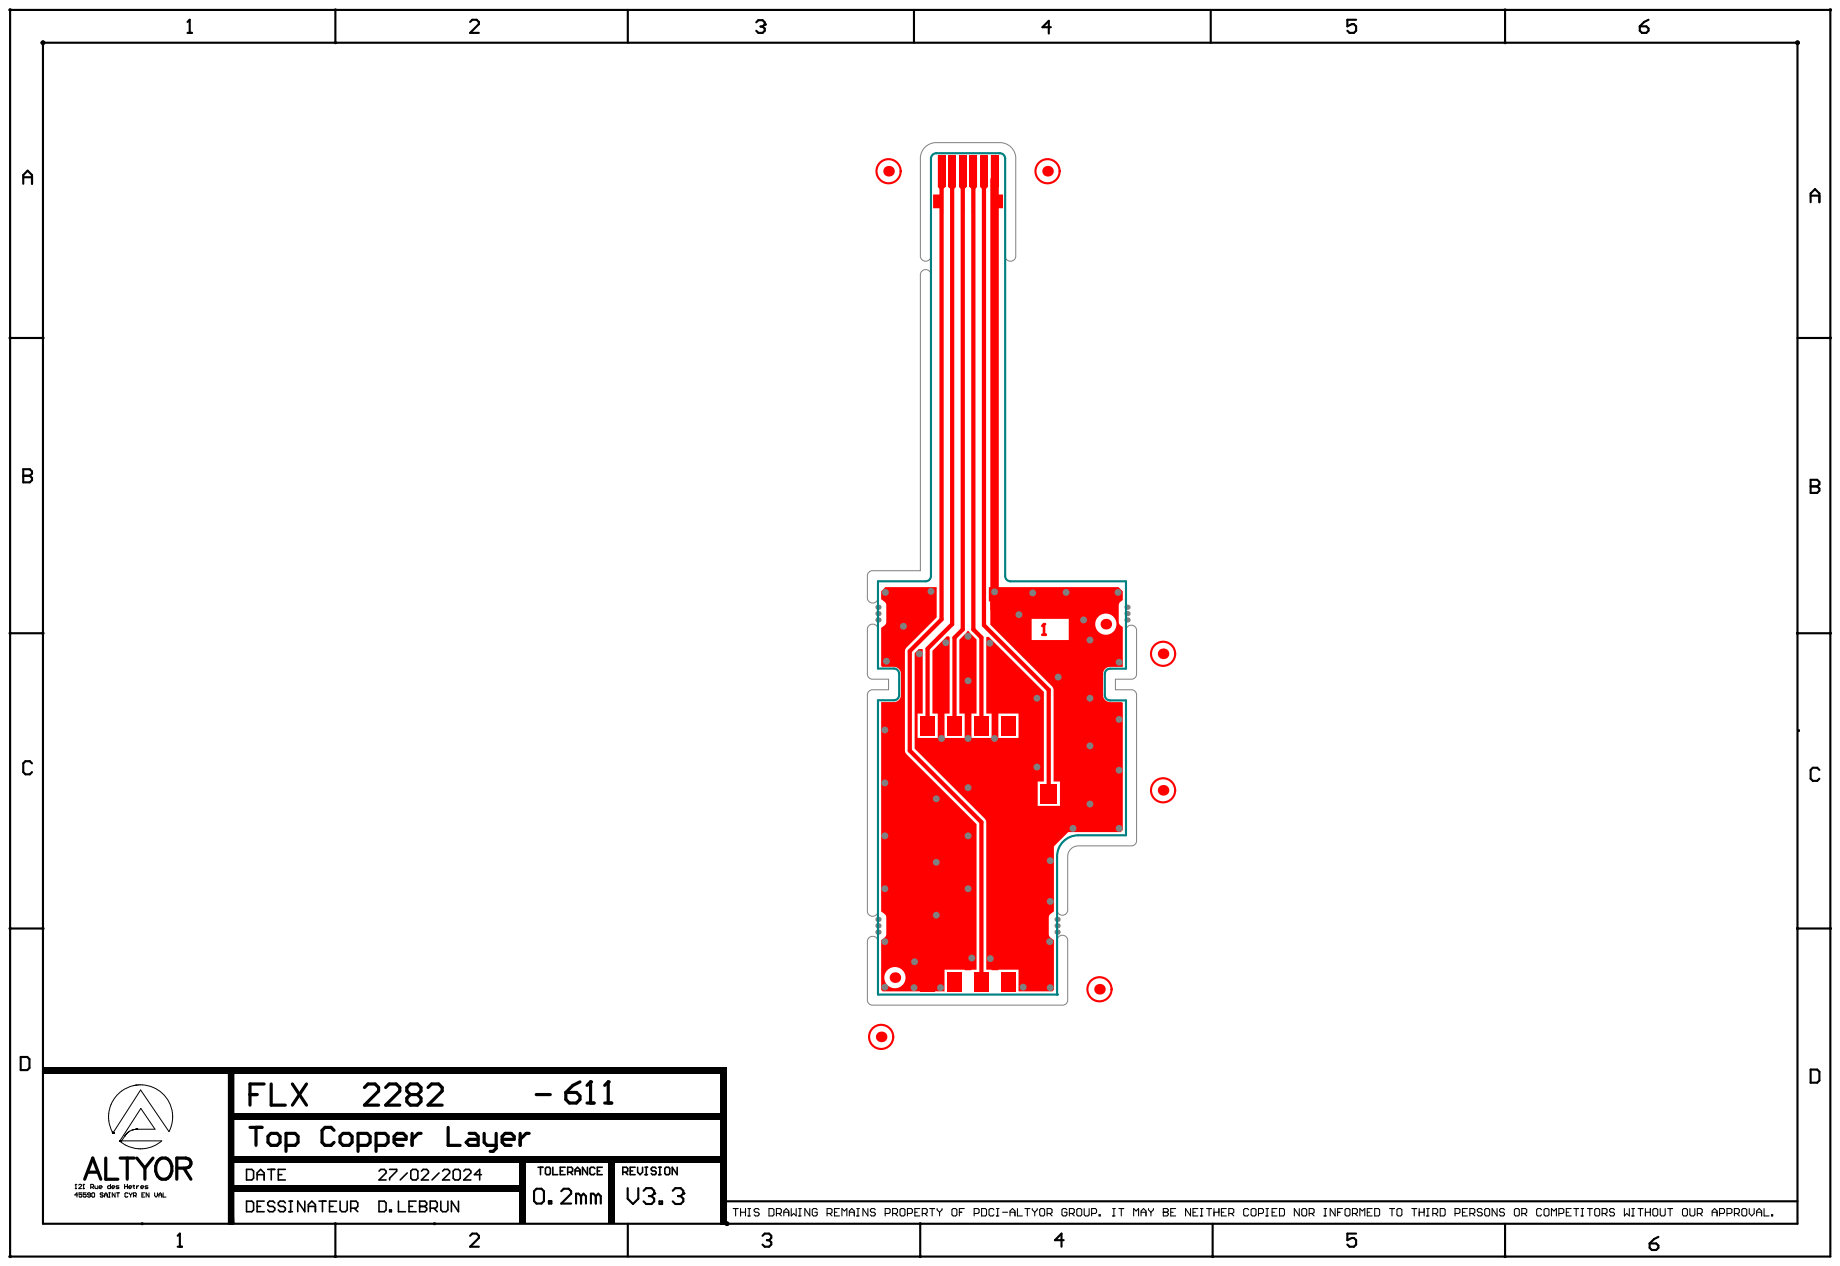
[picture p84: page 2]

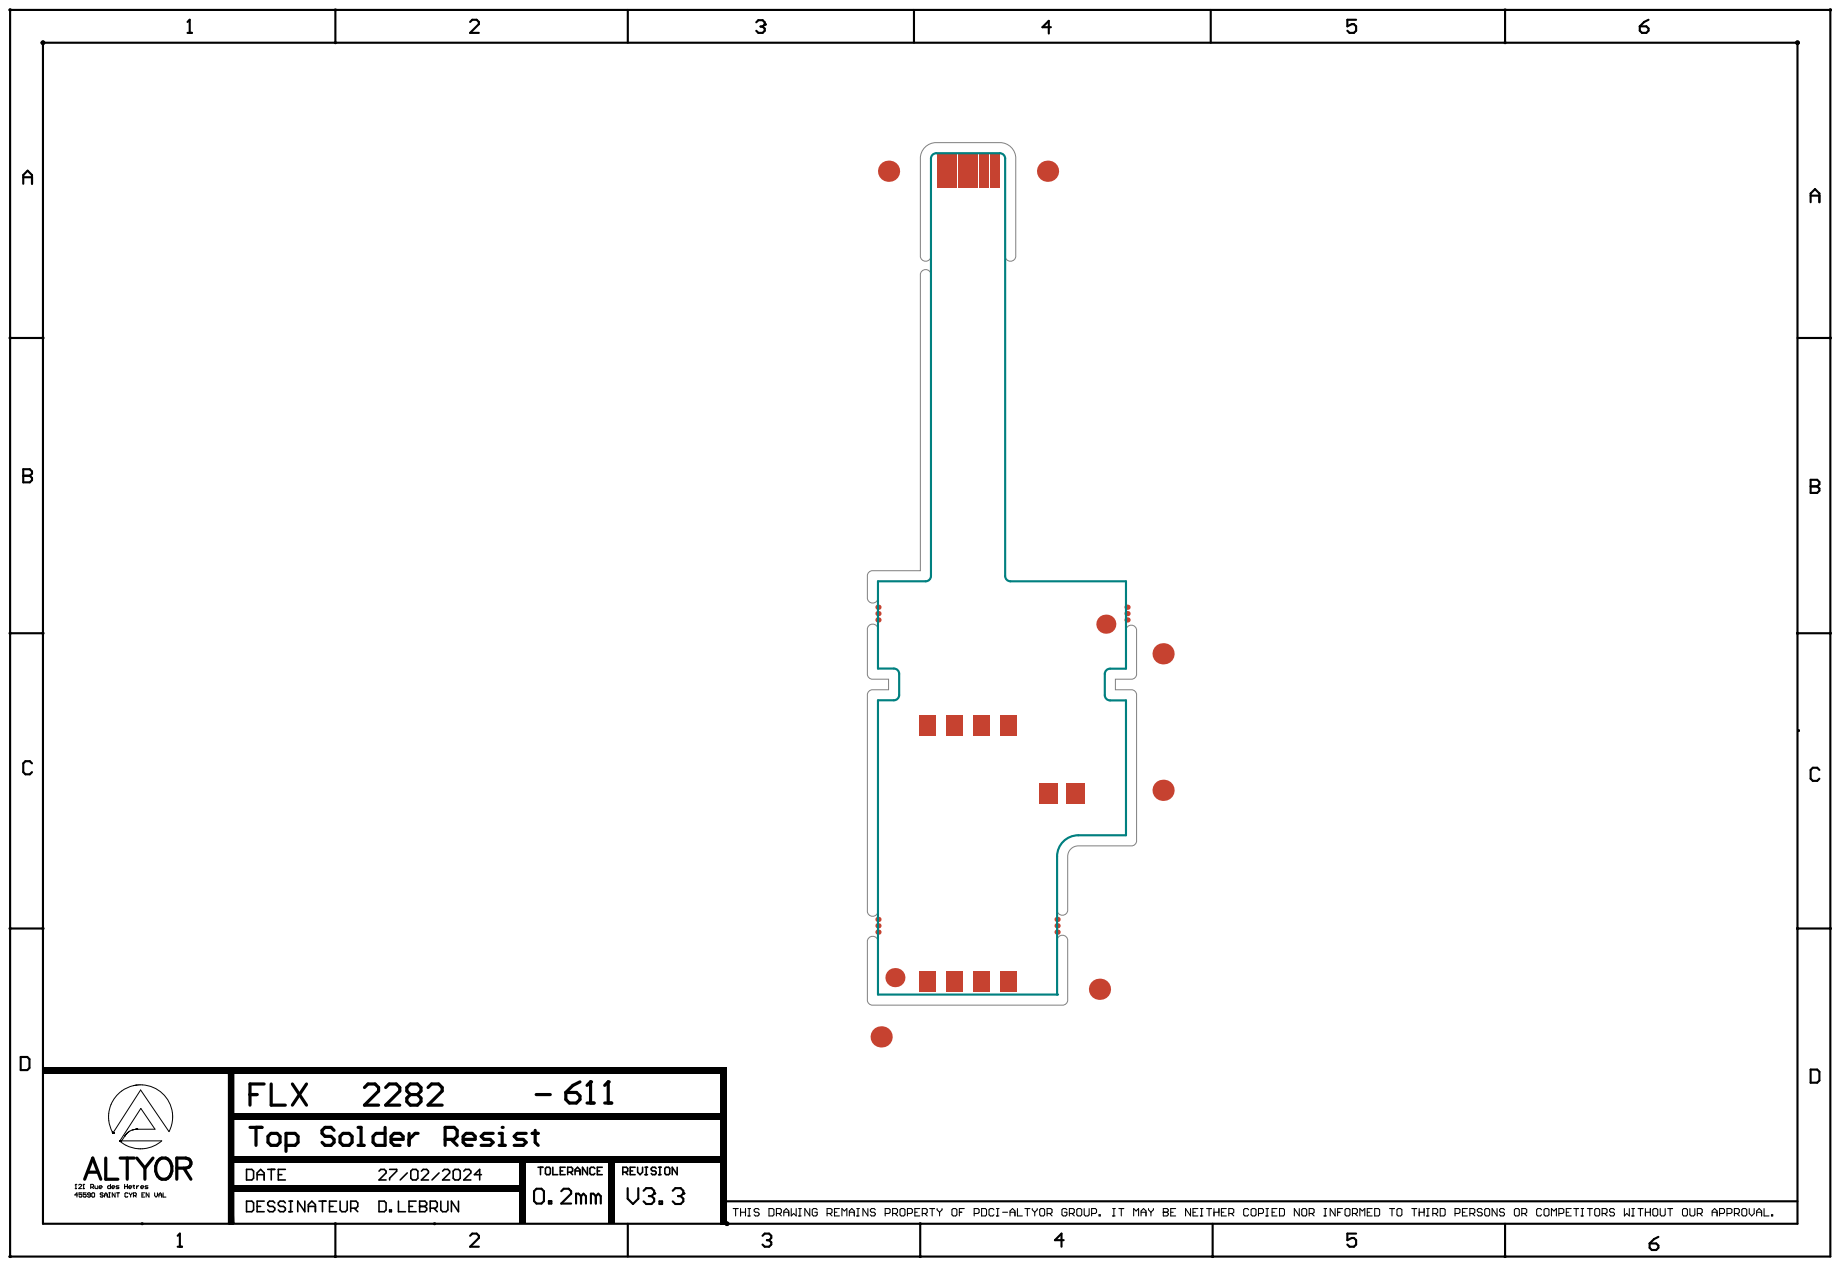
[picture p85: page 3]

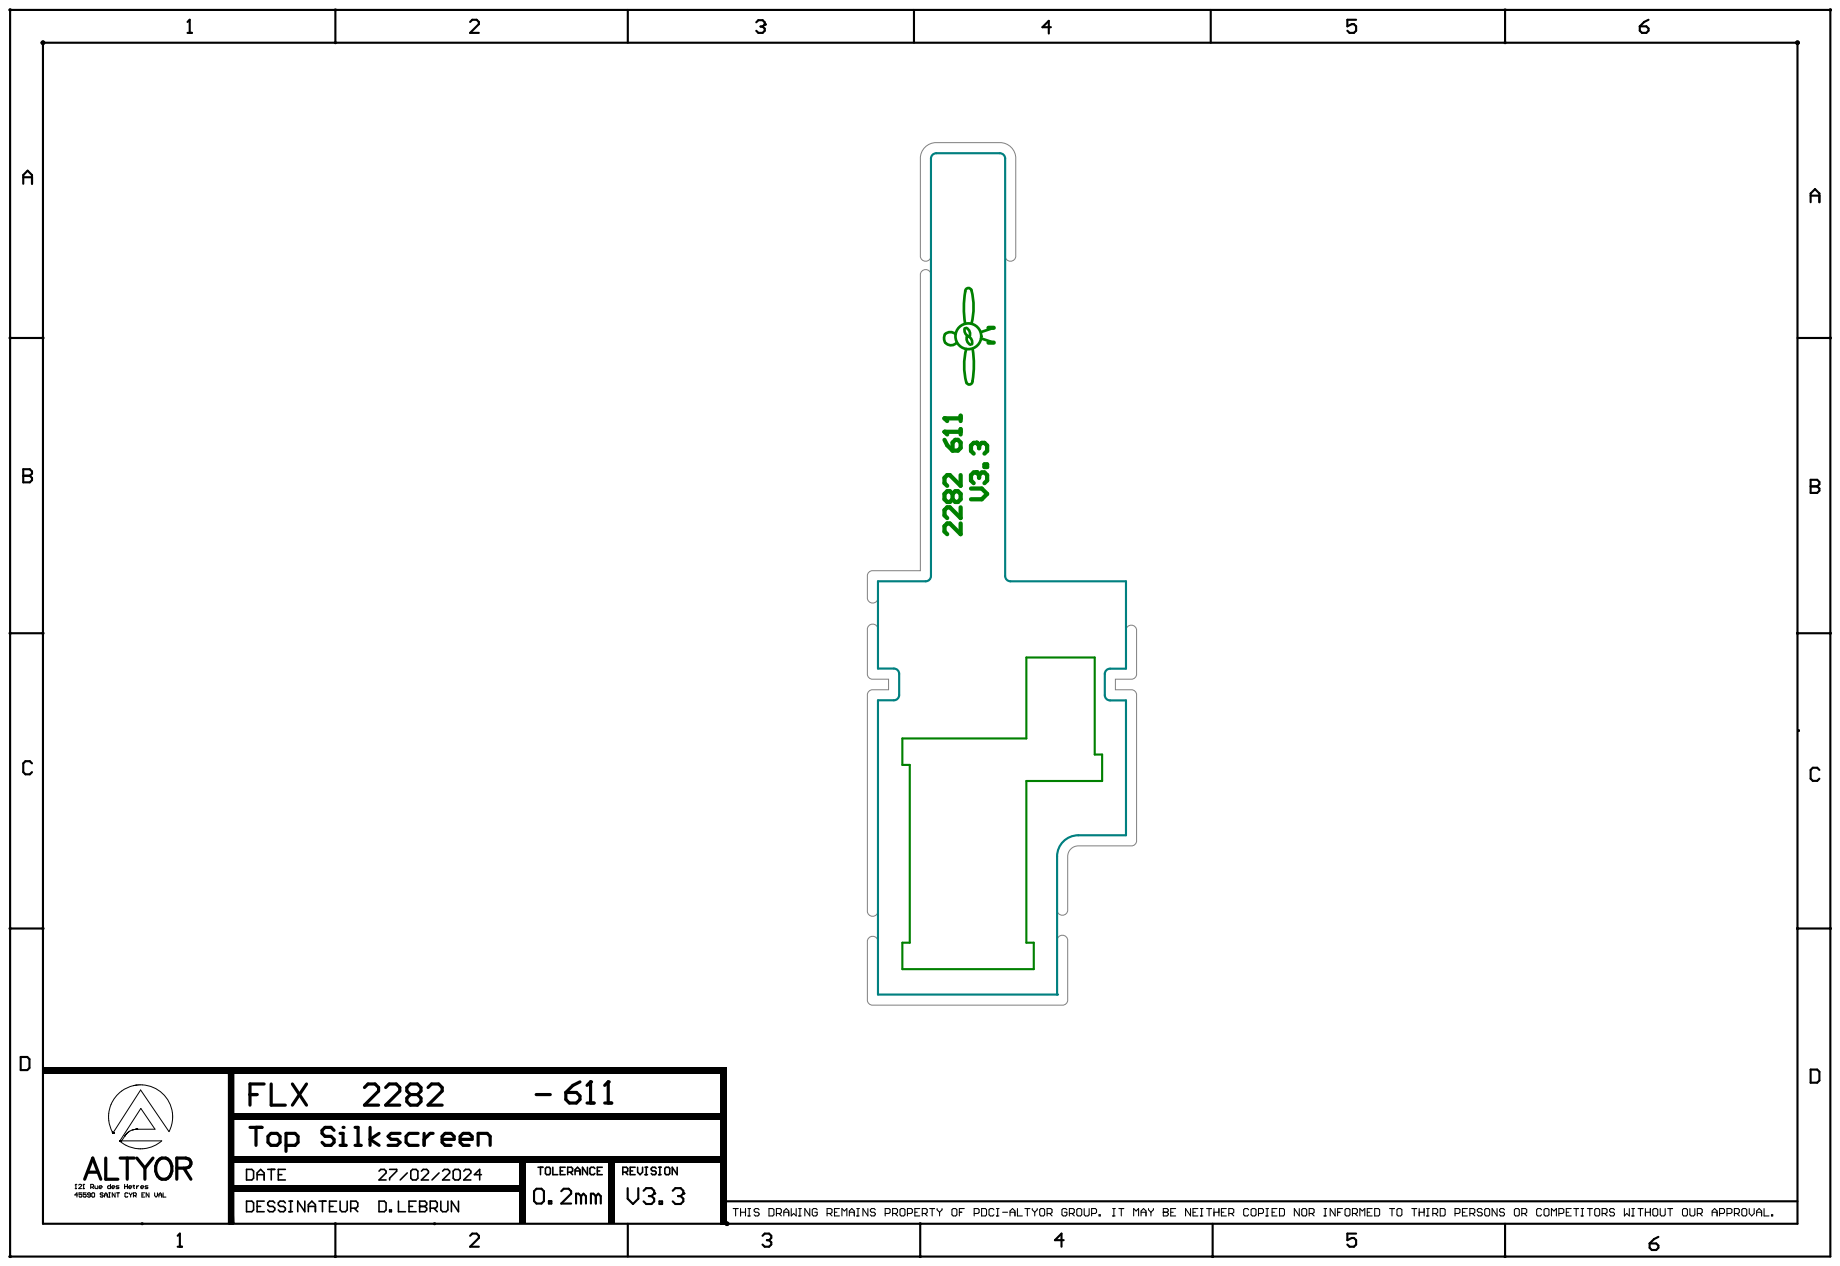
[picture p86: page 4]

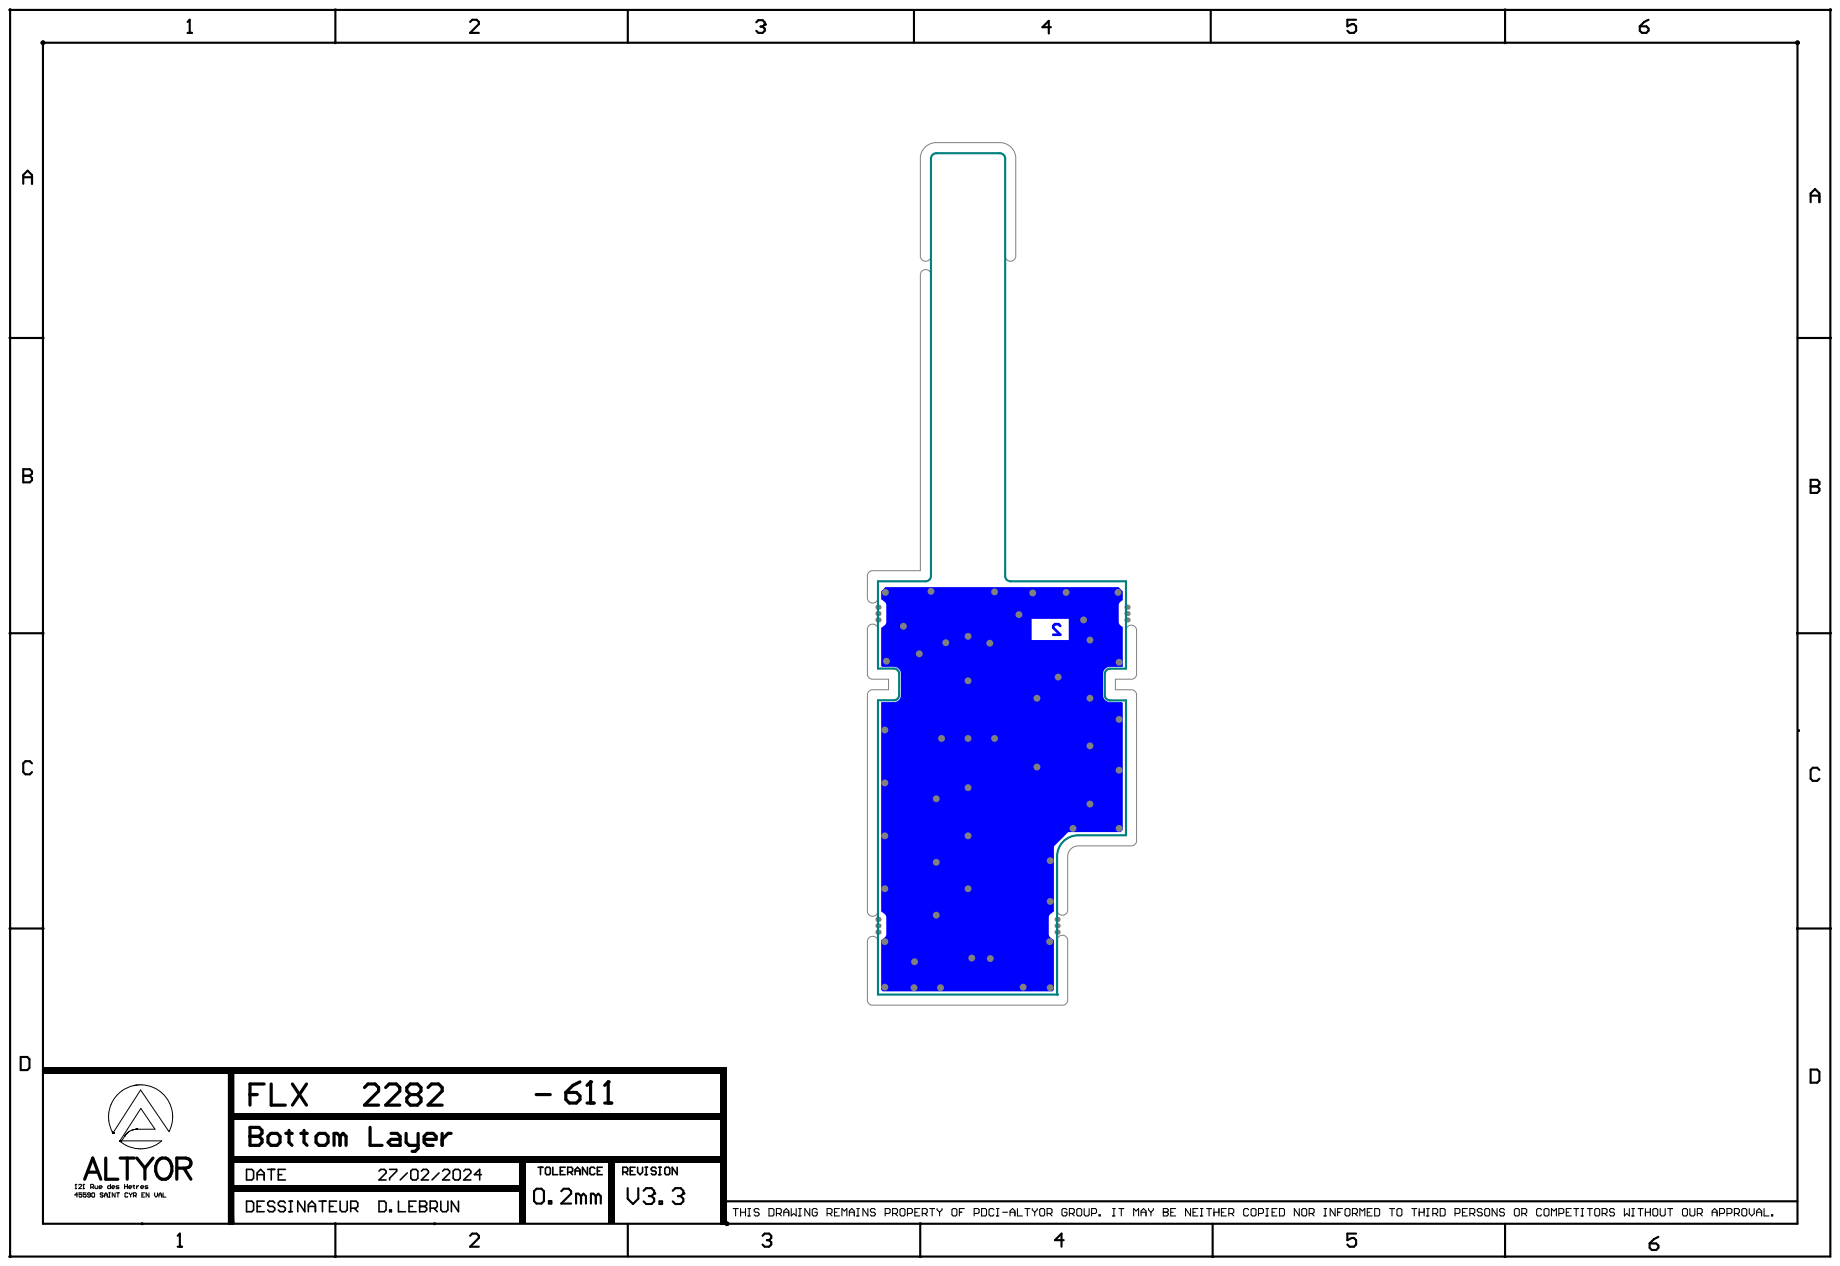
[picture p87: page 5]

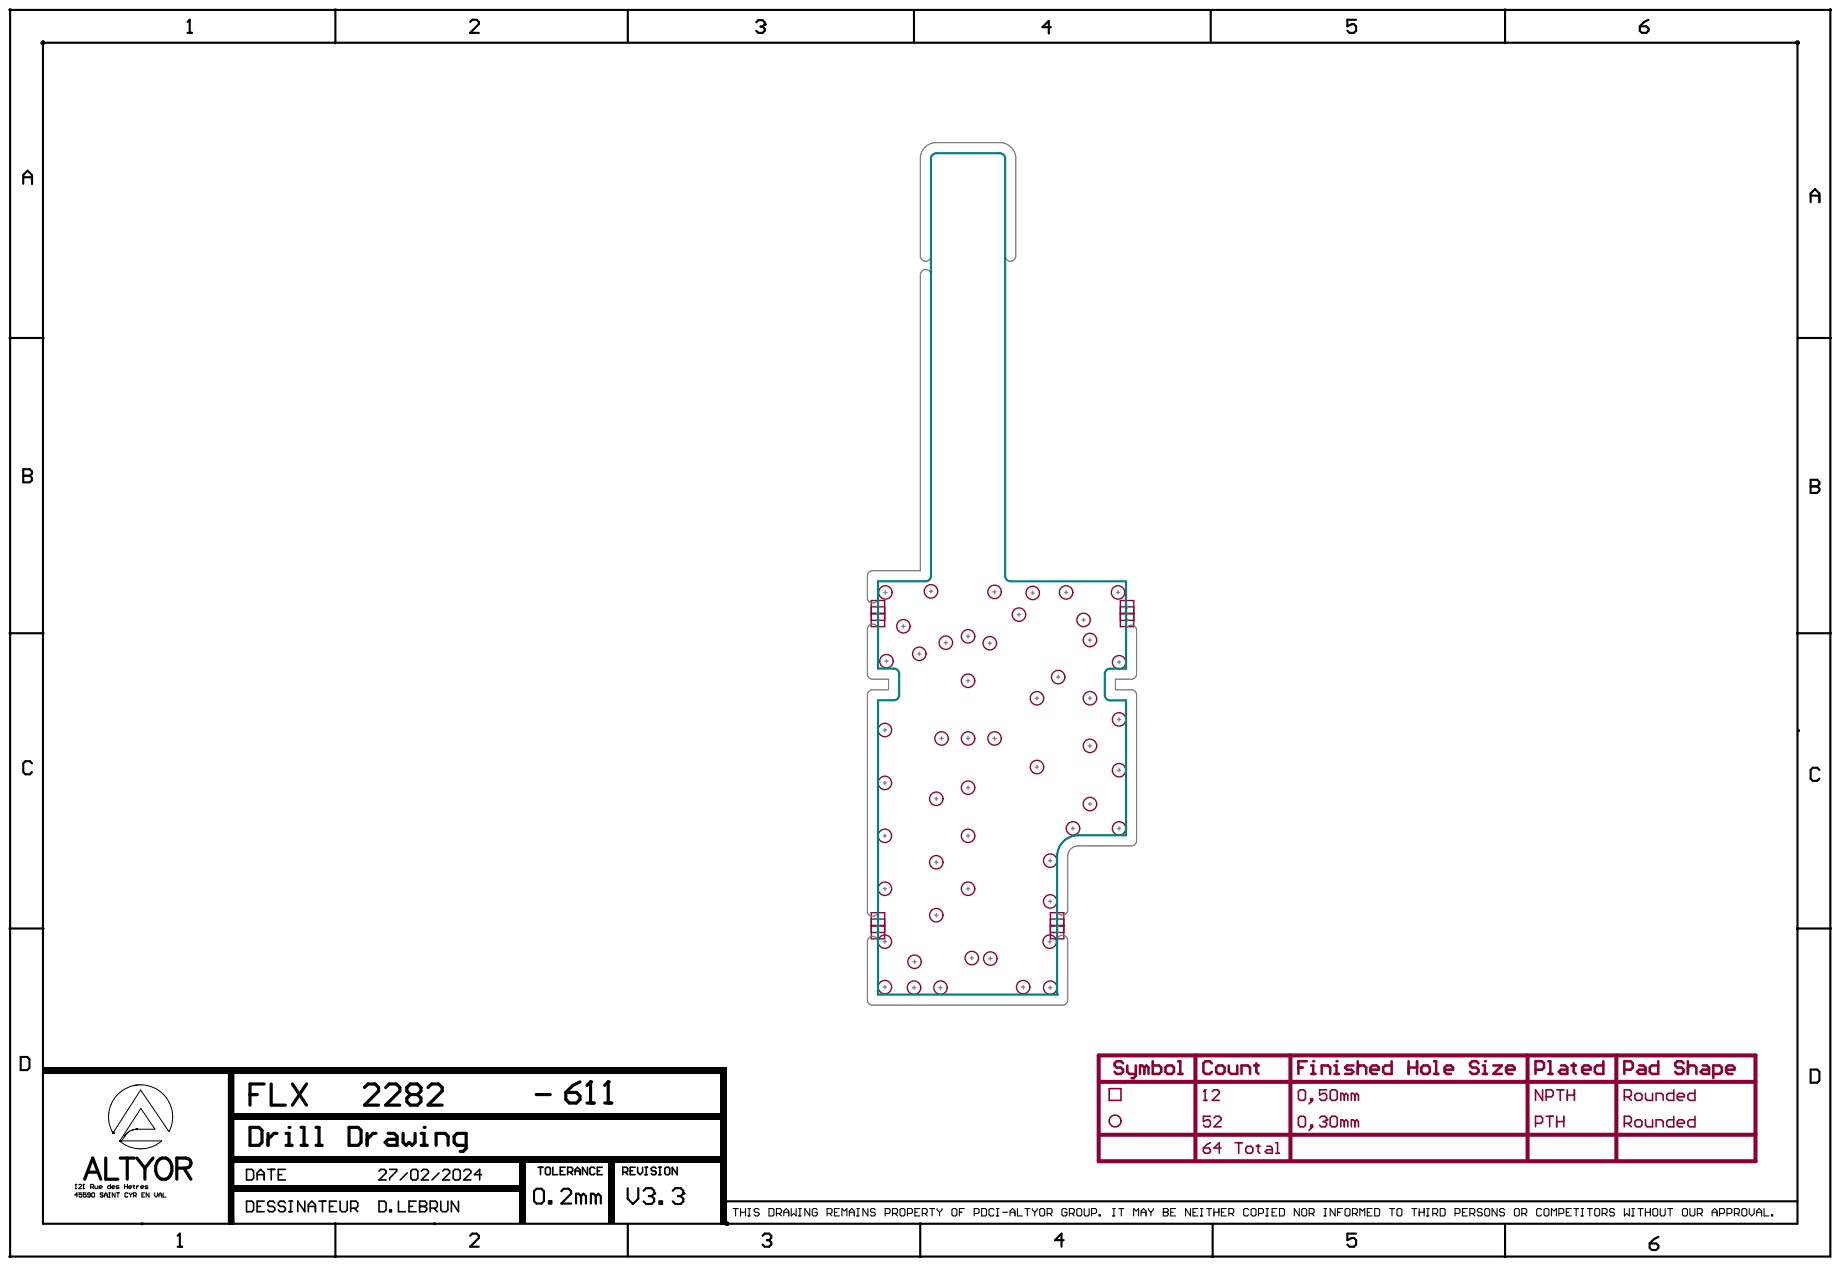
[picture p88: page 6]

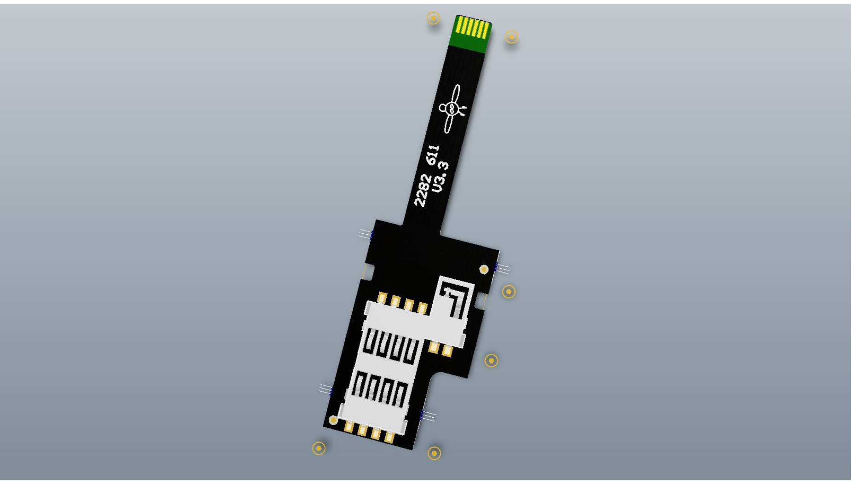
[picture p89: page 7]

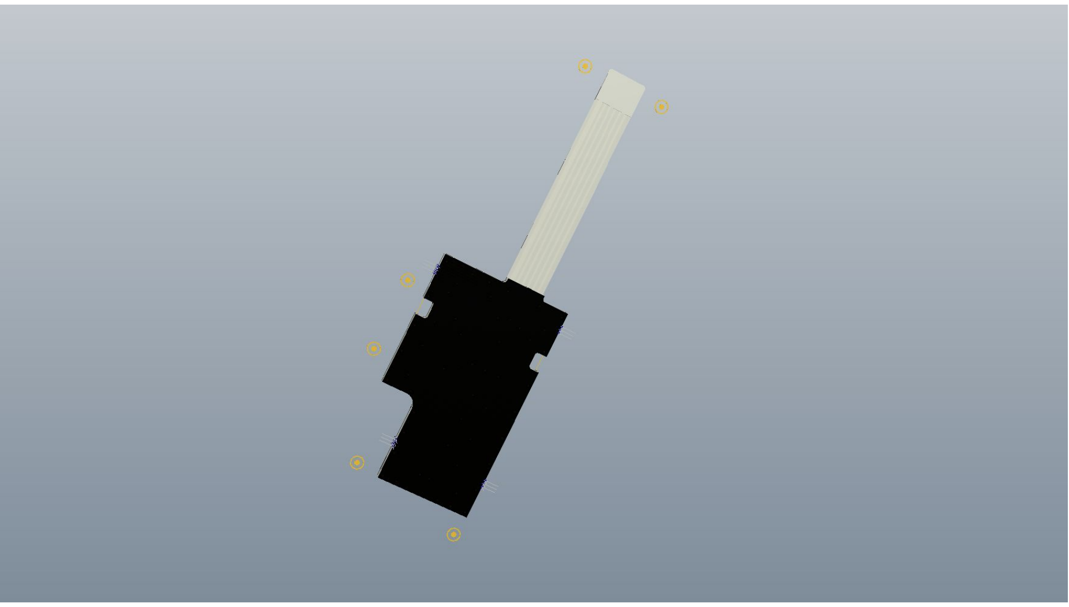
[picture p90: page 8]
