keycard-tech/keycard-shell/hardware/shell/serial_run/ELECTRONIC/FLX-2282-61x-V3.3.0/FLX-PCBA-2282-614V3.3.PDF

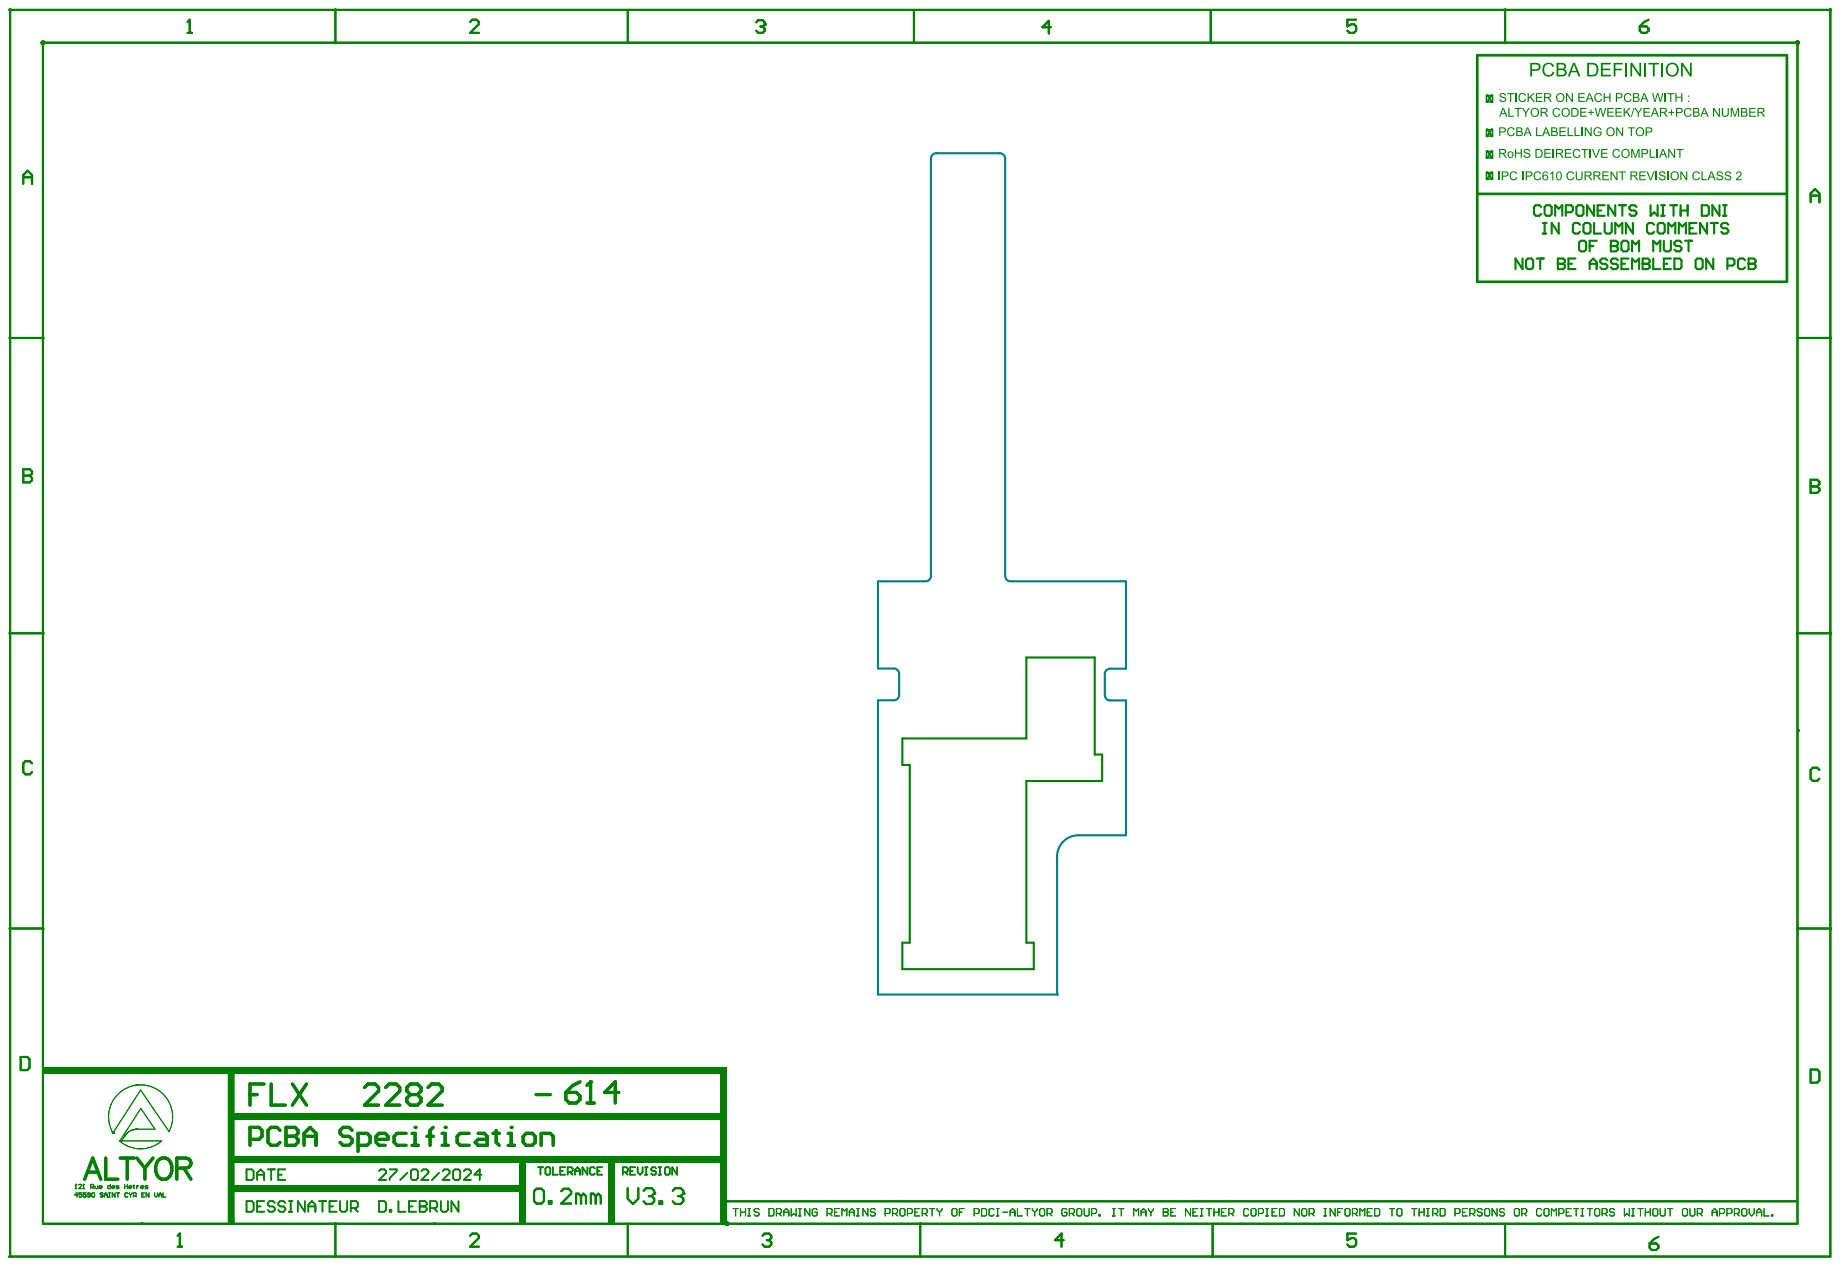
[picture p91: page 1]

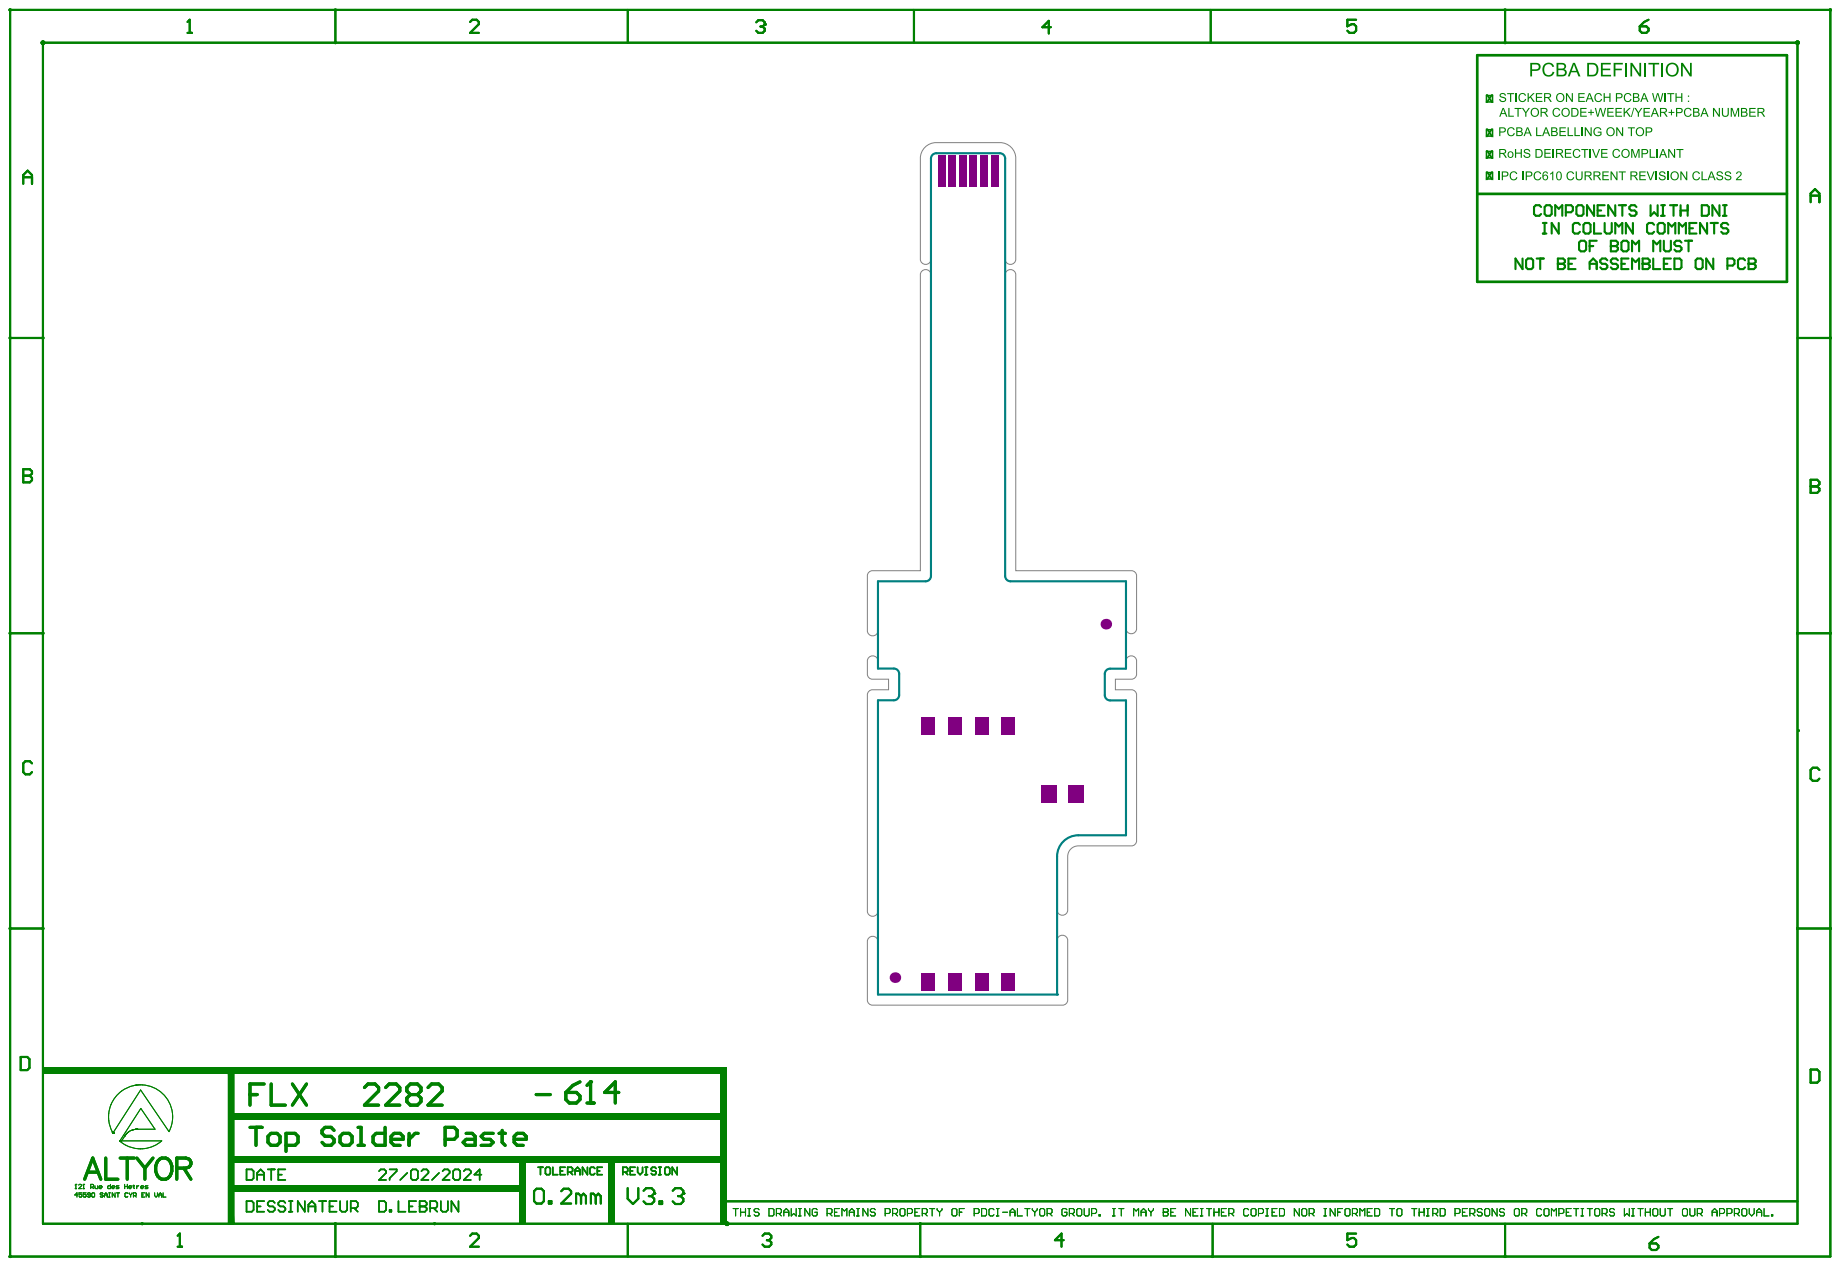
[picture p92: page 2]

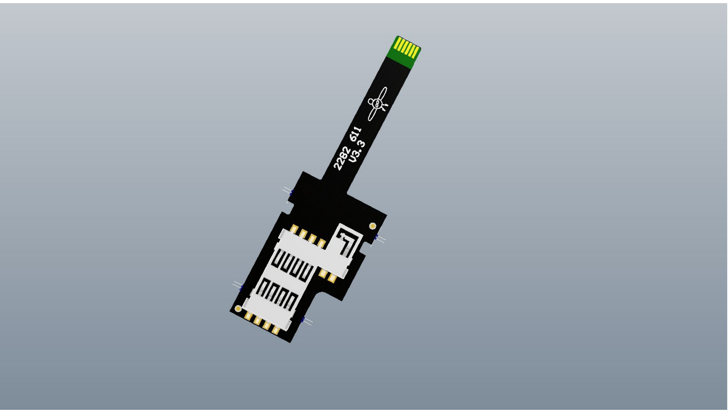
[picture p93: page 3]

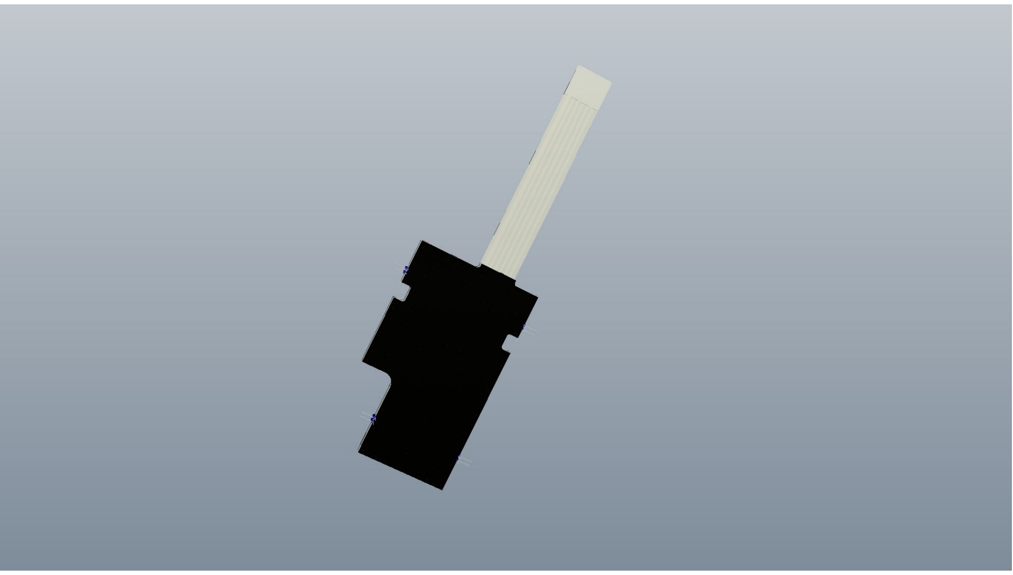
[picture p94: page 4]
