keycard-tech/keycard-shell/hardware/shell/serial_run/MECHANICAL/KBOARDSILKCREEN/2282-KEYBOARDSLEEVE-20241107.PDF

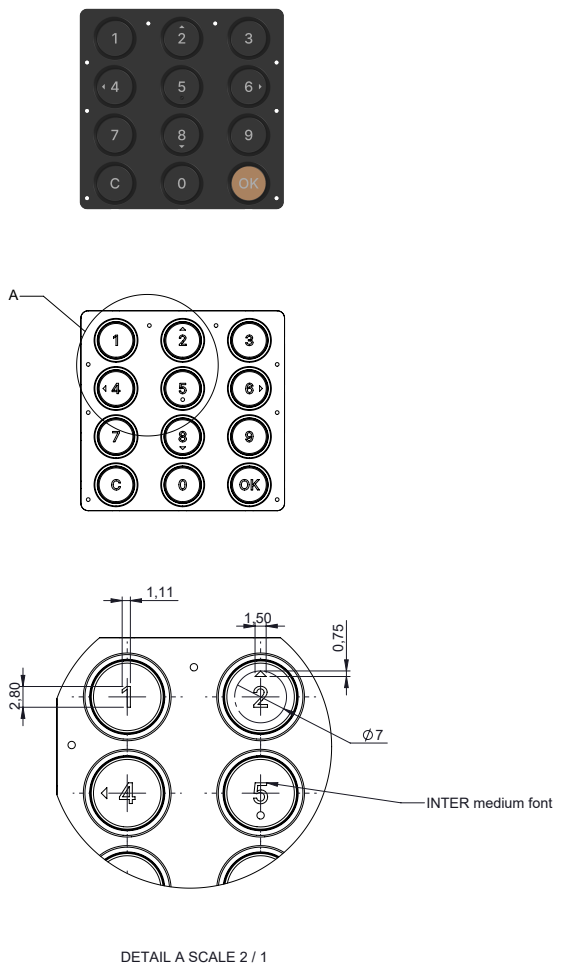
[picture p95: page 1]
DETAIL A SCALE 2 / 1

INTER medium font
