keycard-tech/keycard-shell/hardware/development_board/devboard_v1/keycard_pro_schematic.pdf

A

A

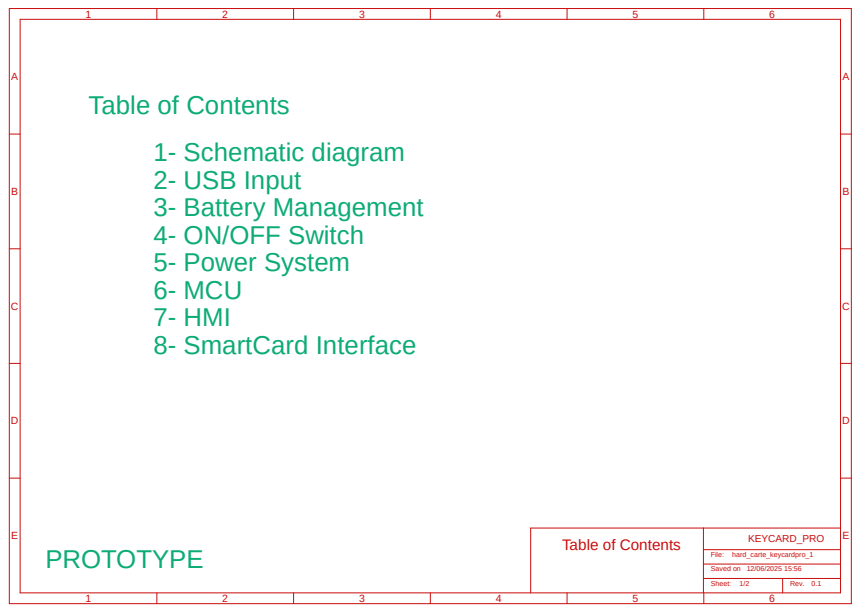
[picture p96: page 1]
Sheet:; Rev.; Saved on; File:; KEYCARD_PRO; hard_carte_keycardpro_1; PROTOTYPE

Table of Contents
1- Schematic diagram
2- USB Input
3- Battery Management
4- ON/OFF Switch
5- Power System
6- MCU
7- HMI
8- SmartCard Interface

A

A

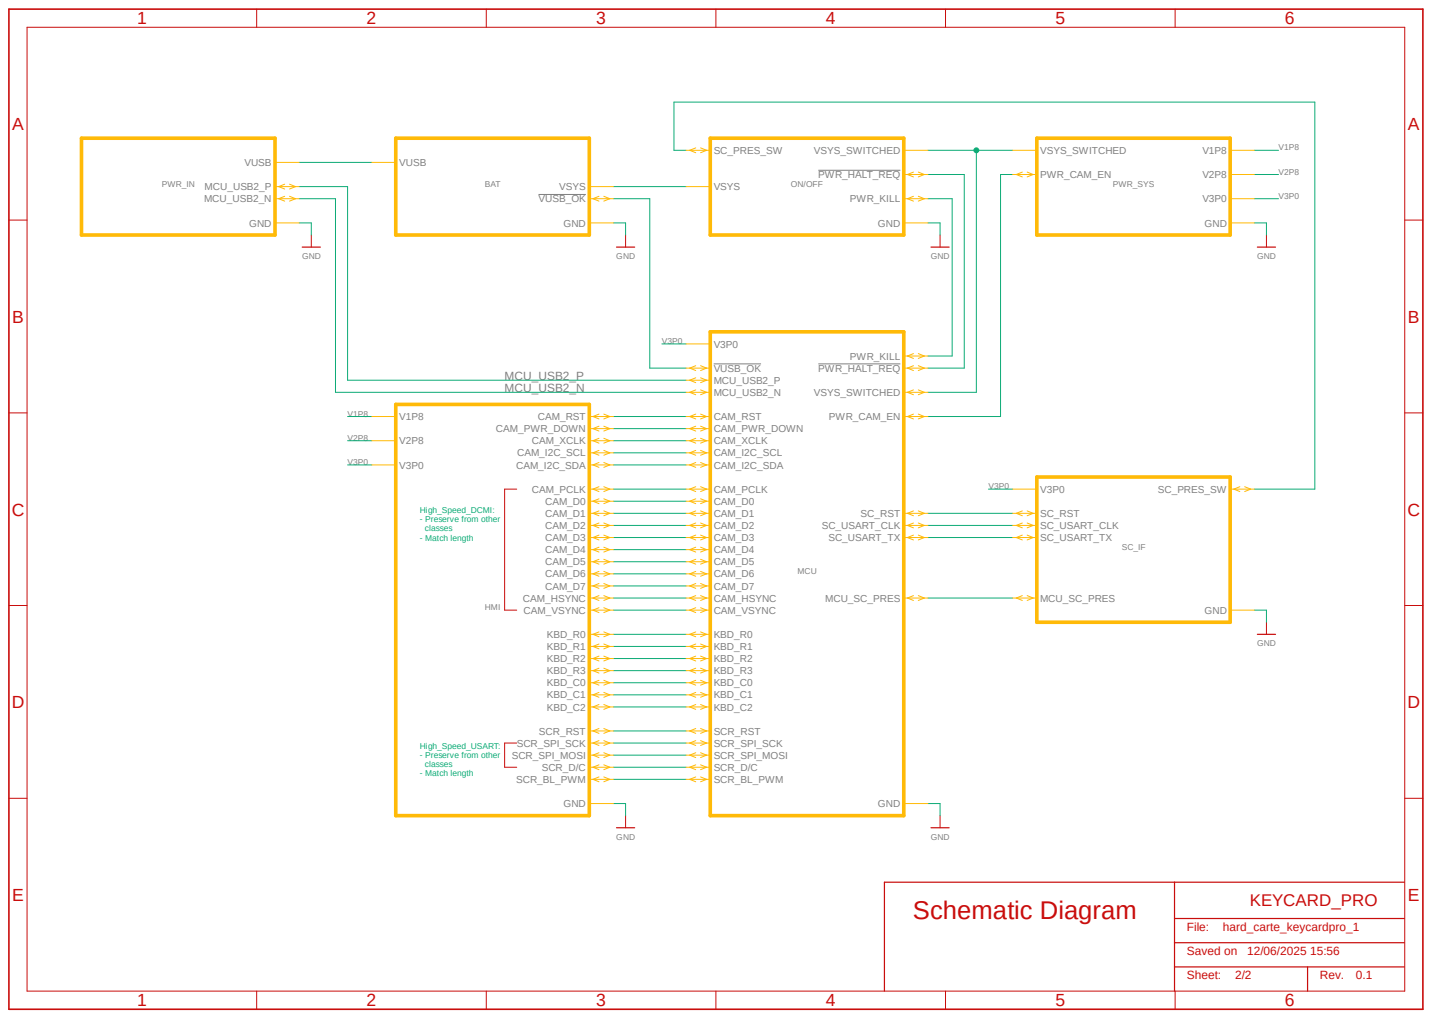
[picture p97: page 2]
GND; GND GND; V3P0 SC_RST; SC_USART_CLK SC_USART_TX; MCU_SC_PRES; SC_PRES_SW; PWR_IN; VUSB GND MCU_USB2_P; MCU_USB2_N; ON/OFF; VSYS; PWR_KILL; PWR_HALT_REQ; VSYS_SWITCHED; MCU; CAM_D0 CAM_D1 CAM_D2 CAM_D3 CAM_D4 CAM_D5 CAM_D6 CAM_D7 CAM_HSYNC CAM_VSYNC; CAM_PCLK; CAM_I2C_SDA; CAM_I2C_SCL; CAM_PWR_DOWN; CAM_RST; MCU_USB2_P MCU_USB2_N; PWR_KILL PWR_HALT_REQ; SC_RST SC_USART_CLK SC_USART_TX; KBD_R0 KBD_R1 KBD_R2 KBD_R3 KBD_C0 KBD_C1 KBD_C2; SCR_RST SCR_SPI_SCK SCR_SPI_MOSI SCR_D/C SCR_BL_PWM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

High_Speed_DCMI: - Preserve from other

High_Speed_USART: - Preserve from other

A

A

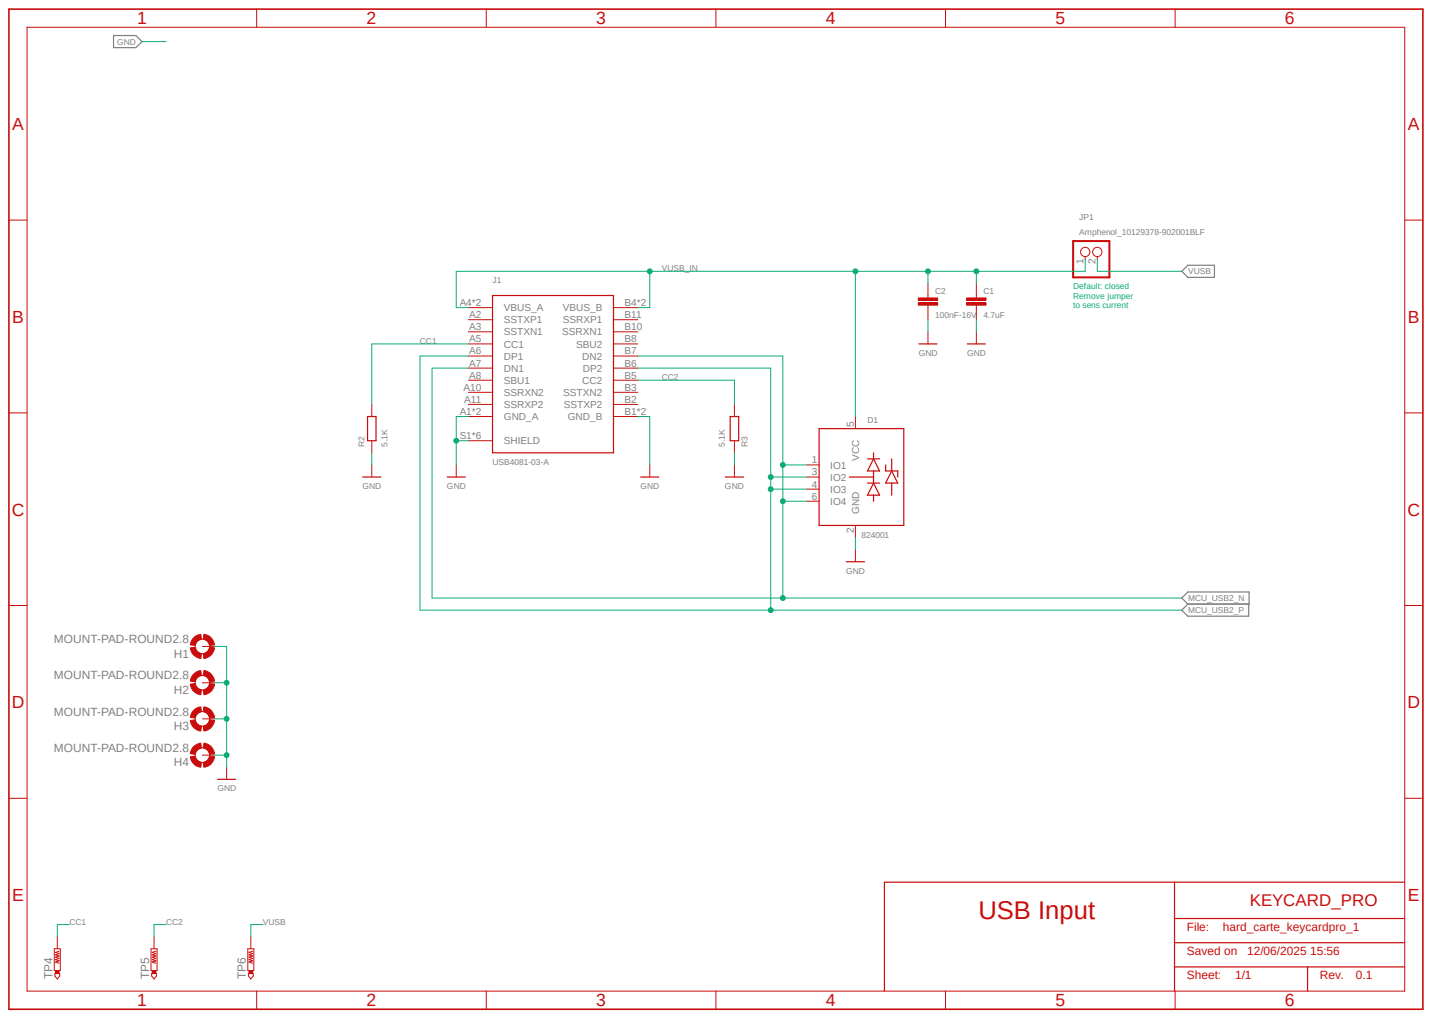
[picture p98: page 3]
4.7uF GND; GND GND; GND ⁵.1K GND; 5.1K GND; Amphenol_10129378-902001BLF USB4081-03-A; GND MOUNT-PAD-ROUND2.8; MOUNT-PAD-ROUND2.8; GND; JP1 GND_A A1*2; SSTXN1 A3; SSTXP1 A2; VBUS_A A4*2; SBU1 A8; SSRXN2 A10; SSRXP2 A11; SHIELD S1*6; GND_B; B1*2 SSTXN2; B3 SSTXP2; B2 VBUS_B; B5 SBU2; B7 SSRXN1; B10 SSRXP1; 2 VCC; 824001 TP⁴; TP⁵; TP⁶; MCU_USB2_P; MCU_USB2_N; VUSB; VUSB VUSB_IN; USB Input; Sheet:; Rev.; Saved on; File:; KEYCARD_PRO; hard_carte_keycardpro_1

Default: closed Remove jumper

to sens current

JP3 | C3 | C4

A

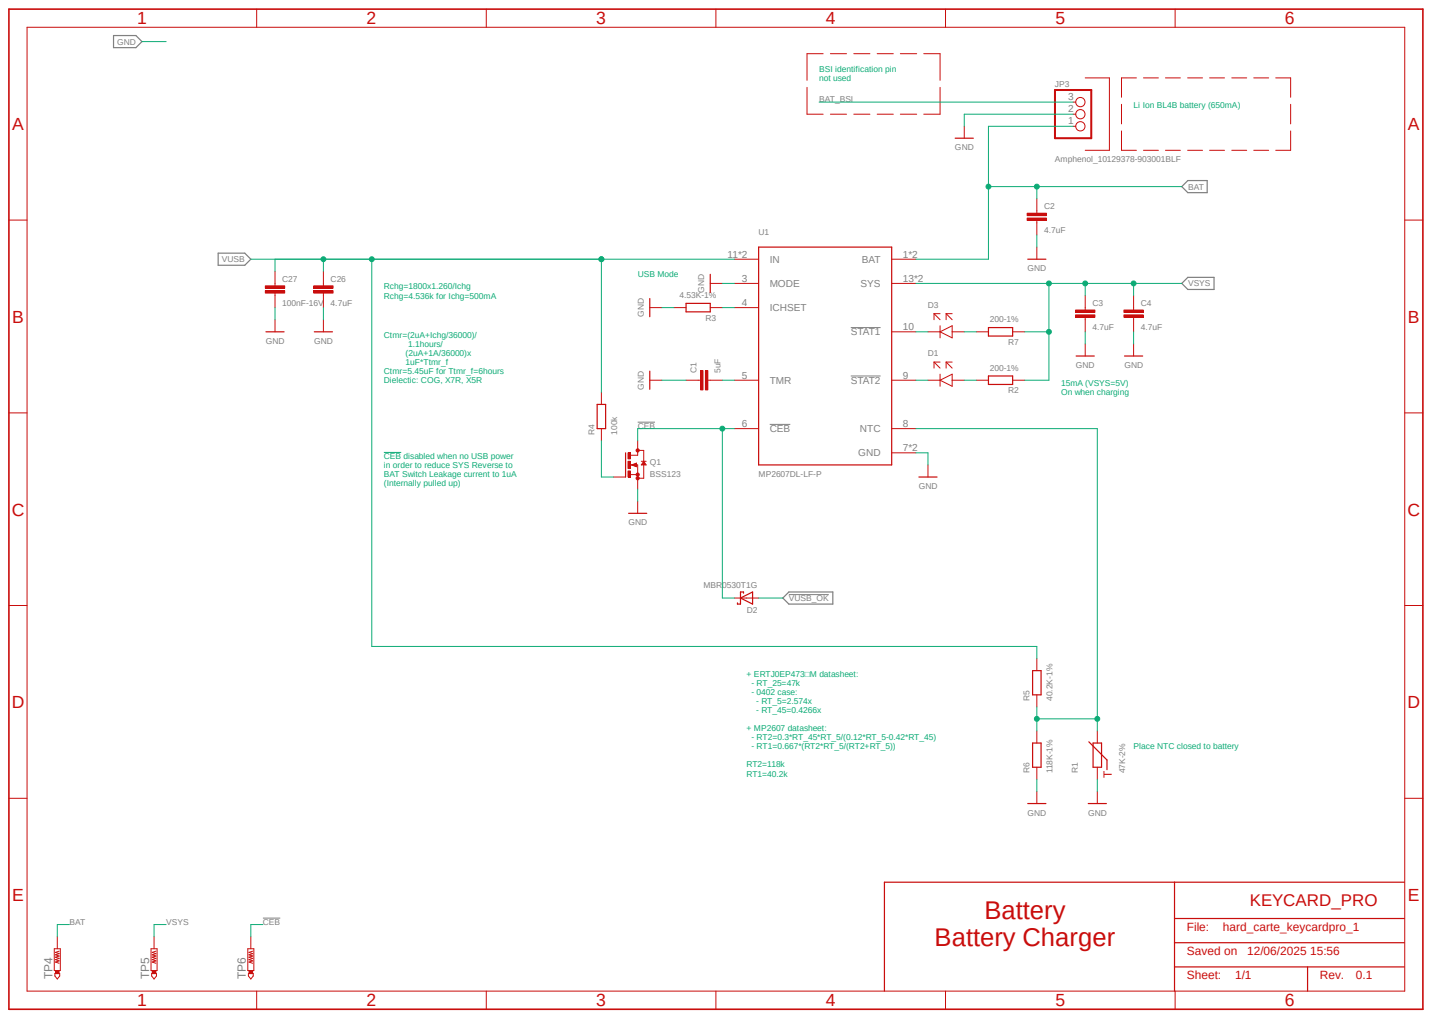
[picture p99: page 4]

GND GND

USB Mode Rchg=1800x1.260/Ichg

CEB disabled when no USB power
in order to reduce SYS Reverse to BAT Switch Leakage current to 1uA

A

A

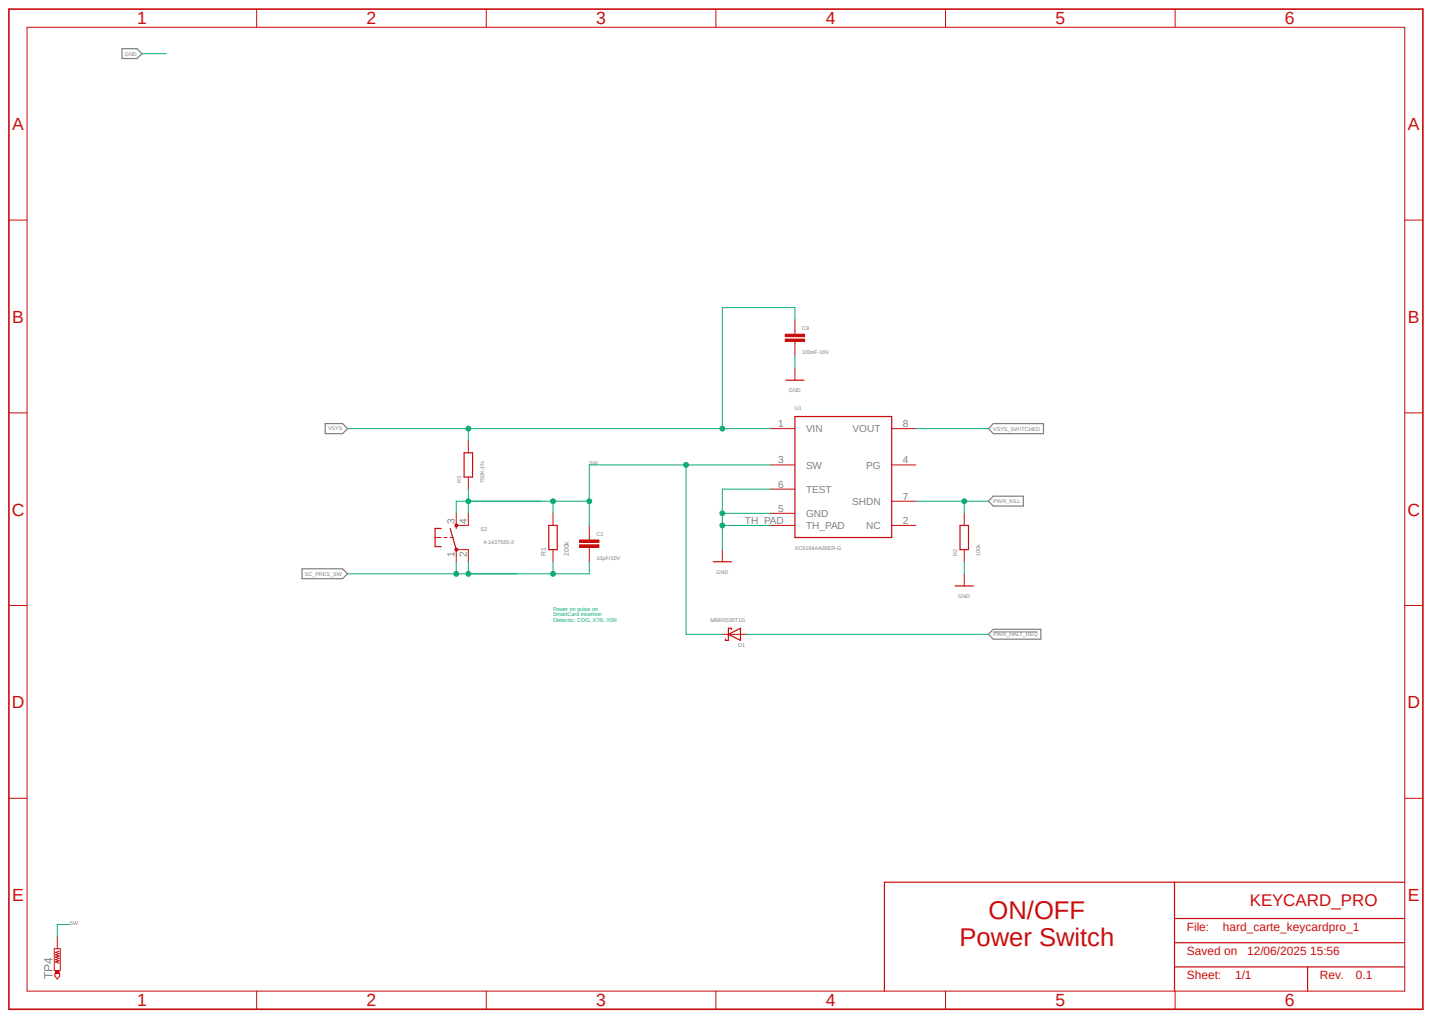
[picture p100: page 5]
GND; MBR0530T1G; VIN 1; VOUT; 4 SHDN; 7 TEST 6; GND 5; 2 TH_PAD TH_PAD; U1 TP⁴; VSYS; VSYS_SWITCHED; PWR_KILL; PWR_HALT_REQ; SC_PRES_SW; ON/OFF Power Switch; Sheet:; Rev.; Saved on; File:; KEYCARD_PRO; hard_carte_keycardpro_1

Power on pulse on
SmartCard insertion
Dielectic: COG, X7R, X5R

A

A

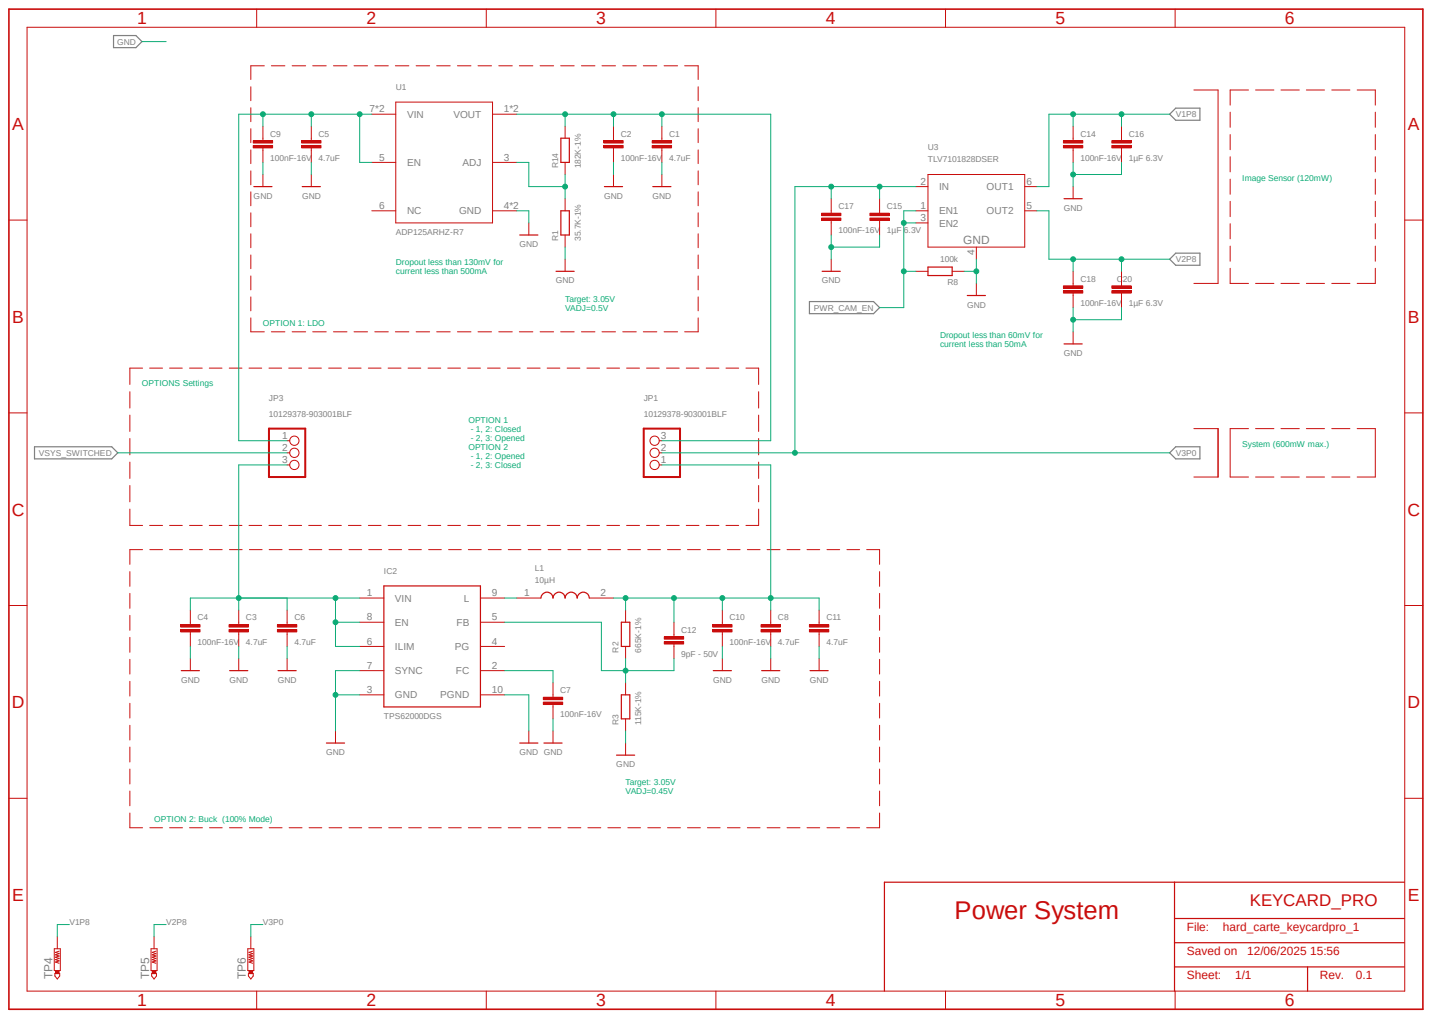
[picture p101: page 6]

Dropout less than 130mV for current less than 500mA OPTION 1

A

A

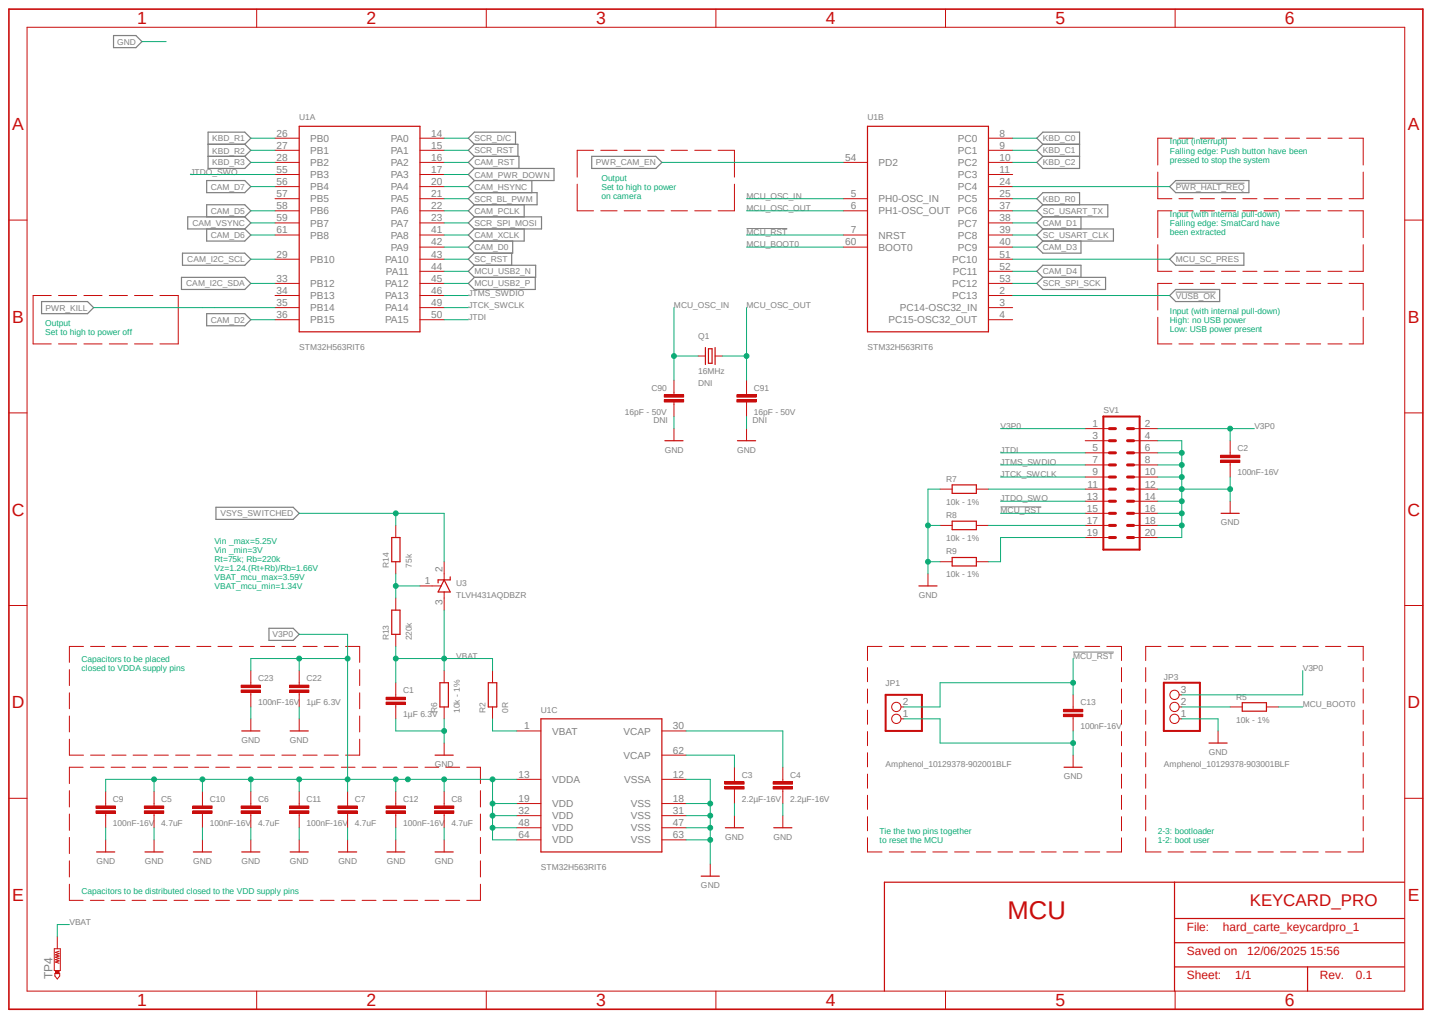
[picture p102: page 7]

Input (interrupt)
Falling edge: Push button have been
pressed to stop the system

PWR_CAM_EN
Output
Set to high to power on camera

Input (with internal pull-down)
Falling edge: SmatCard have
been extracted

VUSB_OK
High: no USB power
Low: USB power present

Set to high to power off

Vin _max=5.25V
Vin _min=3V Rt=75k; Rb=220k Vz=1.24.(Rt+Rb)/Rb=1.66V

VBAT
Capacitors to be placed
closed to VDDA supply pins

Tie the two pins together
to reset the MCU

Capacitors to be distributed closed to the VDD supply pins

A

A

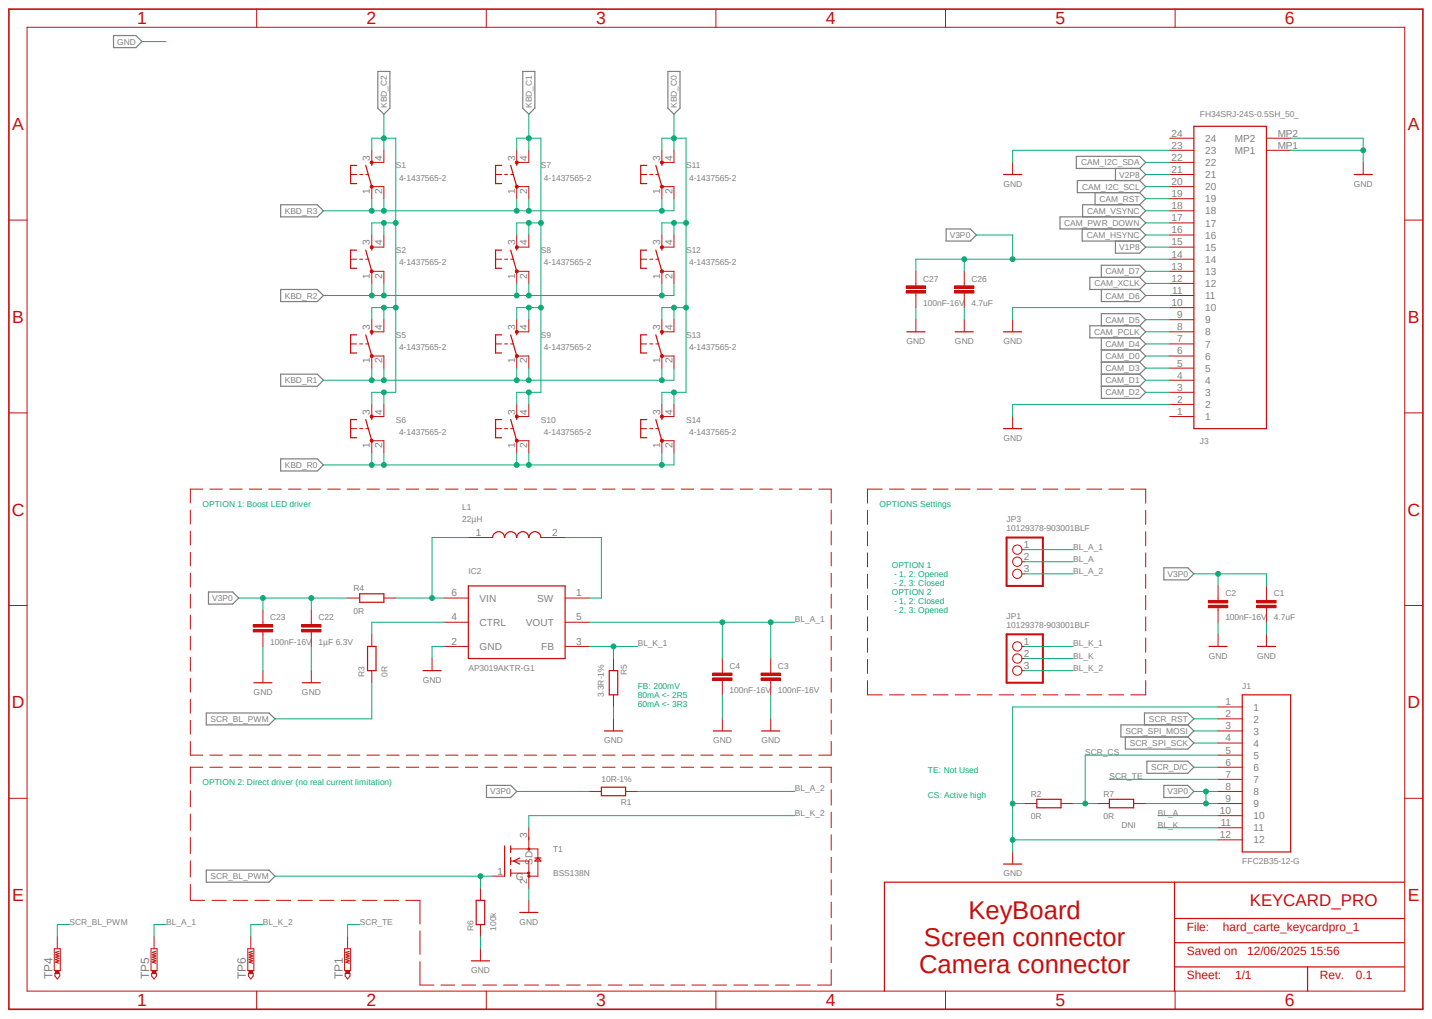
[picture p103: page 8]

60mA <- 3R3 OPTION 1: Boost LED driver OPTION 2: Direct driver (no real current limitation)

A

A

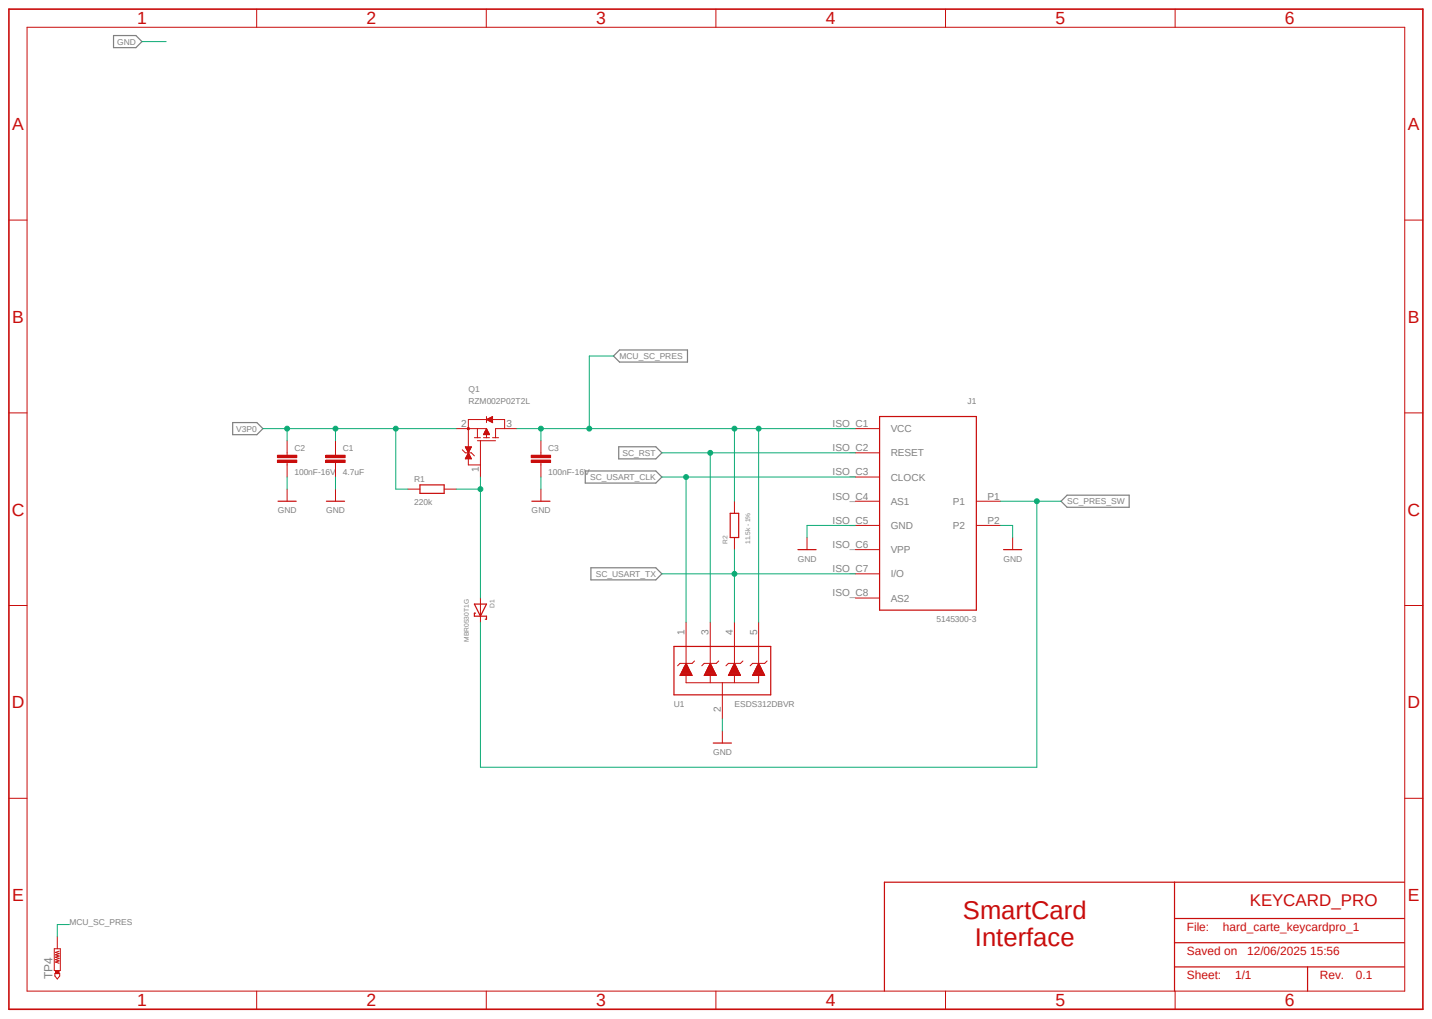
[picture p104: page 9]
