keycard-tech/keycard-shell/hardware/development_board/devboard_v1/GERBER/CAMOutputs/Assembly/plan_implantation.pdf

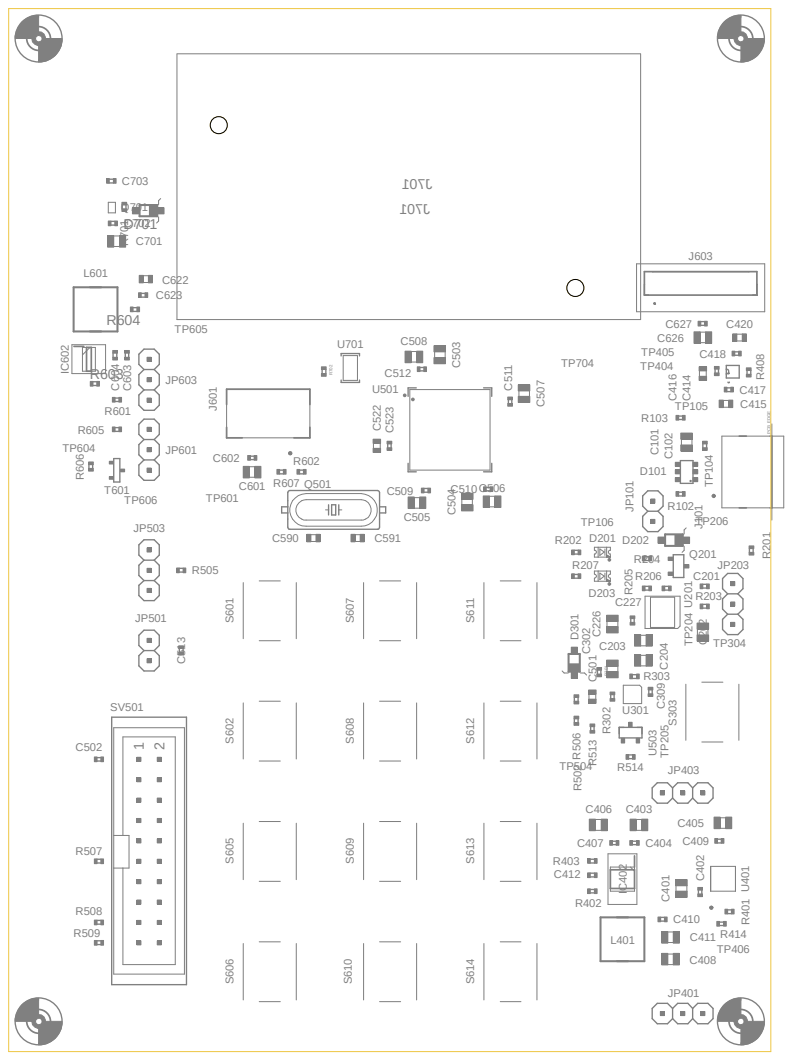
[picture p105: page 1]
