keycard-tech/keycard-shell/hardware/development_board/devboard_v1/GERBER/CAMOutputs/Assembly/plan_implantation_BOTTOM.pdf

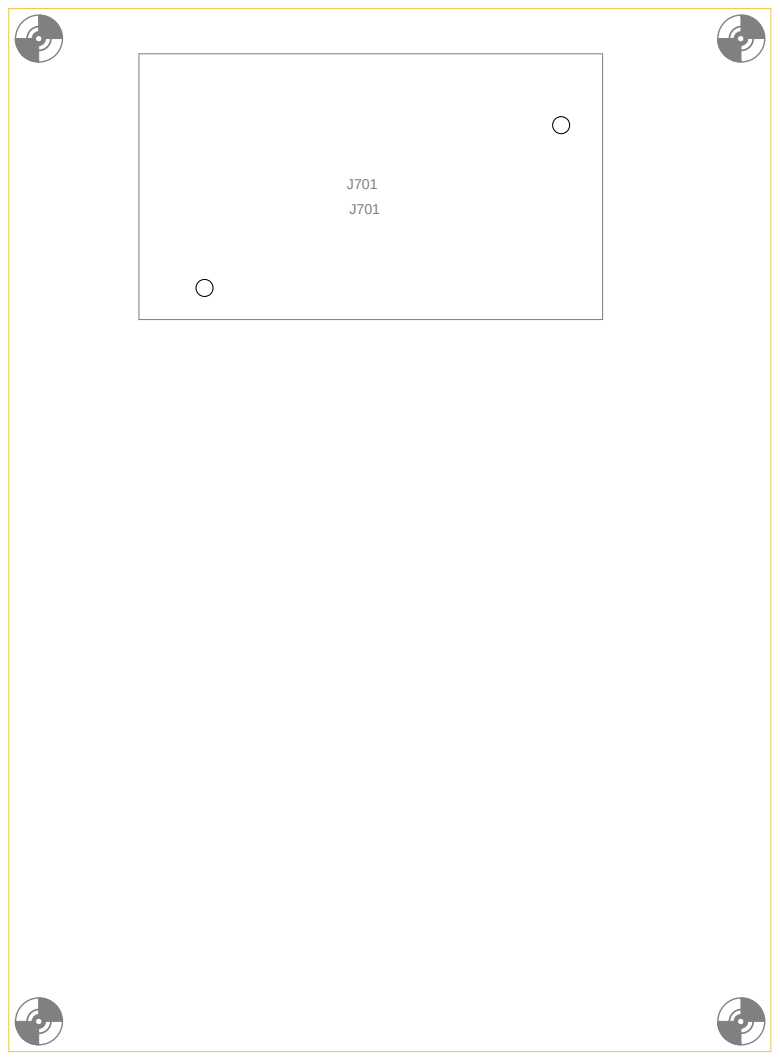
[picture p106: page 1]
