keycard-tech/keycard-shell/hardware/development_board/devboard_v1/GERBER/CAMOutputs/Assembly/plan_implantation_TOP.pdf

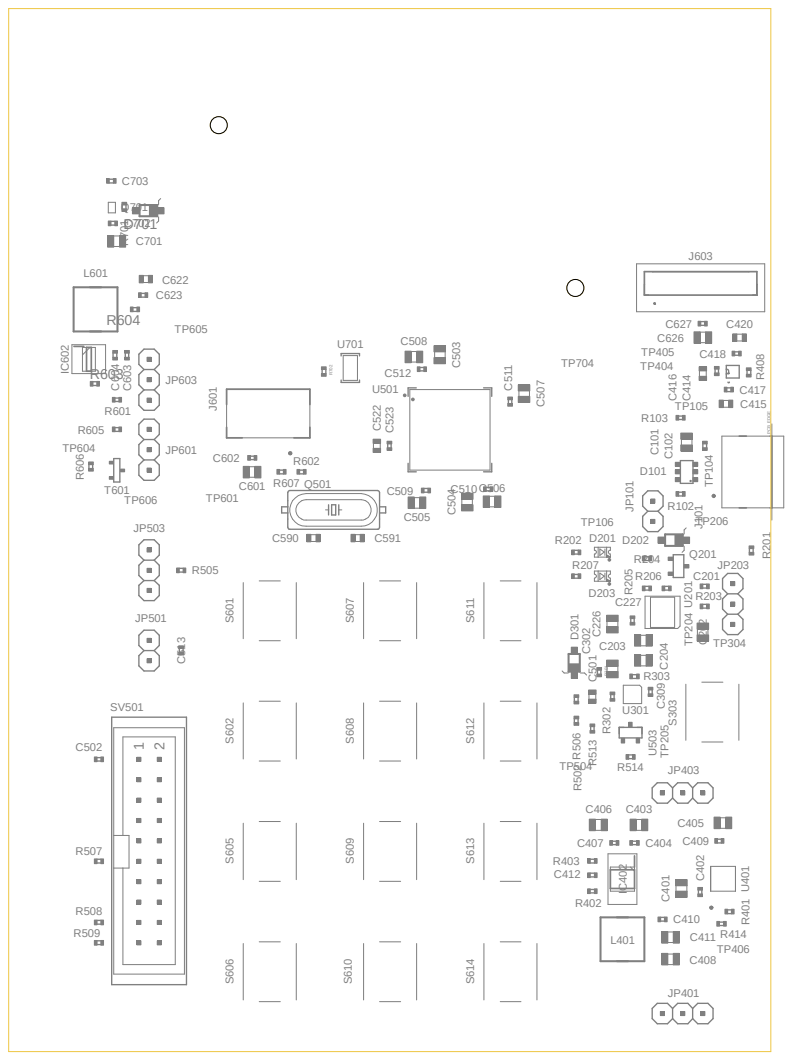
[picture p107: page 1]
