keycard-tech/keycard-shell/app/hal.h

#ifndef __HAL__
#define __HAL__

#include <stdint.h>
#include <stddef.h>
#include <stdbool.h>
#include "crypto/sha2_soft.h"
#include "crypto/aes.h"
#include "crypto/ecdsa.h"
#include "iso7816/smartcard.h"
#include "qrcode/qrcode.h"

#ifdef STM32_HAL
#include "stm32.h" // IWYU pragma: export
#else
#error "Unsupported platform"
#endif

// General
typedef enum {
	HAL_SUCCESS,
	HAL_FAIL,
} hal_err_t;

#define HAL_DEVICE_UID_LEN 16

typedef enum {
  BOOT_HOT,
  BOOT_COLD
} hal_boot_t;

hal_err_t hal_init();
hal_err_t hal_init_bootloader();
hal_err_t hal_teardown_bootloader();
hal_err_t hal_device_uid(uint8_t out[HAL_DEVICE_UID_LEN]);
void hal_reboot();
hal_boot_t hal_boot_type();
hal_err_t hal_check_hardened();

// Camera
#define CAMERA_WIDTH QUIRC_WIDTH
#define CAMERA_HEIGHT QUIRC_HEIGHT
#define CAMERA_BPP 1
#define CAMERA_FB_SIZE (CAMERA_WIDTH * CAMERA_HEIGHT * CAMERA_BPP)
#define CAMERA_FB_COUNT 2
#define CAMERA_TASK_NOTIFICATION_IDX 0

hal_err_t hal_camera_init();
hal_err_t hal_camera_start(uint8_t fb[CAMERA_FB_COUNT][CAMERA_FB_SIZE]);
hal_err_t hal_camera_stop();
hal_err_t hal_camera_next_frame(uint8_t** fb);
hal_err_t hal_camera_submit(uint8_t* fb);

// Screen
#define SCREEN_WIDTH 320
#define SCREEN_HEIGHT 240
#define LCD_MAX_BRIGHTNESS 100
#define LCD_MIN_BRIGHTNESS 5
#define LCD_BRIGHTNESS_STEP 5
#define SCREEN_TASK_NOTIFICATION_IDX 1
#define UI_NOTIFICATION_IDX 2
#define UI_CMD_EVT 1
#define UI_KEY_EVT 2
#define UI_USB_PLUG_EVT 4

// GPIO
typedef enum {
  GPIO_CAMERA_PWDN = 0,
  GPIO_CAMERA_PWR,
  GPIO_CAMERA_RST,
  GPIO_LCD_CMD_DATA,
  GPIO_LCD_RST,
  GPIO_KEYPAD_ROW_0,
  GPIO_KEYPAD_ROW_1,
  GPIO_KEYPAD_ROW_2,
  GPIO_KEYPAD_ROW_3,
  GPIO_KEYPAD_COL_0,
  GPIO_KEYPAD_COL_1,
  GPIO_KEYPAD_COL_2,
  GPIO_VUSB_OK,
  GPIO_SMARTCARD_PRESENT,
  GPIO_HALT_REQ,
  GPIO_PWR_KILL
} hal_gpio_pin_t;

typedef enum {
  GPIO_RESET = 0,
  GPIO_SET = 1,
} hal_gpio_state_t;

void hal_gpio_set(hal_gpio_pin_t pin, hal_gpio_state_t state);
hal_gpio_state_t hal_gpio_get(hal_gpio_pin_t pin);

// I2C
typedef enum {
  I2C_CAMERA,
} hal_i2c_port_t;

hal_err_t hal_i2c_send(hal_i2c_port_t port, uint8_t addr, const uint8_t* data, size_t len);

// SPI
typedef enum {
  SPI_LCD
} hal_spi_port_t;

hal_err_t hal_spi_send(hal_spi_port_t port, const uint8_t* data, size_t len);
hal_err_t hal_spi_send_dma(hal_spi_port_t port, const uint8_t* data, size_t len, void (*cb)());

// SmartCard
#define SMARTCARD_TASK_NOTIFICATION_IDX 1
hal_err_t hal_smartcard_start();
hal_err_t hal_smartcard_stop();
hal_err_t hal_smartcard_pps(smartcard_protocol_t protocol, uint32_t baud, uint32_t freq, uint8_t guard, uint32_t timeout);
hal_err_t hal_smartcard_set_timeout(uint32_t timeout);
hal_err_t hal_smartcard_set_blocklen(uint32_t len);
hal_err_t hal_smartcard_send(const uint8_t* data, size_t len);
hal_err_t hal_smarcard_recv(uint8_t* data, size_t len);
void hal_smartcard_abort();

// Crypto (only use in crypto library)
typedef enum {
  AES_CBC,
} hal_aes_chaining_t;

typedef enum {
  AES_ENCRYPT,
  AES_DECRYPT
} hal_aes_mode_t;

hal_err_t hal_rng_next(uint8_t *buf, size_t len);
hal_err_t hal_derive_device_unique_secret(const uint8_t salt[32], uint8_t out[32]);

#ifndef SOFT_SHA256
hal_err_t hal_sha256_init(hal_sha256_ctx_t* ctx);
hal_err_t hal_sha256_update(hal_sha256_ctx_t* ctx, const uint8_t* data, size_t len);
hal_err_t hal_sha256_finish(hal_sha256_ctx_t* ctx, uint8_t out[SHA256_DIGEST_LENGTH]);
#endif

#ifndef SOFT_CRC32
hal_err_t hal_crc32_init(hal_crc32_ctx_t* ctx);
hal_err_t hal_crc32_update(hal_crc32_ctx_t* ctx, uint8_t data);
hal_err_t hal_crc32_finish(hal_crc32_ctx_t* ctx, uint32_t *out);
#endif

#ifndef SOFT_AES
hal_err_t hal_aes256_init(hal_aes_mode_t mode, hal_aes_chaining_t chaining, const uint8_t key[AES_256_KEY_SIZE], const uint8_t iv[AES_IV_SIZE]);
hal_err_t hal_aes256_block_process(const uint8_t in[AES_BLOCK_SIZE], uint8_t out[AES_BLOCK_SIZE]);
hal_err_t hal_aes256_finalize();

hal_err_t hal_aes128_ccm_init(hal_aes_mode_t mode, const uint8_t key[AES_128_KEY_SIZE], const uint8_t b0[AES_BLOCK_SIZE]);
hal_err_t hal_aes128_ccm_block_process(const uint8_t in[AES_BLOCK_SIZE], uint8_t out[AES_BLOCK_SIZE]);
hal_err_t hal_aes128_ccm_block_process_last(hal_aes_mode_t mode, const uint8_t in[AES_BLOCK_SIZE], uint8_t out[AES_BLOCK_SIZE], size_t len);
hal_err_t hal_aes128_ccm_finish(uint8_t tag[CCM_TAG_SIZE]);
#endif

#ifndef SOFT_ECDSA
hal_err_t hal_ecdsa_sign(const ecdsa_curve* curve, const uint8_t* priv_key, const uint8_t* digest, const uint8_t* k, uint8_t* sig_out);
hal_err_t hal_ecdsa_verify(const ecdsa_curve* curve, const uint8_t* pub_key, const uint8_t* sig, const uint8_t* digest);
hal_err_t hal_ec_point_multiply(const ecdsa_curve* curve, const uint8_t* scalar, const uint8_t* point, uint8_t* point_out);
hal_err_t hal_ec_double_ladder(const ecdsa_curve* curve, const uint8_t* s1, const uint8_t* p1, const uint8_t* s2, const uint8_t* p2, uint8_t* point_out);
hal_err_t hal_ec_point_check(const ecdsa_curve* curve, const uint8_t* point);
#endif

// Math
#define BN_SIZE 32
#ifndef SOFT_BN
hal_err_t hal_bn_mul_r2(const uint8_t a[BN_SIZE], const uint8_t mod[BN_SIZE], uint8_t r[BN_SIZE]);
hal_err_t hal_bn_mul_mont(const uint8_t a[BN_SIZE], const uint8_t b[BN_SIZE], const uint8_t mod[BN_SIZE], uint8_t r[BN_SIZE]);
hal_err_t hal_bn_mul_mod(const uint8_t a[BN_SIZE], const uint8_t b[BN_SIZE], const uint8_t mod[BN_SIZE], uint8_t r[BN_SIZE]);
hal_err_t hal_bn_add_mod(const uint8_t a[BN_SIZE], const uint8_t b[BN_SIZE], const uint8_t mod[BN_SIZE], uint8_t r[BN_SIZE]);
hal_err_t hal_bn_sub_mod(const uint8_t a[BN_SIZE], const uint8_t b[BN_SIZE], const uint8_t mod[BN_SIZE], uint8_t r[BN_SIZE]);
hal_err_t hal_bn_exp_mod(const uint8_t a[BN_SIZE], const uint8_t e[BN_SIZE], const uint8_t mod[BN_SIZE], uint8_t r[BN_SIZE]);
hal_err_t hal_bn_inv_mod(const uint8_t a[BN_SIZE], const uint8_t mod[BN_SIZE], uint8_t r[BN_SIZE]);
hal_err_t hal_bn_mul(const uint8_t a[BN_SIZE], const uint8_t b[BN_SIZE], uint8_t r[BN_SIZE]);
hal_err_t hal_bn_add(const uint8_t a[BN_SIZE], const uint8_t b[BN_SIZE], uint8_t r[BN_SIZE]);
hal_err_t hal_bn_sub(const uint8_t a[BN_SIZE], const uint8_t b[BN_SIZE], uint8_t r[BN_SIZE]);
int hal_bn_cmp(const uint8_t a[BN_SIZE], const uint8_t b[BN_SIZE]);
#endif

// Timer
hal_err_t hal_delay_us(uint32_t usec);
void hal_tick();

// Flash
#define HAL_FLASH_BLOCK_ADDR(__BLOCK__) (HAL_FLASH_ADDR + (HAL_FLASH_BLOCK_SIZE * __BLOCK__))
#define HAL_FLASH_ADDR_TO_BLOCK(__ADDR__) ((__ADDR__ - HAL_FLASH_ADDR) / HAL_FLASH_BLOCK_SIZE)

typedef struct {
  uint32_t addr;
  uint32_t count;
} hal_flash_data_segment_t;

hal_err_t hal_flash_begin_program();
hal_err_t hal_flash_program(const uint8_t* data, uint8_t* addr, size_t len);
hal_err_t hal_flash_erase(uint32_t block);
hal_err_t hal_flash_end_program();
bool hal_flash_busy();
const hal_flash_data_segment_t* hal_flash_get_data_segments();
void hal_flash_switch_firmware();

// PWM
typedef enum {
  PWM_BACKLIGHT,
} hal_pwm_output_t;

hal_err_t hal_pwm_set_dutycycle(hal_pwm_output_t out, uint8_t cycle);

// USB
#define HAL_USB_EPOUT_ADDR 0x01
#define HAL_USB_EPIN_ADDR 0x81
#define HAL_USB_MPS 64

hal_err_t hal_usb_start();
hal_err_t hal_usb_stop();
hal_err_t hal_usb_set_address(uint8_t addr);
hal_err_t hal_usb_send(uint8_t epaddr, const uint8_t* data, size_t len);
hal_err_t hal_usb_next_recv(uint8_t epaddr, uint8_t* data, size_t len);
hal_err_t hal_usb_set_stall(uint8_t epaddr, uint8_t stall);
uint8_t hal_usb_get_stall(uint8_t epaddr);
void hal_usb_setup_cb(uint8_t* data);
void hal_usb_data_in_cb(uint8_t epaddr);
void hal_usb_data_out_cb(uint8_t epaddr);

// Inactivity timer
void hal_inactivity_timer_set(uint32_t delay_ms);
void hal_inactivity_timer_reset();

// ADC
typedef enum {
  ADC_VBAT,
} hal_adc_channel_t;

hal_err_t hal_adc_read(hal_adc_channel_t ch, uint32_t* val);

#endif
