keycard-tech/keycard-shell/app/tasks/core_task.c

#include "common.h"
#include "core/core.h"
#include "core/core_multisig.h"
#include "core/card.h"
#include "core/settings.h"
#include "keycard/keycard.h"
#include "pwr.h"
#include "usb/usb.h"
#include "crypto/util.h"

static inline void core_action_run(i18n_str_id_t menu) {
  switch(menu) {
  // Top Level
  case MENU_QRCODE:
    core_qr_run();
    break;
  case MENU_CONNECT:
    core_connect_wallet();
    break;
  case MENU_HELP:
    device_help();
    break;
  // Addresses
  case MENU_ETHEREUM:
    core_addresses_ethereum();
    break;
  case MENU_BITCOIN:
    core_addresses_bitcoin();
    break;
  case MENU_ADDRESS_VERIFY:
    core_addresses_verify();
    break;
  case MENU_MULTISIG_IMPORT:
    core_multisig_import();
    break;
  case MENU_MULTISIG_BROWSE:
    core_multisig_browse();
    break;
  case MENU_MULTISIG_EXPORT:
    core_multisig_export();
    break;
  case MENU_MULTISIG_VERIFY:
    core_multisig_verify();
    break;
  case MENU_MULTISIG_DELETE:
    core_multisig_delete();
    break;
  // Keycard
  case MENU_CARD_NAME:
    card_change_name();
    break;
  case MENU_CHANGE_PIN:
    card_change_pin();
    break;
  case MENU_CHANGE_PUK:
    card_change_puk();
    break;
  case MENU_CHANGE_PAIRING:
    card_change_pairing();
    break;
  case MENU_RESET_CARD:
    card_reset();
    break;
  case MENU_VERIFY_MNEMO:
    card_verify_mnemonic();
    break;
  // Device
  case MENU_DEV_AUTH:
    device_auth_run();
    break;
  case MENU_UPDATE:
    device_update_sw();
    break;
  case MENU_BRIGHTNESS:
    settings_lcd_brightness();
    break;
  case MENU_SET_OFF_TIME:
    settings_set_off_time();
    break;
  case MENU_USB:
    settings_usb_onoff();
    break;
  case MENU_INSTRUCTIONS:
    settings_help_onoff();
    break;
  // Info
  case MENU_SW_INFO:
    device_info();
    break;
  case MENU_ELABEL:
    device_elabel();
    break;
  default:
    //unknown commands
    break;
  }
}

static inline void core_print_fingerprint(char fingerprint[(sizeof(uint32_t) * 2) + 1]) {
  uint32_t mfp;
  core_get_fingerprint(g_core.bip44_path, 0, &mfp);
  mfp = rev32(mfp);
  base16_encode((uint8_t*) &mfp, fingerprint, sizeof(uint32_t));
}

void core_task_entry(void* pvParameters) {
  if (hal_gpio_get(GPIO_SMARTCARD_PRESENT) == GPIO_RESET) {
    pwr_shutdown();
  }

  keycard_init(&g_core.keycard);
  keycard_activate(&g_core.keycard);

  if (g_core.keycard.sc.state != SC_READY) {
    pwr_reboot();
  }

  g_core.ready = true;

  usb_start_if_connected();

  i18n_str_id_t selected = MENU_QRCODE;

  char fingerprint[(sizeof(uint32_t) * 2) + 1];
  core_print_fingerprint(fingerprint);

  while(1) {
    switch(ui_menu((g_core.keycard.name[0] ? g_core.keycard.name : fingerprint), &menu_mainmenu, &selected, -1, 1, UI_MENU_NOCANCEL, 0, 0)) {
    case CORE_EVT_USB_CMD:
      core_usb_run();
      break;
    case CORE_EVT_UI_OK:
      core_action_run(selected);
      break;
    case CORE_EVT_UI_CANCELLED:
    default:
      selected = MENU_QRCODE;
      break;
    }
  }
}
