keycard-tech/keycard-shell/app/core/auth.c

#include "core.h"
#include "crypto/ecdsa.h"
#include "crypto/sha2.h"
#include "crypto/secp256k1.h"
#include "crypto/rand.h"
#include "crypto/memzero.h"
#include "hal.h"
#include "settings.h"
#include "storage/keys.h"
#include "ui/ui.h"
#include "ur/ur.h"
#include "ur/ur_encode.h"

#define AUTH_CHALLENGE_LEN 32
#define AUTH_SIG_LEN 64

void device_auth_run() {
  // Inform the user
  if (!g_settings.skip_help && (ui_prompt(LSTR(DEV_AUTH_TITLE), LSTR(DEV_AUTH_PROMPT_STEP1), UI_INFO_CANCELLABLE) != CORE_EVT_UI_OK)) {
    return;
  }

  struct dev_auth auth;

  // Challenge QR
  if (ui_qrscan(DEV_AUTH, &auth) != CORE_EVT_UI_OK) {
    return;
  }

  if ((auth.dev_auth_step.dev_auth_step_type_choice != dev_auth_step_type_dev_auth_init_m_c) ||
      !auth.dev_auth_challenge_present ||
      auth.dev_auth_dev_id_present ||
      auth.dev_auth_first_auth_present ||
      auth.dev_auth_auth_time_present ||
      auth.dev_auth_auth_count_present ||
      auth.dev_auth_auth_sig_present) {
    ui_info(ICON_INFO_ERROR, LSTR(DEV_AUTH_INVALID_QR), LSTR(DEV_AUTH_INVALID_CHALLENGE_SUB), 0);
    return;
  }

  SHA256_CTX sha256;

  uint8_t uid[HAL_DEVICE_UID_LEN];
  uint8_t digest[SHA256_DIGEST_LENGTH];
  uint8_t auth_key[ECC256_ELEMENT_SIZE];

  hal_device_uid(uid);

  sha256_Init(&sha256);
  sha256_Update(&sha256, uid, HAL_DEVICE_UID_LEN);
  sha256_Update(&sha256, auth.dev_auth_challenge.dev_auth_challenge.value, auth.dev_auth_challenge.dev_auth_challenge.len);
  sha256_Final(&sha256, digest);

  key_read_private(DEV_AUTH_PRIV_KEY, auth_key);
  ecdsa_sign(&secp256k1, auth_key, digest, g_core.data.sig.plain_sig);
  memzero(auth_key, ECC256_ELEMENT_SIZE);

  // Step 2
  if (!g_settings.skip_help && (ui_prompt(LSTR(DEV_AUTH_TITLE), LSTR(DEV_AUTH_PROMPT_STEP2), UI_INFO_CANCELLABLE) != CORE_EVT_UI_OK)) {
    return;
  }  

  // Response
  random_buffer((uint8_t*) auth.dev_auth_challenge.dev_auth_challenge.value, AUTH_CHALLENGE_LEN);

  auth.dev_auth_dev_id_present = 1;
  auth.dev_auth_dev_id.dev_auth_dev_id.value = uid;
  auth.dev_auth_dev_id.dev_auth_dev_id.len = HAL_DEVICE_UID_LEN;

  auth.dev_auth_step.dev_auth_step_type_choice = dev_auth_step_type_dev_auth_device_m_c;
  auth.dev_auth_auth_sig_present = 1;
  auth.dev_auth_auth_sig.dev_auth_auth_sig.value = g_core.data.sig.plain_sig;
  auth.dev_auth_auth_sig.dev_auth_auth_sig.len = AUTH_SIG_LEN;

  cbor_encode_dev_auth(g_core.data.sig.cbor_sig, CBOR_SIG_MAX_LEN, &auth, &g_core.data.sig.cbor_len);

  if (ui_display_ur_qr(NULL, g_core.data.sig.cbor_sig, g_core.data.sig.cbor_len, DEV_AUTH) != CORE_EVT_UI_OK) {
    return;
  }

  sha256_Init(&sha256);
  sha256_Update(&sha256, uid, HAL_DEVICE_UID_LEN);
  sha256_Update(&sha256, auth.dev_auth_challenge.dev_auth_challenge.value, auth.dev_auth_challenge.dev_auth_challenge.len);

  // Step 3
  if (!g_settings.skip_help && (ui_prompt(LSTR(DEV_AUTH_TITLE), LSTR(DEV_AUTH_PROMPT_STEP3), UI_INFO_CANCELLABLE) != CORE_EVT_UI_OK)) {
    return;
  }

  // Final QR
  if (ui_qrscan(DEV_AUTH, &auth) != CORE_EVT_UI_OK) {
    return;
  }

  if ((auth.dev_auth_step.dev_auth_step_type_choice != dev_auth_step_type_dev_auth_server_m_c) ||
      auth.dev_auth_challenge_present ||
      auth.dev_auth_dev_id_present ||
      !auth.dev_auth_first_auth_present ||
      !auth.dev_auth_auth_time_present ||
      !auth.dev_auth_auth_count_present ||
      !auth.dev_auth_auth_sig_present
      ) {
    ui_info(ICON_INFO_ERROR, LSTR(DEV_AUTH_INVALID_QR), LSTR(DEV_AUTH_INVALID_CHALLENGE_SUB), 0);
    return;
  }

  sha256_Update(&sha256, (uint8_t*) &auth.dev_auth_first_auth.dev_auth_first_auth, 4);
  sha256_Update(&sha256, (uint8_t*) &auth.dev_auth_auth_time.dev_auth_auth_time, 4);
  sha256_Update(&sha256, (uint8_t*) &auth.dev_auth_auth_count.dev_auth_auth_count, 4);
  sha256_Final(&sha256, digest);

  const uint8_t* key;
  key_read_public(DEV_AUTH_SERVER_KEY, &key);
  if (!ecdsa_verify(&secp256k1, key, auth.dev_auth_auth_sig.dev_auth_auth_sig.value, digest)) {
    ui_device_auth(auth.dev_auth_first_auth.dev_auth_first_auth, auth.dev_auth_auth_time.dev_auth_auth_time, auth.dev_auth_auth_count.dev_auth_auth_count);
  } else {
    ui_info(ICON_INFO_ERROR, LSTR(DEV_AUTH_INVALID_SITE_MSG), LSTR(DEV_AUTH_INVALID_SITE_SUB), 0);
  }
}
