keycard-tech/keycard-shell/app/crypto/shamir.h

/*
 * Low level API for Daan Sprenkels' Shamir secret sharing library
 * Copyright (c) 2017 Daan Sprenkels <hello@dsprenkels.com>
 * Copyright (c) 2019 SatoshiLabs
 *
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
 * Usage of this API is hazardous and is only reserved for beings with a
 * good understanding of the Shamir secret sharing scheme and who know how
 * crypto code is implemented. If you are unsure about this, use the
 * intermediate level API. You have been warned!
 */

#ifndef __SHAMIR_H__
#define __SHAMIR_H__

#include <stdbool.h>
#include <stddef.h>
#include <stdint.h>

#define SHAMIR_MAX_SHARE_COUNT 16
#define SHAMIR_MIN_SECRET_SIZE 16
#define SHAMIR_MAX_SECRET_SIZE 32

#define SHAMIR_ERROR_SECRET_TOO_LONG       (-101)
#define SHAMIR_ERROR_TOO_MANY_SHARES       (-102)
#define SHAMIR_ERROR_INTERPOLATION_FAILURE (-103)
#define SHAMIR_ERROR_CHECKSUM_FAILURE      (-104)
#define SHAMIR_ERROR_SECRET_TOO_SHORT      (-105)
#define SHAMIR_ERROR_SECRET_NOT_EVEN_LEN   (-106)
#define SHAMIR_ERROR_INVALID_THRESHOLD     (-107)

/*
 * Computes f(x) given the Shamir shares (x_1, f(x_1)), ... , (x_m, f(x_m)).
 * The x coordinates of the shares must be pairwise distinct. Returns true on
 * success, otherwise false.
 * result: Array of length len where the evaluations of the polynomials in x
 *     will be written.
 * result_index: The x coordinate of the result.
 * share_indices: Points to the array of integers x_1, ... , x_m.
 * share_values: Points to the array of y_1, ... , y_m, where each y_i is an
 *     array of bytes of length len representing the evaluations of the
 *     polynomials in x_i.
 * share_count: The number of shares m.
 * len: The length of the result array and of each of the y_1, ... , y_m arrays.
 *
 * The number of shares used to compute the result may be larger than the
 * required threshold.
 *
 * This function does *not* do *any* checking for integrity. If any of the
 * shares are not original, this will result in an invalid restored value.
 * All values written to `result` should be treated as secret. Even if some of
 * the shares that were provided as input were incorrect, the result *still*
 * allows an attacker to gain information about the correct result.
 *
 * This function treats `shares_values`, `share_indices` and `result` as secret
 * values. `share_count` is treated as a public value (for performance reasons).
 */
bool shamir_interpolate(uint8_t *result, uint8_t result_index,
                        const uint8_t *share_indices,
                        const uint8_t **share_values, uint8_t share_count,
                        size_t len);

uint8_t* shamir_create_digest(const uint8_t *random_data, uint32_t rdlen, const uint8_t *shared_secret, uint32_t sslen, uint8_t *result);
int32_t shamir_split_secret(uint8_t threshold, uint8_t share_count, const uint8_t *secret, uint32_t secret_length, uint8_t *result);
int32_t shamir_recover_secret(uint8_t threshold, const uint8_t *x, const uint8_t **shares, uint32_t share_length, uint8_t *secret);

#endif /* __SHAMIR_H__ */
