keycard-tech/keycard-shell/app/core/core_multisig.h

#ifndef __CORE_MULTISIG_H
#define __CORE_MULTISIG_H

void core_multisig_import();
void core_multisig_browse();
void core_multisig_export();
void core_multisig_verify();
void core_multisig_delete();

#endif
