keycard-tech/keycard-shell/app/pwr.h

#ifndef __PWR__
#define __PWR__

#include <stdbool.h>
#include <stdint.h>

#define PWR_BATTERY_CHARGING 255

void pwr_reboot();
void pwr_shutdown();

void pwr_usb_plugged(bool from_isr);
void pwr_usb_unplugged(bool from_isr);

void pwr_smartcard_inserted();
void pwr_smartcard_removed();

void pwr_inactivity_timer_elapsed();

uint8_t pwr_battery_level();

#endif
