keycard-tech/keycard-shell/app/core/card.h

#ifndef __CARD_SETTINGS__
#define __CARD_SETTINGS__

void card_change_name();
void card_change_pin();
void card_change_puk();
void card_change_pairing();
void card_reset();
void card_verify_mnemonic();

#endif
