keycard-tech/keycard-shell/app/storage/keys.c

#include "keys.h"
#include "hal.h"

const uint8_t __attribute__((section(".derivation_salt"))) _DEV_AUTH_SALT[] = {
  0xed, 0x98, 0x37, 0x52, 0x64, 0x24, 0x04, 0xdf, 0xa1, 0xe1, 0xc2, 0x4e, 0x7f, 0x76, 0x6f, 0x6f, 
  0xf3, 0xb9, 0xc8, 0x69, 0x3b, 0xd4, 0xc6, 0xd3, 0xd3, 0xa5, 0x31, 0x57, 0xdf, 0x3f, 0x4f, 0x47, 
};

const uint8_t __attribute__((section(".derivation_salt"))) _PAIRING_ENC_SALT[] = {
  0x41, 0x6d, 0x6f, 0xc3, 0xca, 0xaf, 0x78, 0xf7, 0x31, 0x16, 0xd1, 0xc2, 0x6a, 0x02, 0xdf, 0xaa,
  0x20, 0x4a, 0x32, 0x76, 0xdf, 0x39, 0x43, 0x03, 0x2b, 0x5b, 0xe2, 0xc1, 0x8d, 0xf4, 0x44, 0xd6,
};

const uint8_t __attribute__((section(".dev_auth_server_key"))) _DEV_AUTH_SERVER[] = {
  0x03, 
  0xa3, 0x0f, 0x53, 0x8a, 0x97, 0x70, 0xea, 0x43, 0xbf, 0x73, 0xa6, 0xe9, 0x99, 0x81, 0x15, 0x99,
  0xd2, 0xc2, 0x31, 0xe9, 0x5a, 0xe3, 0xf1, 0x87, 0x79, 0x6d, 0xf3, 0x18, 0xf4, 0x46, 0x8d, 0x5e,
};

const uint8_t __attribute__((section(".db_auth_key"))) _DB_PUB[] = {
  0x03,
  0xc0, 0x45, 0xd1, 0x51, 0xd2, 0xdd, 0x7f, 0x58, 0x93, 0x5f, 0x70, 0x77, 0x72, 0x93, 0xbf, 0x35,
  0xbd, 0xe9, 0x42, 0xba, 0xa4, 0xa9, 0xf4, 0xc4, 0x5b, 0x6e, 0x58, 0xd6, 0xdb, 0x70, 0x00, 0x45,
};

const uint8_t __attribute__((section(".keycard_ca_key"))) _KEYCARD_CA_PUB[] = {
  0x02,
  0x9a, 0xb9, 0x9e, 0xe1, 0xe7, 0xa7, 0x1b, 0xdf, 0x45, 0xb3, 0xf9, 0xc5, 0x8c, 0x99, 0x86, 0x6f,
  0xf1, 0x29, 0x4d, 0x2c, 0x1e, 0x30, 0x4e, 0x22, 0x8a, 0x86, 0xe1, 0x0c, 0x33, 0x43, 0x50, 0x1c,
};

app_err_t key_read_private(key_type_t type, uint8_t* out) {
  switch(type) {
  case DEV_AUTH_PRIV_KEY:
    hal_derive_device_unique_secret(_DEV_AUTH_SALT, out);
    break;
  case PAIRING_ENC_PRIV_KEY:
    hal_derive_device_unique_secret(_PAIRING_ENC_SALT, out);
    break;
  default:
    return ERR_DATA;
  }

  return ERR_OK;
}

app_err_t key_read_public(key_type_t type, const uint8_t** out) {
  switch(type) {

  case DEV_AUTH_SERVER_KEY:
    *out = _DEV_AUTH_SERVER;
    break;
  case FW_VERIFICATION_KEY:
    *out = (uint8_t*)(HAL_FLASH_ADDR + HAL_FW_HEADER_OFFSET);
    break;
  case DB_VERIFICATION_KEY:
    *out = _DB_PUB;
    break;
  case KEYCARD_CA_KEY:
    *out = _KEYCARD_CA_PUB;
    break;
  default:
    return ERR_DATA;
  }

  return ERR_OK;
}
