keycard-tech/keycard-shell/app/ui/ui.c

#include "crypto/rand.h"
#include "mem.h"
#include "error.h"
#include "ui.h"
#include "ui_internal.h"

#define MNEMO_WORDS_TO_CONFIRM 4
#define MNEMO_CHOICE_COUNT 3

core_evt_t ui_qrscan(ur_type_t type, void* out) {
  g_ui_cmd.type = UI_CMD_QRSCAN;
  g_ui_cmd.params.qrscan.out = out;
  g_ui_cmd.params.qrscan.type = type;
  return ui_signal_wait(0);
}

core_evt_t ui_qrscan_tx(ur_type_t* type, void* out) {
  core_evt_t res = ui_qrscan(UR_ANY_TX, out);
  *type = g_ui_cmd.params.qrscan.type;
  return res;
}

core_evt_t ui_menu(const char* title, const menu_t* menu, i18n_str_id_t* selected, i18n_str_id_t marked, uint8_t allow_usb, ui_menu_opt_t opts, uint8_t current_page, uint8_t last_page) {
  g_ui_cmd.type = UI_CMD_MENU;
  g_ui_cmd.params.menu.title = title;
  g_ui_cmd.params.menu.menu = menu;
  g_ui_cmd.params.menu.selected = selected;
  g_ui_cmd.params.menu.marked = marked;
  g_ui_cmd.params.menu.options = opts;
  g_ui_cmd.params.menu.current_page = current_page;
  g_ui_cmd.params.menu.last_page = last_page;
  return ui_signal_wait(allow_usb);
}

core_evt_t ui_display_eth_tx(const uint8_t* address, const txContent_t* tx) {
  g_ui_cmd.type = UI_CMD_DISPLAY_ETH_TX;
  g_ui_cmd.params.eth_tx.addr = address;
  g_ui_cmd.params.eth_tx.tx = tx;
  return ui_signal_wait(0);
}

core_evt_t ui_display_btc_tx(const btc_tx_ctx_t* tx) {
  g_ui_cmd.type = UI_CMD_DISPLAY_BTC_TX;
  g_ui_cmd.params.btc_tx.tx = tx;
  return ui_signal_wait(0);
}

core_evt_t ui_display_msg(addr_type_t addr_type, const uint8_t* address, const uint8_t* msg, uint32_t len) {
  g_ui_cmd.type = UI_CMD_DISPLAY_MSG;
  g_ui_cmd.params.msg.addr_type = addr_type;
  g_ui_cmd.params.msg.addr = address;
  g_ui_cmd.params.msg.data = msg;
  g_ui_cmd.params.msg.len = len;
  return ui_signal_wait(0);
}

core_evt_t ui_display_eip712(const uint8_t* address, const eip712_ctx_t* eip712) {
  g_ui_cmd.type = UI_CMD_DISPLAY_EIP712;
  g_ui_cmd.params.eip712.addr = address;
  g_ui_cmd.params.eip712.data = eip712;
  return ui_signal_wait(0);
}

core_evt_t ui_display_ur_qr(const char* title, const uint8_t* data, uint32_t len, ur_type_t type) {
  g_ui_cmd.type = UI_CMD_DISPLAY_QR;
  g_ui_cmd.params.qrout.title = title;
  g_ui_cmd.params.qrout.data = data;
  g_ui_cmd.params.qrout.len = len;
  g_ui_cmd.params.qrout.type = type;
  return ui_signal_wait(0);
}

core_evt_t ui_display_address_qr(const char* title, const char* address, uint32_t* index) {
  g_ui_cmd.type = UI_CMD_DISPLAY_ADDRESS_QR;
  g_ui_cmd.params.address.title = title;
  g_ui_cmd.params.address.address = address;
  g_ui_cmd.params.address.index = index;

  return ui_signal_wait(0);
}

core_evt_t ui_display_msg_qr(const char* title, const char* msg, const char* label) {
  g_ui_cmd.type = UI_CMD_DISPLAY_MSG_QR;
  g_ui_cmd.params.qrmsg.title = title;
  g_ui_cmd.params.qrmsg.msg = msg;
  g_ui_cmd.params.qrmsg.label = label;

  return ui_signal_wait(0);
}

core_evt_t ui_info(info_icon_t icon, const char* msg, const char* subtext, ui_info_opt_t opts) {
  g_ui_cmd.type = UI_CMD_INFO;
  g_ui_cmd.params.info.icon = icon;
  g_ui_cmd.params.info.msg = msg;
  g_ui_cmd.params.info.subtext = subtext;
  g_ui_cmd.params.info.options = opts;
  return ui_signal_wait(0);
}

core_evt_t ui_prompt(const char* title, const char* msg, ui_info_opt_t opts) {
  g_ui_cmd.type = UI_CMD_PROMPT;
  g_ui_cmd.params.prompt.title = title;
  g_ui_cmd.params.prompt.msg = msg;
  g_ui_cmd.params.prompt.options = opts;
  return ui_signal_wait(0);
}

core_evt_t ui_display_paged_text(const char* title, const char* text, uint32_t len) {
  g_ui_cmd.type = UI_CMD_DISPLAY_PAGED_TEXT;
  g_ui_cmd.params.paged_text.title = title;
  g_ui_cmd.params.paged_text.text = text;
  g_ui_cmd.params.paged_text.len = len;
  return ui_signal_wait(0);
}

core_evt_t ui_wrong_auth(const char* msg, uint8_t retries) {
  size_t label_len = strlen(LSTR(PIN_LABEL_REMAINING_ATTEMPTS));
  char remaining_attempts[label_len + 2];
  remaining_attempts[0] = retries + '0';
  memcpy(&remaining_attempts[1], LSTR(PIN_LABEL_REMAINING_ATTEMPTS), label_len + 1);

  return ui_info(ICON_INFO_ERROR, msg, remaining_attempts, 0);
}

core_evt_t ui_devinfo(const char* fw_ver, const char* db_ver, const char* sn) {
  g_ui_cmd.type = UI_CMD_DEVINFO;
  g_ui_cmd.params.devinfo.fw_version = fw_ver;
  g_ui_cmd.params.devinfo.db_version = db_ver;
  g_ui_cmd.params.devinfo.sn = sn;

  return ui_signal_wait(0);
}

core_evt_t ui_dbinfo(const char* db_ver) {
  g_ui_cmd.type = UI_CMD_DBINFO;
  g_ui_cmd.params.devinfo.db_version = db_ver;

  return ui_signal_wait(0);
}

void ui_card_inserted() {

}

void ui_card_removed() {
}

void ui_card_activation_error() {
  ui_info(ICON_INFO_WARN, LSTR(INFO_CARD_FAIL_MSG), LSTR(INFO_CARD_FAIL_SUB), UI_INFO_UNDISMISSABLE);
}

void ui_card_transport_error() {
  ui_info(ICON_INFO_WARN, LSTR(INFO_CARD_ERROR_MSG), LSTR(INFO_CARD_ERROR_SUB), UI_INFO_UNDISMISSABLE);
}

void ui_card_accepted() {
}

void ui_keycard_wrong_card() {
  ui_info(ICON_INFO_ERROR, LSTR(INFO_NOT_KEYCARD_MSG), LSTR(INFO_NOT_KEYCARD_SUB), UI_INFO_UNDISMISSABLE);
}

void ui_keycard_old_card() {
  ui_info(ICON_INFO_ERROR, LSTR(INFO_OLD_KEYCARD_MSG), LSTR(INFO_OLD_KEYCARD_SUB), UI_INFO_UNDISMISSABLE);
}

void ui_keycard_not_initialized() {
}

void ui_keycard_init_ok(bool has_duress) {
  if (has_duress) {
    ui_info(ICON_INFO_SUCCESS, LSTR(DURESS_OK_MSG), LSTR(DURESS_OK_SUB), 0);
  } else {
    ui_info(ICON_INFO_SUCCESS, LSTR(PIN_CHANGE_SUCCESS), NULL, 0);
  }
}

void ui_keycard_init_failed() {
}

void ui_keycard_no_keys() {
}

void ui_keycard_ready() {
}

void ui_keycard_paired(bool default_pass) {
  if (!default_pass) {
    ui_info(ICON_INFO_SUCCESS, LSTR(INFO_CARD_PAIRED), NULL, 0);
  }
}

void ui_keycard_already_paired() {
}

core_evt_t ui_keycard_pairing_failed(const char* card_name, bool default_pass) {
  if (default_pass) {
    return CORE_EVT_UI_OK;
  }

  ui_info(ICON_INFO_ERROR, LSTR(INFO_WRONG_PAIRING), LSTR(INFO_TRY_AGAIN), 0);

  i18n_str_id_t selected = MENU_PAIR;
  while (ui_menu(card_name, &menu_keycard_pair, &selected, -1, 0, UI_MENU_NOCANCEL, 0, 0) != CORE_EVT_UI_OK) {
    ;
  }

  return selected == MENU_RESET_CARD ? CORE_EVT_UI_CANCELLED : CORE_EVT_UI_OK;
}

void ui_keycard_flash_failed() {
}

void ui_keycard_secure_channel_failed() {
}

void ui_keycard_secure_channel_ok() {
}

void ui_keycard_pin_ok() {
}

void ui_keycard_puk_ok() {
}

void ui_keycard_wrong_pin(uint8_t retries) {
  if (retries > 0) {
    ui_wrong_auth(LSTR(PIN_WRONG_WARNING), retries);
  } else {
    ui_info(ICON_INFO_ERROR, LSTR(INFO_KEYCARD_BLOCKED), NULL, 0);
  }
}

void ui_keycard_wrong_puk(uint8_t retries) {
  ui_wrong_auth(LSTR(PUK_WRONG_WARNING), retries);
}

core_evt_t ui_keycard_not_genuine() {
  return ui_info(ICON_INFO_WARN, LSTR(INFO_NOT_GENUINE_MSG), LSTR(INFO_NOT_GENUINE_SUB), UI_INFO_CANCELLABLE);
}

core_evt_t ui_prompt_try_puk() {
  i18n_str_id_t selected = MENU_UNBLOCK_PUK;
  while (ui_menu(LSTR(INFO_KEYCARD_BLOCKED), &menu_keycard_blocked, &selected, -1, 0, UI_MENU_NOCANCEL, 0, 0) != CORE_EVT_UI_OK) {
    ;
  }

  return selected == MENU_RESET_CARD ? CORE_EVT_UI_CANCELLED : CORE_EVT_UI_OK;
}

core_evt_t ui_confirm_factory_reset() {
  return ui_prompt(LSTR(FACTORY_RESET_TITLE), LSTR(FACTORY_RESET_WARNING), (UI_INFO_CANCELLABLE | UI_INFO_DANGEROUS));
}

core_evt_t ui_keycard_no_pairing_slots() {
  return ui_info(ICON_INFO_ERROR, LSTR(INFO_NO_PAIRING_SLOTS_MSG), LSTR(INFO_NO_PAIRING_SLOTS_SUB), 0);
}

core_evt_t ui_read_secret(ui_secret_type_t type, uint8_t* out, int8_t retries, uint8_t dismissable) {
  g_ui_cmd.type = UI_CMD_INPUT_SECRET;
  g_ui_cmd.params.input_secret.type = type;
  g_ui_cmd.params.input_secret.dismissable = dismissable;
  g_ui_cmd.params.input_secret.retries = retries;
  g_ui_cmd.params.input_secret.out = out;

  return ui_signal_wait(0);
}

core_evt_t ui_read_pin(uint8_t* out, int8_t retries, uint8_t dismissable) {
  return ui_read_secret(UI_SECRET_PIN, out, retries, dismissable);
}

core_evt_t ui_read_duress_pin(uint8_t* out) {
  do {
    if (ui_prompt(LSTR(DURESS_PROMPT_TITLE), LSTR(DURESS_PROMPT_MSG), UI_INFO_SKIPPABLE | UI_INFO_DANGEROUS) == CORE_EVT_UI_CANCELLED) {
      return CORE_EVT_UI_CANCELLED;
    }
  } while(ui_read_secret(UI_SECRET_DURESS, out, SECRET_NEW_CODE, 1) != CORE_EVT_UI_OK);

  return CORE_EVT_UI_OK;
}

core_evt_t ui_read_puk(uint8_t* out, int8_t retries, uint8_t dismissable) {
  return ui_read_secret(UI_SECRET_PUK, out, retries, dismissable);
}

core_evt_t ui_read_pairing(uint8_t* pairing, uint8_t *len) {
  return ui_read_string(LSTR(PAIRING_INPUT_TITLE), LSTR(PROMPT_PAIRING), (char*) pairing, len, UI_READ_STRING_UNDISMISSABLE);
}

core_evt_t ui_read_string(const char* title, const char* prompt, char* out, uint8_t* len, ui_read_string_opt_t opts) {
  g_ui_cmd.type = UI_CMD_INPUT_STRING;
  g_ui_cmd.params.input_string.title = title;
  g_ui_cmd.params.input_string.prompt = prompt;
  g_ui_cmd.params.input_string.out = out;
  g_ui_cmd.params.input_string.len = len;
  g_ui_cmd.params.input_string.options = opts;

  return ui_signal_wait(0);
}

core_evt_t ui_read_number(const char* title, uint32_t min, uint32_t max, uint32_t* num, bool show_max) {
  g_ui_cmd.type = UI_CMD_INPUT_NUMBER;
  g_ui_cmd.params.input_number.title = title;
  g_ui_cmd.params.input_number.min = min;
  g_ui_cmd.params.input_number.max = max;
  g_ui_cmd.params.input_number.num = num;
  g_ui_cmd.params.input_number.show_max = show_max;

  return ui_signal_wait(0);
}

core_evt_t ui_read_number_direct(const char* title, uint32_t* num) {
  g_ui_cmd.type = UI_CMD_INPUT_NUMBER_DIRECT;
  g_ui_cmd.params.input_number_direct.title = title;
  g_ui_cmd.params.input_number_direct.num = num;

  return ui_signal_wait(0);
}

void ui_seed_loaded() {
  ui_info(ICON_INFO_SUCCESS, LSTR(INFO_KEYCARD_LOADED_MSG), LSTR(INFO_KEYCARD_LOADED_SUB), 0);
}

void ui_bad_seed() {
  ui_info(ICON_INFO_ERROR, LSTR(INFO_KEYCARD_BAD_SEED_MSG), LSTR(INFO_TRY_AGAIN), 0);
}

core_evt_t ui_scan_mnemonic(uint16_t* indexes, uint32_t* len) {
  data_t qr;

  if (ui_qrscan(NO_UR, &qr) != CORE_EVT_UI_OK) {
    return CORE_EVT_UI_CANCELLED;
  }

  bool ok;
  switch ((uint8_t) g_ui_cmd.params.qrscan.type) {
  case QUIRC_DATA_TYPE_NUMERIC:
    ok = mnemonic_from_seedqr_standard(indexes, len, (char*) qr.data, qr.len);
    break;
  case QUIRC_DATA_TYPE_BYTE:
    if (qr.len <= 32) {
      ok = mnemonic_from_data(indexes, len, qr.data, qr.len);
    } else {
      ok = mnemonic_from_string(indexes, len, (char*) qr.data);
    }
    break;
  default:
    ok = false;
    break;
  }

  if (ok && mnemonic_check(indexes, *len)) {
    return ui_display_mnemonic(LSTR(MNEMO_VERIFY_TITLE), indexes, *len, BIP39_WORDLIST_ENGLISH, BIP39_WORD_COUNT);
  } else {
    *len = 0;
    ui_info(ICON_INFO_ERROR, LSTR(QRSEED_INVALID_MSG), LSTR(QRSEED_INVALID_SUB), 0);
    return ui_scan_mnemonic(indexes, len);
  }
}

i18n_str_id_t ui_read_mnemonic_len(uint32_t* len, bool* has_pass) {
  i18n_str_id_t mode_selected = MENU_MNEMO_IMPORT;

  while(1) {
    if (ui_menu(LSTR(MNEMO_TITLE), &menu_mnemonic, &mode_selected, -1, 0, UI_MENU_NOCANCEL, 0, 0) == CORE_EVT_UI_OK) {
      const menu_t* next_menu = &menu_mnemonic_length;
      i18n_str_id_t selected = MENU_MNEMO_12WORDS;

      if (mode_selected == MENU_MNEMO_SCAN) {
        next_menu = &menu_mnemonic_has_pass;
        selected = MENU_MNEMO_WITH_PASS;
      }

      if (ui_menu(LSTR(mode_selected), next_menu, &selected, -1, 0, UI_MENU_NOCANCEL, 0, 0) == CORE_EVT_UI_OK) {
        switch(selected) {
        case MENU_MNEMO_WITH_PASS:
          *len = 0;
          *has_pass = true;
          break;
        case MENU_MNEMO_NO_PASS:
          *len = 0;
          *has_pass = false;
          break;
        case MENU_MNEMO_12WORDS:
          *has_pass = false;
          *len = 12;
          break;
        case MENU_MNEMO_12WORDS_PASS:
          *has_pass = true;
          *len = 12;
          break;
        case MENU_MNEMO_24WORDS:
          *has_pass = false;
          *len = 24;
          break;
        case MENU_MNEMO_24WORDS_PASS:
          *has_pass = true;
          *len = 24;
          break;
        case MENU_MNEMO_SLIP39:
          *has_pass = false;
          *len = 20;
          break;
        case MENU_MNEMO_SLIP39_PASS:
        default:
          *has_pass = true;
          *len = 20;
          break;
        }

        return mode_selected;
      }
    }
  }
}

core_evt_t ui_read_mnemonic_verify(uint32_t* len) {
  i18n_str_id_t selected = MENU_MNEMO_12WORDS;
  core_evt_t res = ui_menu(LSTR(MNEMO_VERIFY_TITLE), &menu_verify_mnemonic, &selected, -1, 0, 0, 0, 0);
  
  if (res == CORE_EVT_UI_OK) {
    switch(selected) {
    case MENU_MNEMO_12WORDS:
      *len = 12;
      break;
    case MENU_MNEMO_24WORDS:
      *len = 24;
      break;
    case MENU_MNEMO_SCAN:
      *len = 0;  // QR scan
      break;
    case MENU_MNEMO_SLIP39:
      *len = SLIP39_MNEMO_LEN;
      break;
    default:
      res = CORE_EVT_UI_CANCELLED;
      break;
    }
  }

  return res;
}

core_evt_t ui_read_bip39(uint16_t indexes[BIP39_MAX_MNEMONIC_LEN], size_t mnemo_len) {
  while (1) {
    if (ui_read_mnemonic(indexes, mnemo_len, BIP39_WORDLIST_ENGLISH, BIP39_WORD_COUNT) != CORE_EVT_UI_OK) {
      return CORE_EVT_UI_CANCELLED;
    }

    if (!mnemonic_check(indexes, mnemo_len)) {
      ui_bad_seed();
    } else {
      return CORE_EVT_UI_OK;
    }
  }
}

core_evt_t ui_read_slip39(slip39_shard_t shards[SLIP39_MAX_MEMBERS], uint16_t indexes[SLIP39_MNEMO_LEN], uint8_t ems[SLIP39_SEED_STRENGTH]) {
  uint8_t shard_idx = 0;
  uint8_t shard_count = 1;
  const char* part_success = LSTR(INFO_SLIP39_PART_OK_SUB);
  size_t part_success_len = strlen(part_success);
  char part_counter_msg[part_success_len + 3];
  memcpy(&part_counter_msg[2], part_success, part_success_len + 1);

  while(shard_idx < shard_count) {
    if (ui_read_mnemonic(indexes, SLIP39_MNEMO_LEN, SLIP39_WORDLIST, SLIP39_WORDS_COUNT) != CORE_EVT_UI_OK) {
      return CORE_EVT_UI_CANCELLED;
    }

    if (slip39_decode_mnemonic(indexes, SLIP39_MNEMO_LEN, &shards[shard_idx]) < 0) {
      ui_bad_seed();
    } else if ((shards[0].identifier != shards[shard_idx].identifier) || (shards[0].group_index != shards[shard_idx].group_index)) {
      ui_info(ICON_INFO_ERROR, LSTR(INFO_SLIP39_MISMATCH_MSG), LSTR(INFO_SLIP39_MISMATCH_SUB), 0);
    } else if (shards[0].group_threshold != 1) {
      ui_info(ICON_INFO_ERROR, LSTR(INFO_SLIP39_UNSUPPORTED_MSG), LSTR(INFO_SLIP39_UNSUPPORTED_SUB), 0);
    } else {
      memset(&indexes[3], 0xff, sizeof(uint16_t) * (SLIP39_MNEMO_LEN - 3));

      shard_count = shards[0].member_threshold;
      shard_idx++;

      uint8_t parts_left = shard_count - shard_idx;

      if (parts_left) {
        int off = 1;
        part_counter_msg[off--] = '0' + (parts_left % 9);
        if (parts_left > 9) {
          part_counter_msg[off--] = '1';
        }

        ui_info(ICON_INFO_SUCCESS, LSTR(INFO_SLIP39_PART_OK_MSG), &part_counter_msg[off + 1], 0);
      }
    }
  }

  if (slip39_combine(shards, shard_count, ems, SLIP39_SEED_STRENGTH) < 0) {
    ui_bad_seed();
    return CORE_EVT_UI_CANCELLED;
  }

  return CORE_EVT_UI_OK;
}

core_evt_t ui_display_mnemonic(const char* title, uint16_t* indexes, uint32_t len, const char* const* wordlist, size_t wordcount) {
  g_ui_cmd.type = UI_CMD_DISPLAY_MNEMO;
  g_ui_cmd.params.mnemo.title = title;
  g_ui_cmd.params.mnemo.indexes = indexes;
  g_ui_cmd.params.mnemo.len = len;
  g_ui_cmd.params.mnemo.wordlist = wordlist;
  g_ui_cmd.params.mnemo.wordlist_len = wordcount;

  return ui_signal_wait(0);
}

static app_err_t ui_backup_confirm_mnemonic(uint16_t* indexes, uint32_t len, const char* const* wordlist, size_t wordcount, bool prompt) {
  const char* const* tmp = *i18n_strings;

  if (prompt && (ui_prompt(LSTR(MNEMO_VERIFY_TITLE), LSTR(MNEMO_VERIFY_PROMPT), UI_INFO_CANCELLABLE) != CORE_EVT_UI_OK)) {
    return ERR_CANCEL;
  }

  uint8_t positions[MNEMO_WORDS_TO_CONFIRM];
  random_unique_in_range(len, MNEMO_WORDS_TO_CONFIRM, positions);

  const char* base_title = LSTR(MNEMO_WORD_BACKUP_TITLE);
  size_t base_len = strlen(base_title);
  char title[strlen(base_title) + 4];
  memcpy(title, base_title, base_len);
  title[base_len + 2] = '\0';

  menu_t* choices = (menu_t*)g_mem_heap;
  choices->len = MNEMO_CHOICE_COUNT;

  int retries = 3;

  for (int i = 0; i < MNEMO_WORDS_TO_CONFIRM; i++) {
    uint8_t pos = positions[i] + 1;

    if (pos > 9) {
      title[base_len] = (pos / 10) + '0';
      title[base_len+1] = (pos % 10) + '0';
    } else {
      title[base_len] = (pos % 10) + '0';
      title[base_len+1] = '\0';
    }

    bool correct_included = false;

    for (int j = 0; j < MNEMO_CHOICE_COUNT; j++) {
      choices->entries[j].submenu = NULL;

      bool duplicate;

      do {
        duplicate = false;
        choices->entries[j].label_id = random_uniform(wordcount);
        for(int k = 0; k < j; k++) {
          if (choices->entries[j].label_id == choices->entries[k].label_id) {
            duplicate = true;
            break;
          }
        }
      } while(duplicate);

      if (choices->entries[j].label_id == indexes[pos - 1]) {
        correct_included = true;
      }
    }

    if (!correct_included) {
      choices->entries[random_uniform(MNEMO_CHOICE_COUNT)].label_id = indexes[pos - 1];
    }

    bool correct = false;

    do {
      i18n_str_id_t selected = choices->entries[0].label_id;

      i18n_set_strings(wordlist);
      core_evt_t err = ui_menu(title, choices, &selected, -1, 0, UI_MENU_PAGED, i, (MNEMO_WORDS_TO_CONFIRM - 1));
      i18n_set_strings(tmp);

      if (err != CORE_EVT_UI_OK) {
        return ERR_CANCEL;
      }

      if (selected != indexes[pos - 1]) {
        if (--retries == 0) {
          ui_info(ICON_INFO_ERROR, LSTR(MNEMO_MISMATCH_LIMIT), LSTR(MNEMO_MISMATCH_RETRY), 0);
          return ERR_CANCEL;
        } else {
          ui_wrong_auth(LSTR(MNEMO_MISMATCH), retries);
        }
      } else {
        correct = true;
      }
    } while(!correct);
  }

  return ERR_OK;
}

core_evt_t ui_backup_mnemonic(uint16_t* indexes, uint32_t len, const char* const* wordlist, size_t wordcount, bool prompt_confirm) {
  do {
    if (ui_display_mnemonic(LSTR(INFO_WRITE_KEEP_SAFE), indexes, len, wordlist, wordcount) == CORE_EVT_UI_CANCELLED) {
      return CORE_EVT_UI_CANCELLED;
    }
  } while(ui_backup_confirm_mnemonic(indexes, len, wordlist, wordcount, prompt_confirm) != ERR_OK);

  return CORE_EVT_UI_OK;
}

core_evt_t ui_read_mnemonic(uint16_t* indexes, uint32_t len, const char* const* wordlist, size_t wordcount) {
  g_ui_cmd.type = UI_CMD_INPUT_MNEMO;
  g_ui_cmd.params.mnemo.indexes = indexes;
  g_ui_cmd.params.mnemo.len = len;
  g_ui_cmd.params.mnemo.wordlist = wordlist;
  g_ui_cmd.params.mnemo.wordlist_len = wordcount;

  return ui_signal_wait(0);
}

core_evt_t ui_confirm_export_key() {
  return ui_prompt(LSTR(PUBKEY_EXPORT_TITLE), LSTR(PUBKEY_EXPORT_MSG), UI_INFO_CANCELLABLE);
}

core_evt_t ui_device_auth(uint32_t first_auth, uint32_t auth_time, uint32_t auth_count) {
  return ui_info(ICON_INFO_SUCCESS, LSTR(DEV_AUTH_INFO_SUCCESS_MSG), LSTR(DEV_AUTH_INFO_SUCCESS_SUB), 0);
}

core_evt_t ui_settings_brightness(uint8_t* brightness) {
  g_ui_cmd.type = UI_CMD_LCD_BRIGHTNESS;
  g_ui_cmd.params.lcd.brightness = brightness;

  return ui_signal_wait(0);
}

void ui_update_progress(const char* title, uint8_t progress) {
  g_ui_cmd.type = UI_CMD_PROGRESS;
  g_ui_cmd.params.progress.title = title;
  g_ui_cmd.params.progress.value = progress;

  return ui_signal();
}

core_evt_t ui_verify_address(ui_verify_match_fn_t match, void* ctx, bool* found) {
  g_ui_cmd.type = UI_CMD_VERIFY_ADDRESS;
  g_ui_cmd.params.verify_address.match = match;
  g_ui_cmd.params.verify_address.ctx = ctx;
  g_ui_cmd.params.verify_address.found = found;

  return ui_signal_wait(0);
}
