keycard-tech/keycard-shell/app/ui/dialog.c

#include "dialog.h"
#include "crypto/address.h"
#include "crypto/bignum.h"
#include "crypto/script.h"
#include "crypto/util.h"
#include "ethereum/eth_data.h"
#include "ethereum/eth_db.h"
#include "ethereum/ethUstream.h"
#include "mem.h"
#include "theme.h"
#include "pwr.h"
#include "ui/i18n.h"
#include "ui/ui_internal.h"

#define TX_CONFIRM_TIMEOUT 180000
#define BIGNUM_STRING_LEN 100
#define MAX_PAGE_COUNT 120
#define MESSAGE_MAX_X (SCREEN_WIDTH - TH_TEXT_HORIZONTAL_MARGIN)
#define MESSAGE_MAX_Y (SCREEN_HEIGHT - TH_NAV_HINT_HEIGHT - 16)
#define DATA_FIELD_MAX_LEN 23

#define BTC_DIALOG_PAGE_ITEMS 1

typedef struct {
  uint16_t page;
  uint16_t last_page;
  uint16_t pages[MAX_PAGE_COUNT];
} pager_ctx_t;

app_err_t dialog_wait_dismiss(ui_info_opt_t opts) {
  icon_t left = opts & UI_INFO_CANCELLABLE ? ICON_NAV_CANCEL : ICON_NONE;
  icon_t right;

  if (opts & UI_INFO_DANGEROUS) {
    right = ICON_NAV_NEXT_HOLD;
  } else {
    right = ICON_NAV_NEXT;
  }

  dialog_nav_hints(left, right);

  if (opts & UI_INFO_DANGEROUS) {
    screen_text_ctx_t ctx = { .font = TH_FONT_TEXT, .bg = TH_COLOR_BG, .fg = TH_COLOR_ACCENT, .x = TH_NAV_HINT_INPUT_PROCEED_RIGHT_X, .y = TH_NAV_HINT_INPUT_TOP };
    screen_draw_string(&ctx, LSTR(INPUT_NAV_PROCEED));
  }

  if ((opts & UI_INFO_SKIPPABLE) == UI_INFO_SKIPPABLE) {
    screen_text_ctx_t ctx = { .font = TH_FONT_TEXT, .bg = TH_COLOR_BG, .fg = TH_COLOR_FG, .x = TH_NAV_HINT_INPUT_LEFT_X, .y = TH_NAV_HINT_INPUT_TOP };
    screen_draw_string(&ctx, LSTR(INPUT_NAV_SKIP));
  }

  while(1) {
    switch(ui_wait_keypress(portMAX_DELAY)) {
    case KEYPAD_KEY_CANCEL:
      return opts & UI_INFO_CANCELLABLE ? ERR_CANCEL : ERR_OK;
    case KEYPAD_KEY_BACK:
      if (opts & UI_INFO_CANCELLABLE) {
        return ERR_CANCEL;
      }
      break;
    case KEYPAD_KEY_CONFIRM:
      if (!(opts & UI_INFO_DANGEROUS) || g_ui_ctx.keypad.last_key_long) {
        return ERR_OK;
      }
      break;
    default:
      break;
    }
  }
}

static app_err_t dialog_wait_paged(uint16_t* page, uint16_t last_page) {
  dialog_nav_hints(ICON_NAV_CANCEL, ICON_NAV_NEXT);
  dialog_pager(*page, last_page, true);

  switch(ui_wait_keypress(pdMS_TO_TICKS(TX_CONFIRM_TIMEOUT))) {
  case KEYPAD_KEY_LEFT:
    if (*page > 0) {
      (*page)--;
    } else {
      *page = last_page;
    }
    return ERR_NEED_MORE_DATA;
  case KEYPAD_KEY_RIGHT:
    if (*page < last_page) {
      (*page)++;
    } else {
      *page = 0;
    }
    return ERR_NEED_MORE_DATA;
  case KEYPAD_KEY_CANCEL:
  case KEYPAD_KEY_BACK:
  case KEYPAD_KEY_INVALID:
    return ERR_CANCEL;
  case KEYPAD_KEY_CONFIRM:
    return ERR_OK;
  default:
    return ERR_NEED_MORE_DATA;
  }
}

app_err_t dialog_begin_line(screen_text_ctx_t* ctx, uint16_t line_height) {
  screen_area_t fillarea = { 0, ctx->y, SCREEN_WIDTH, line_height };
  ctx->v1 = ctx->y;
  ctx->v2 = line_height;
  ctx->y += ((line_height - ctx->font->yAdvance) / 2);

  return screen_fill_area(&fillarea, ctx->bg) == HAL_SUCCESS? ERR_OK : ERR_HW;
}

app_err_t dialog_end_line(screen_text_ctx_t* ctx) {
  ctx->y = ctx->v1 + ctx->v2;
  return ERR_OK;
}

app_err_t dialog_inverted_string(screen_text_ctx_t* ctx, const char* str, uint16_t padding) {
  screen_area_t padarea = {
      ctx->x - padding,
      ctx->y - (padding / 2),
      screen_string_width(ctx, str) + (padding * 2),
      ctx->font->yAdvance + padding
  };

  screen_fill_area(&padarea, ctx->fg);

  uint16_t tmp = ctx->fg;
  ctx->fg = ctx->bg;
  ctx->bg = tmp;
  app_err_t err = screen_draw_string(ctx, str) == HAL_SUCCESS? ERR_OK : ERR_HW;
  ctx->bg = ctx->fg;
  ctx->fg = tmp;
  return err;
}

app_err_t dialog_title_colors(const char* title, uint16_t bg, uint16_t fg) {
  g_ui_ctx.title_bg = bg;
  screen_area_t area = { 0, 0, SCREEN_WIDTH, TH_TITLE_HEIGHT };
  screen_fill_area(&area, bg);

  screen_text_ctx_t ctx = { TH_FONT_TITLE, fg, bg, TH_TITLE_LEFT_MARGIN, TH_TITLE_TOP_MARGIN };
  screen_draw_string(&ctx, title);

  ctx.x = TH_TITLE_ICON_LEFT_MARGIN;
  ctx.y = TH_TITLE_ICON_TOP_MARGIN;

  return icon_draw_battery_indicator(&ctx, g_ui_ctx.battery);
}

app_err_t dialog_update_battery() {
  if (g_ui_ctx.title_bg == UINT32_MAX) {
    return ERR_OK;
  }

  g_ui_ctx.battery = pwr_battery_level();

  screen_area_t area = { TH_TITLE_ICON_LEFT_MARGIN, 0, (SCREEN_WIDTH - TH_TITLE_ICON_LEFT_MARGIN), TH_TITLE_HEIGHT };
  screen_fill_area(&area, g_ui_ctx.title_bg);

  screen_text_ctx_t ctx = { TH_FONT_TITLE, 0, g_ui_ctx.title_bg, TH_TITLE_ICON_LEFT_MARGIN, TH_TITLE_ICON_TOP_MARGIN };
  return icon_draw_battery_indicator(&ctx, g_ui_ctx.battery);
}

app_err_t dialog_blank_color(uint16_t yOff, uint16_t bg) {
  screen_area_t area = { 0, yOff, SCREEN_WIDTH, SCREEN_HEIGHT - yOff };
  return screen_fill_area(&area, bg) == HAL_SUCCESS? ERR_OK : ERR_HW;
}

app_err_t dialog_nav_hints_colors(icon_t left, icon_t right, uint16_t bg, uint16_t fg) {
  screen_area_t hint_area = {
      .x = 0,
      .y = SCREEN_HEIGHT - TH_NAV_HINT_HEIGHT,
      .width = TH_NAV_HINT_WIDTH,
      .height = TH_NAV_HINT_HEIGHT
  };

  screen_fill_area(&hint_area, bg);

  screen_text_ctx_t ctx = {
      .bg = bg,
      .fg = fg,
      .x = TH_NAV_HINT_LEFT_X,
      .y = TH_NAV_HINT_TOP
  };

  if (left != ICON_NONE) {
    icon_draw(&ctx, left);
  }

  hint_area.x = SCREEN_WIDTH - TH_NAV_HINT_WIDTH;
  screen_fill_area(&hint_area, bg);

  if (right != ICON_NONE) {
    ctx.bg = bg;
    ctx.fg = fg;
    ctx.x = TH_NAV_HINT_RIGHT_X;
    ctx.y = TH_NAV_HINT_TOP,
    icon_draw(&ctx, right);
  }

  return ERR_OK;
}

static app_err_t dialog_pager_internal(size_t page, size_t last_page, size_t base_page, uint16_t bg, uint16_t fg, bool chevron, uint16_t top, const font_t* font) {
  uint8_t page_indicator[(UINT32_STRING_LEN * 2) + 4];
  size_t total_len = 0;

  if (chevron) {
    page_indicator[total_len++] = SYM_LEFT_CHEVRON;
    page_indicator[total_len++] = ' ';
  }

  uint8_t page_str[UINT32_STRING_LEN];
  uint8_t* p = u32toa(page + base_page, page_str, UINT32_STRING_LEN);
  uint8_t p_len = strlen((char *) p);
  memcpy(&page_indicator[total_len], p, p_len);
  total_len += p_len;

  if (last_page != UINT32_MAX) {
    page_indicator[total_len++] = ' ';
    page_indicator[total_len++] = '/';
    page_indicator[total_len++] = ' ';

    p = u32toa(last_page + base_page, page_str, UINT32_STRING_LEN);
    p_len = strlen((char *) p);
    memcpy(&page_indicator[total_len], p, p_len);
    total_len += p_len;
  }

  if (chevron) {
    page_indicator[total_len++] = ' ';
    page_indicator[total_len++] = SYM_RIGHT_CHEVRON;
  }

  page_indicator[total_len] = '\0';

  screen_text_ctx_t ctx = {
      .x = 0,
      .y = top,
      .font = font,
      .bg = bg,
      .fg = fg,
  };

  screen_draw_centered_string(&ctx, (char*) page_indicator);
  return ERR_OK;
}

app_err_t dialog_pager_colors(size_t page, size_t last_page, size_t base_page, uint16_t bg, uint16_t fg, bool chevron) {
  return dialog_pager_internal(page, last_page, base_page, bg, fg, chevron, TH_NAV_PAGER_TOP, TH_FONT_TEXT);
}

app_err_t dialog_number_picker(uint32_t num, uint32_t max) {
  return dialog_pager_internal(num, max, 0, TH_COLOR_BG, TH_COLOR_FG, true, TH_NUM_PICKER_TOP, TH_NUM_PICKER_FONT);
}

uint16_t dialog_ordered_point(uint16_t x, uint16_t y, uint8_t index, const char* msg) {
  screen_text_ctx_t ctx = {
      .font = TH_FONT_TEXT,
      .fg = TH_TEXT_FIELD_FG,
      .bg = TH_TEXT_FIELD_BG,
      .y = y + TH_ORDER_INDEX_INNER_MARGIN
  };

  screen_area_t square = { .x = x, .y = y, .width = TH_ORDER_INDEX_SIZE, .height = TH_ORDER_INDEX_SIZE };
  screen_fill_area(&square, TH_ORDER_INDEX_COLOR);

  square.x += TH_ORDER_INDEX_INNER_MARGIN;
  square.y += TH_ORDER_INDEX_INNER_MARGIN;
  square.width -= (TH_ORDER_INDEX_INNER_MARGIN * 2);
  square.height -= (TH_ORDER_INDEX_INNER_MARGIN * 2);
  screen_fill_area(&square, TH_TEXT_FIELD_BG);

  const glyph_t* num[2];
  uint8_t numlen = 0;
  size_t numwidth = 0;

  if (index >= 10) {
    num[numlen++] = screen_lookup_glyph(ctx.font, (index / 10) + '0');
    numwidth += num[0]->xAdvance;
  }

  num[numlen++] = screen_lookup_glyph(ctx.font, (index % 10) + '0');
  numwidth += num[0]->xAdvance;

  ctx.x = x + ((TH_ORDER_INDEX_SIZE - numwidth) / 2);

  // offset integer math error
  if ((index == 10) || ((index < 20) && (index > 11))) {
    ctx.x--;
  } else if ((index == 21) || (index == 6)) {
    ctx.x++;
  }

  screen_draw_glyphs(&ctx, num, numlen);

  ctx.x = x + TH_ORDER_INDEX_SIZE + TH_ORDER_INDEX_MARGIN;
  ctx.y = y + TH_ORDER_INDEX_INNER_MARGIN;
  screen_draw_text(&ctx, MESSAGE_MAX_X, MESSAGE_MAX_Y, (uint8_t*) msg, strlen(msg), false, false);
  return ctx.y;
}

static inline void dialog_label_ctx(screen_text_ctx_t *ctx) {
  ctx->font = TH_FONT_LABEL;
  ctx->fg = TH_COLOR_LABEL_FG;
  ctx->bg = TH_COLOR_LABEL_BG;
  ctx->x = TH_TEXT_HORIZONTAL_MARGIN;
}
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
